ranseyer/CUN-STM32/Datasheets/CUBE_OWIRE.jpg

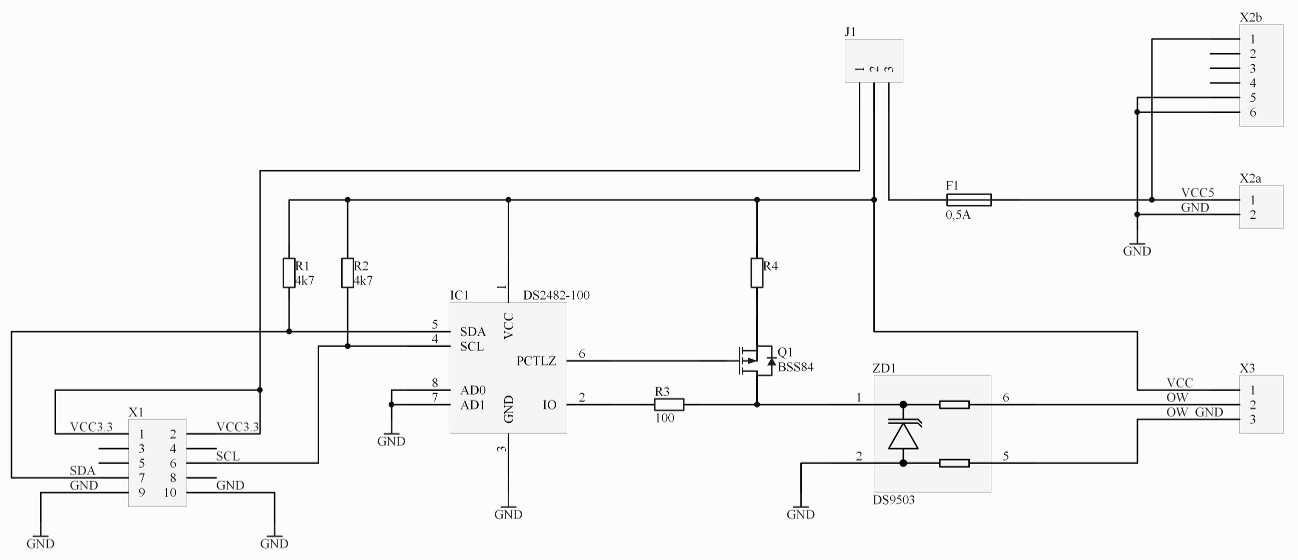
Datasheets/CUBE_OWIRE.jpg
