ranseyer/CUN-STM32/Datasheets/w5500-NiRen2.jpg

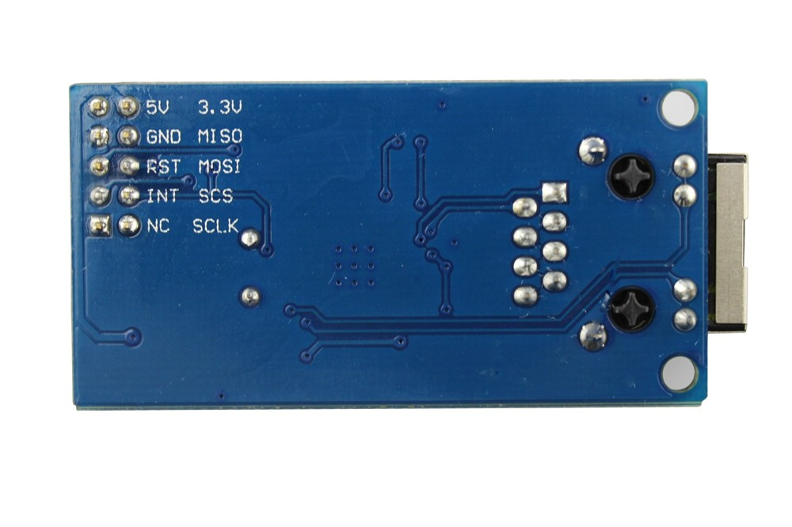
Datasheets/w5500-NiRen2.jpg
