ranseyer/CUN-STM32/Datasheets/w5500-NiRen.jpg

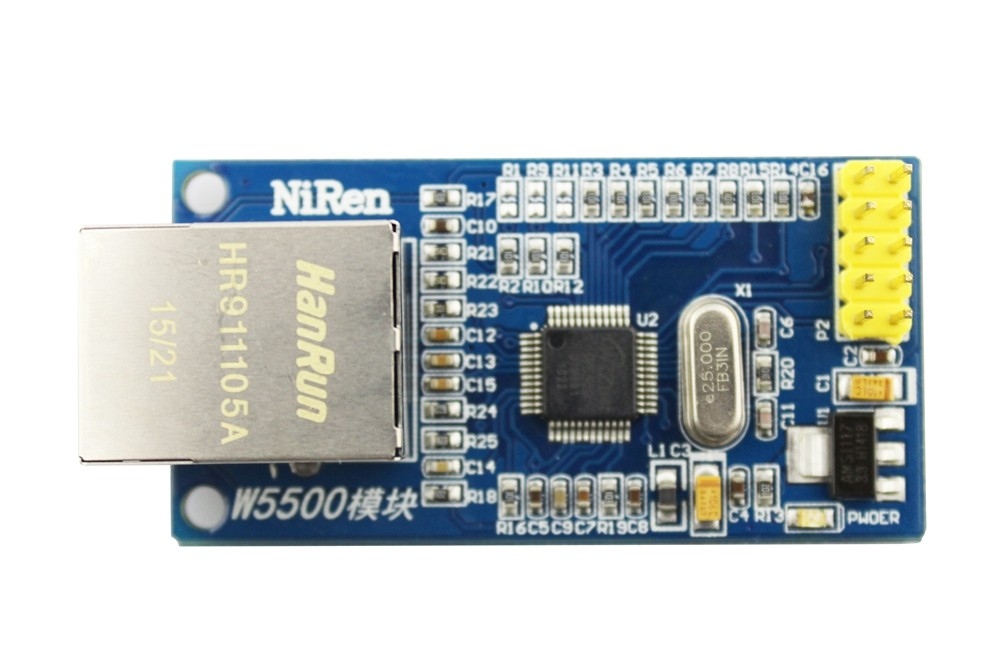
Datasheets/w5500-NiRen.jpg
