ranseyer/CUN-STM32/HW-MAPLE-Large/20161227_2025_top_gold_with_mask.png

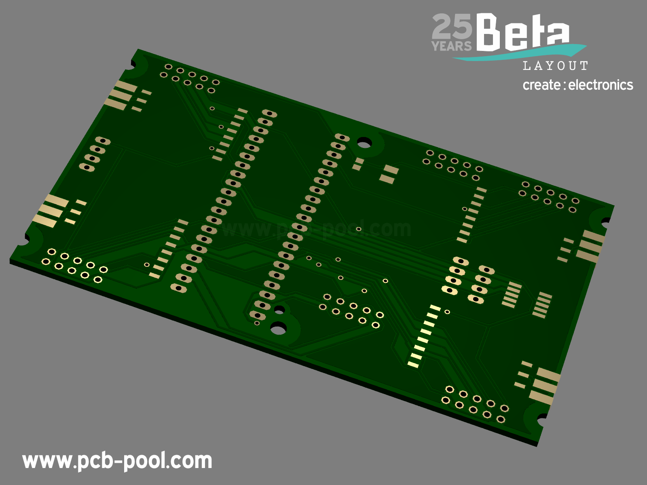
HW-MAPLE-Large/20161227_2025_top_gold_with_mask.png
