ranseyer/CUN-STM32/HW-MAPLE-Large/AddOns/1W_RS485__or__LAN-without-MAPLE/bot.png

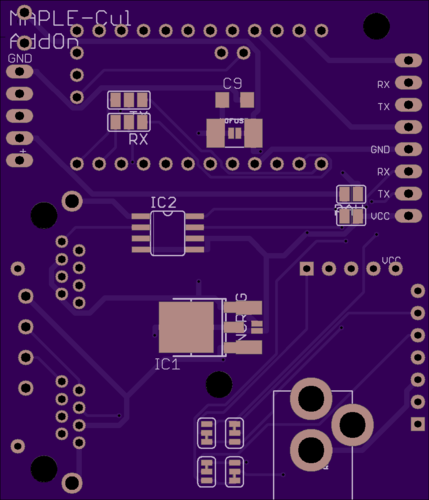
HW-MAPLE-Large/AddOns/1W_RS485__or__LAN-without-MAPLE/bot.png
