ranseyer/CUN-STM32/HW-MAPLE-Large/AddOns/1W_RS485__or__LAN-without-MAPLE/top.png

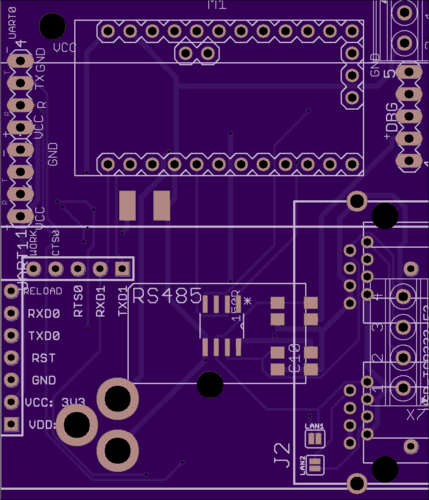
HW-MAPLE-Large/AddOns/1W_RS485__or__LAN-without-MAPLE/top.png
