ranseyer/CUN-STM32/HW-MAPLE-Large/AddOns/Overview.jpg

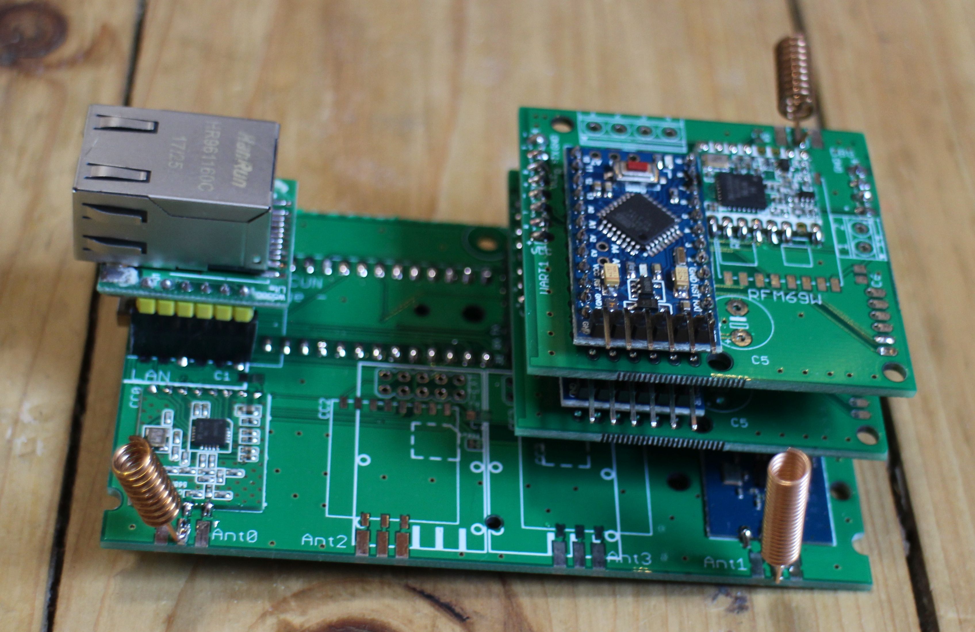
HW-MAPLE-Large/AddOns/Overview.jpg
