ranseyer/CUN-STM32/HW-MAPLE-Large/AddOns/RasPi-UART__Zigbee-CC2530/bot-v04.png

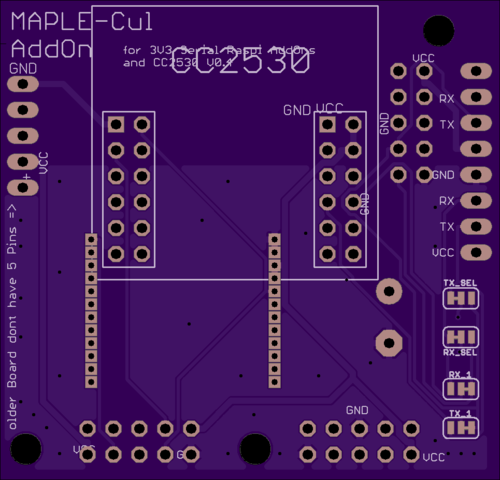
HW-MAPLE-Large/AddOns/RasPi-UART__Zigbee-CC2530/bot-v04.png
