ranseyer/CUN-STM32/HW-MAPLE-Large/AddOns/RasPi-UART__Zigbee-CC2530/bot.png

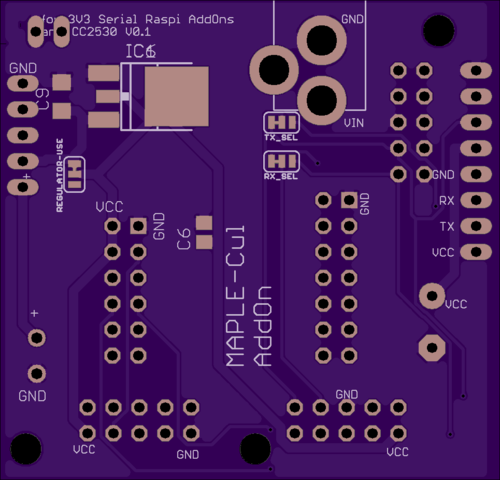
HW-MAPLE-Large/AddOns/RasPi-UART__Zigbee-CC2530/bot.png
