ranseyer/CUN-STM32/HW-MAPLE-Large/AddOns/RasPi-UART__Zigbee-CC2530/CC2530-Photo.jpg

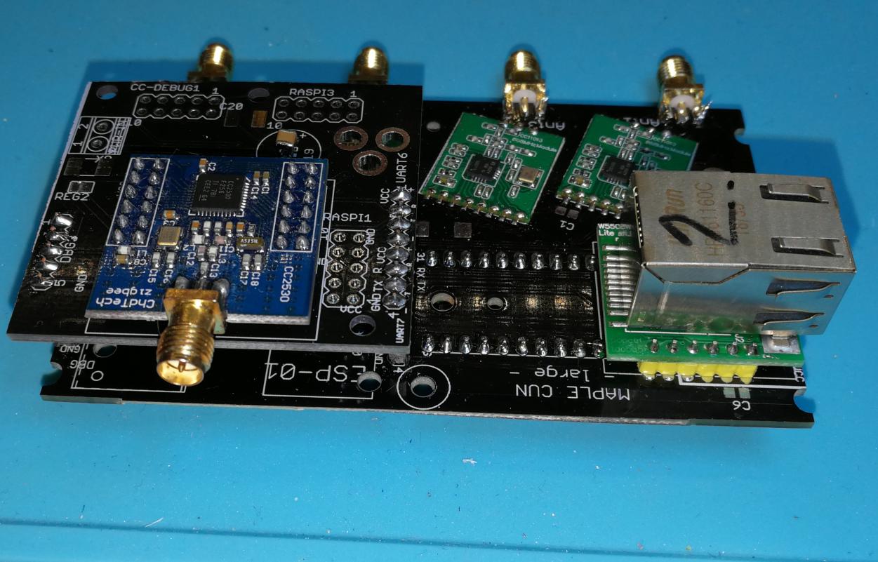
HW-MAPLE-Large/AddOns/RasPi-UART__Zigbee-CC2530/CC2530-Photo.jpg
