ranseyer/CUN-STM32/HW-MAPLE-Large/AddOns/RasPi-UART__Zigbee-CC2530/top.png

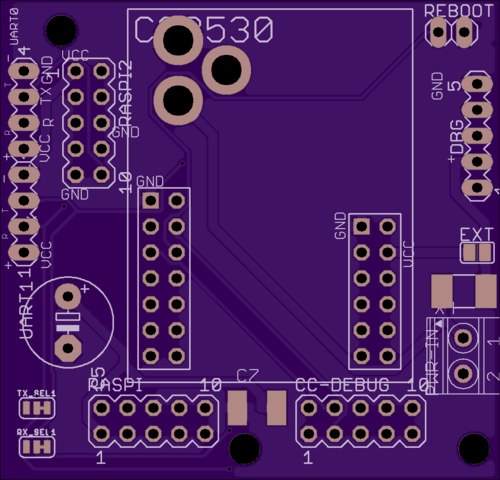
HW-MAPLE-Large/AddOns/RasPi-UART__Zigbee-CC2530/top.png
