ranseyer/CUN-STM32/HW-MAPLE-Large/AddOns/RasPi-UART__Zigbee-CC2530/Zigbee/L01_SL500_.jpg

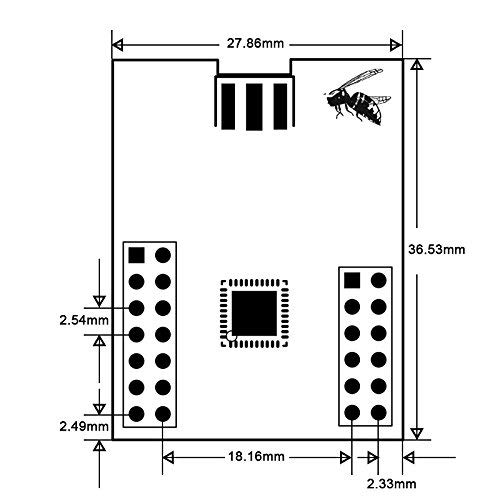
HW-MAPLE-Large/AddOns/RasPi-UART__Zigbee-CC2530/Zigbee/L01_SL500_.jpg
