ranseyer/CUN-STM32/HW-MAPLE-Large/AddOns/RFM69-usw-aktuell/top-14.png

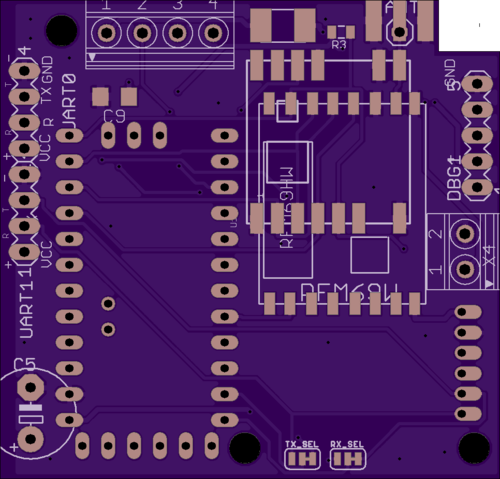
HW-MAPLE-Large/AddOns/RFM69-usw-aktuell/top-14.png
