ranseyer/CUN-STM32/HW-MAPLE-Large/AddOns/RFM69-usw-V11/bot.png

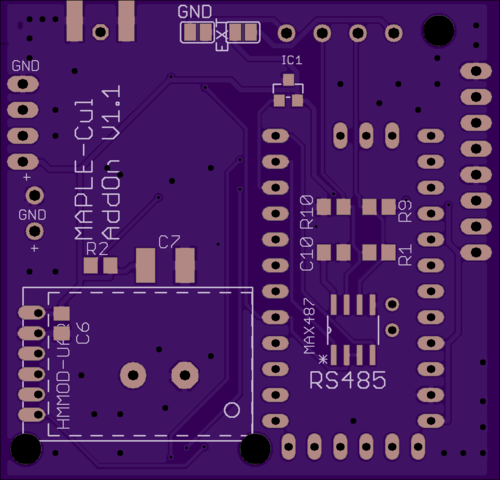
HW-MAPLE-Large/AddOns/RFM69-usw-V11/bot.png
