ranseyer/CUN-STM32/HW-MAPLE-Large/AddOns/separated.jpg

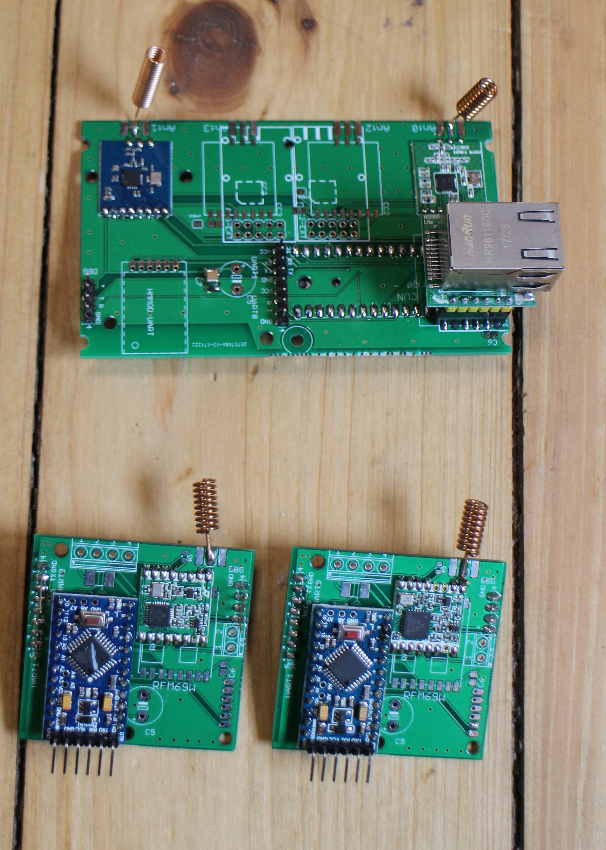
HW-MAPLE-Large/AddOns/separated.jpg
