ranseyer/CUN-STM32/HW-MAPLE-Large/AddOns/V3-Top-Add-1280.jpg

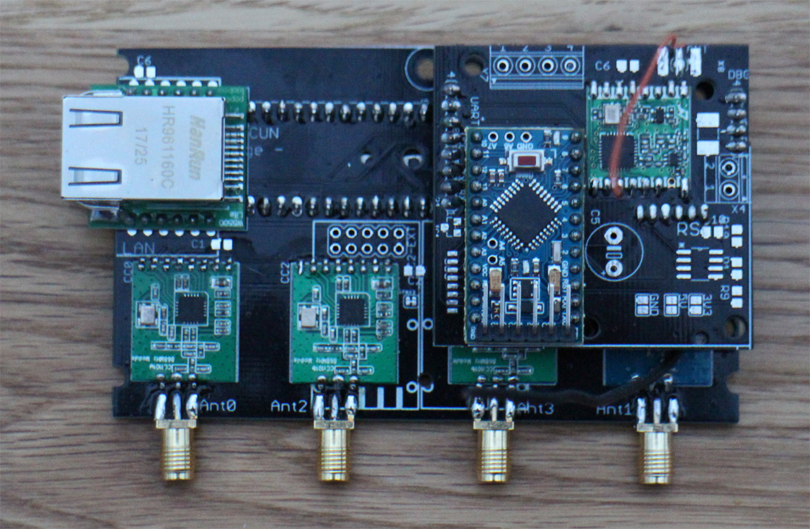
HW-MAPLE-Large/AddOns/V3-Top-Add-1280.jpg
