ranseyer/CUN-STM32/HW-MAPLE-Large/AddOns/zz_delete/1Wire-V01/PCB.png

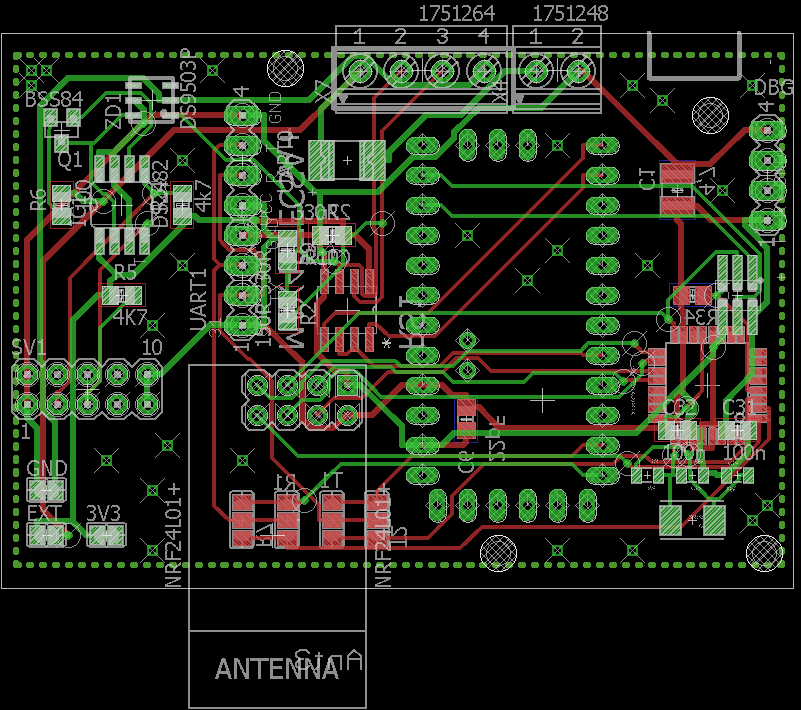
HW-MAPLE-Large/AddOns/zz_delete/1Wire-V01/PCB.png
