ranseyer/CUN-STM32/HW-MAPLE-Large/AddOns/zz_delete/1Wire-V01/Schematic.png

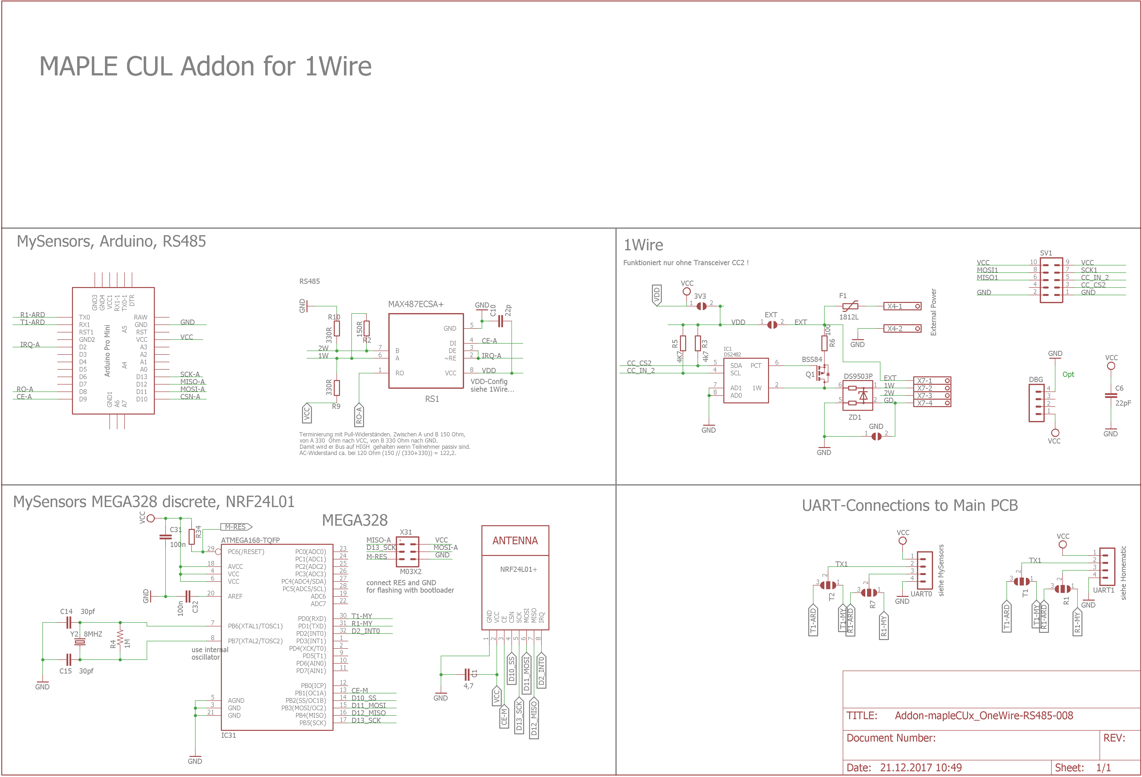
HW-MAPLE-Large/AddOns/zz_delete/1Wire-V01/Schematic.png
