ranseyer/CUN-STM32/HW-MAPLE-Large/Board-V41-bot.png

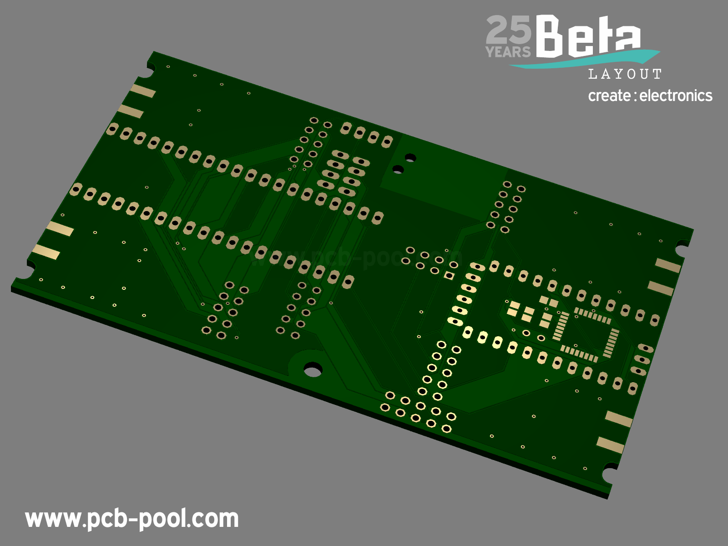
HW-MAPLE-Large/Board-V41-bot.png
