ranseyer/CUN-STM32/HW-MAPLE-Large/Board-V41-top.png

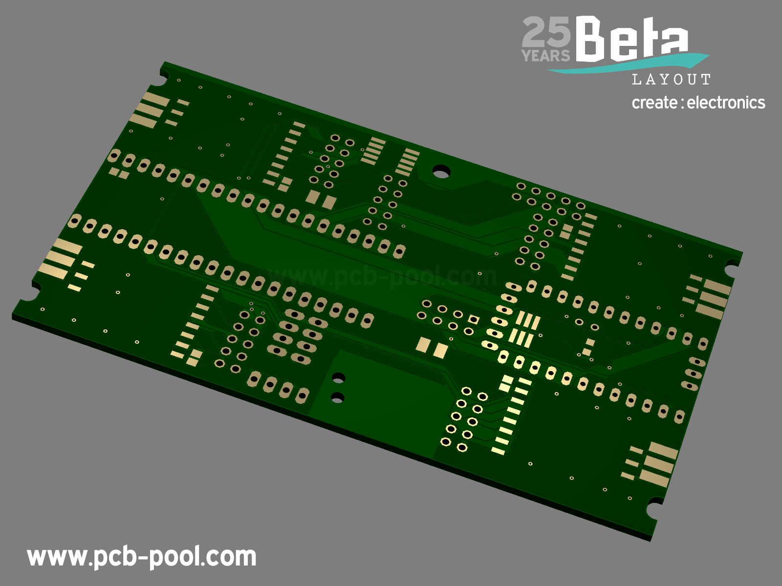
HW-MAPLE-Large/Board-V41-top.png
