ranseyer/CUN-STM32/HW-MAPLE-Large/Board-V41.png

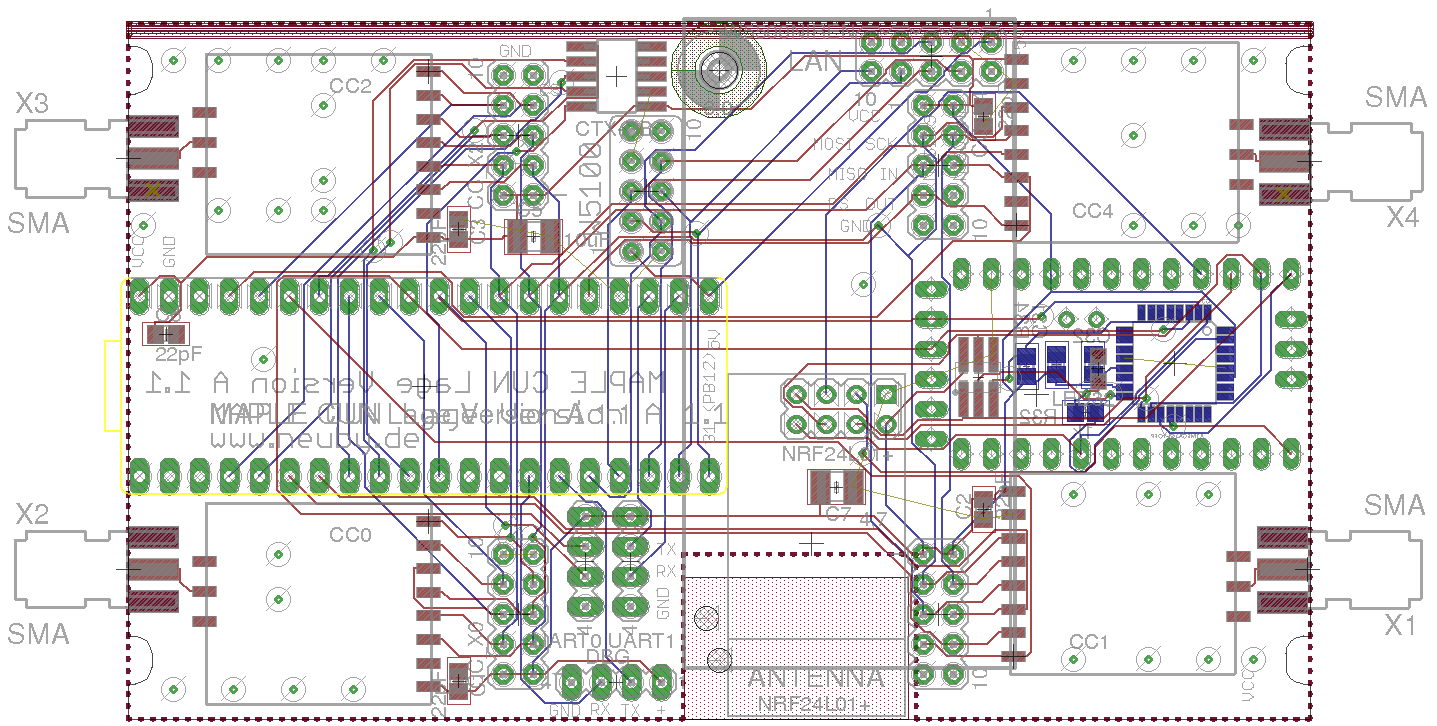
HW-MAPLE-Large/Board-V41.png
