ranseyer/CUN-STM32/HW-MAPLE-Large/Board-V102.png

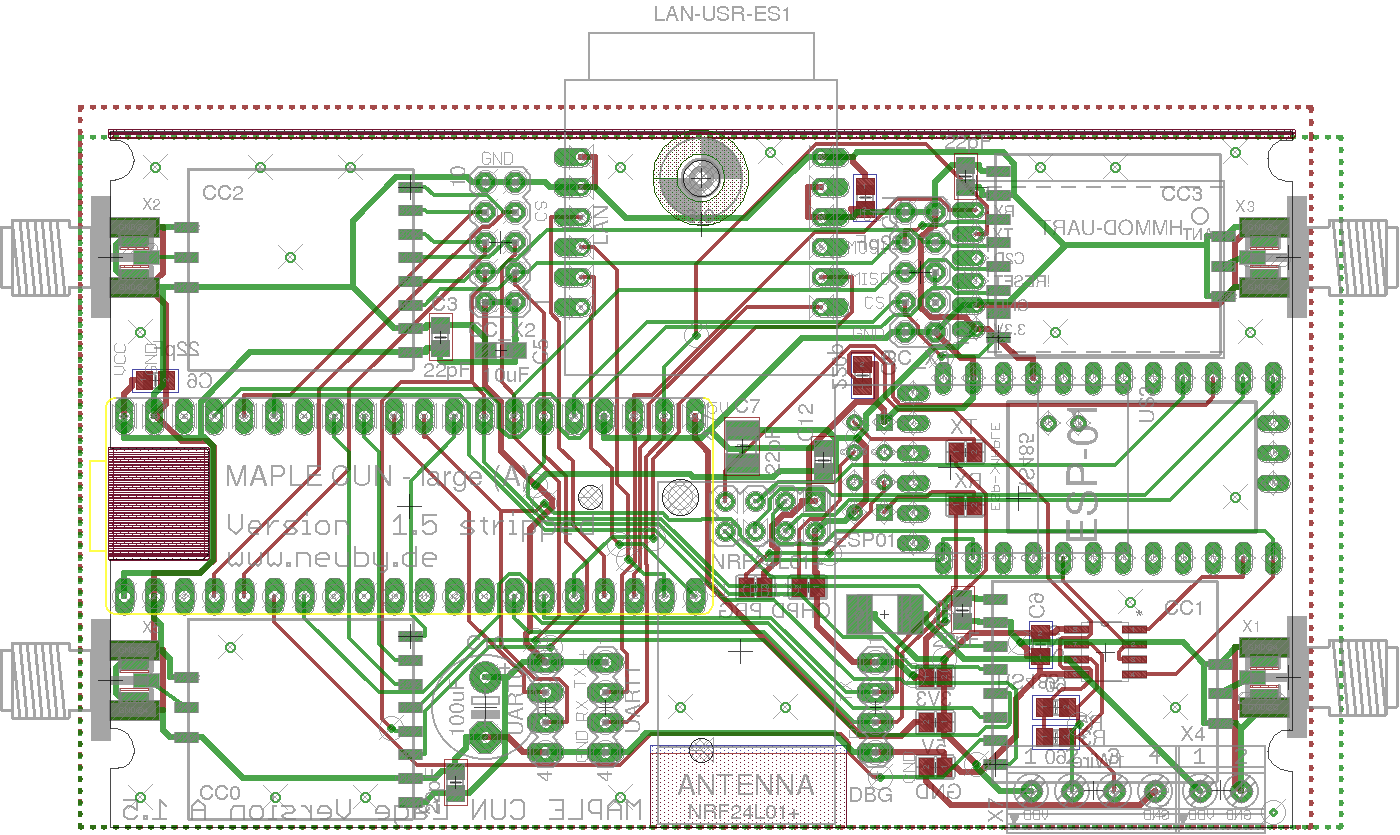
HW-MAPLE-Large/Board-V102.png
