ranseyer/CUN-STM32/HW-MAPLE-Large/Board.png

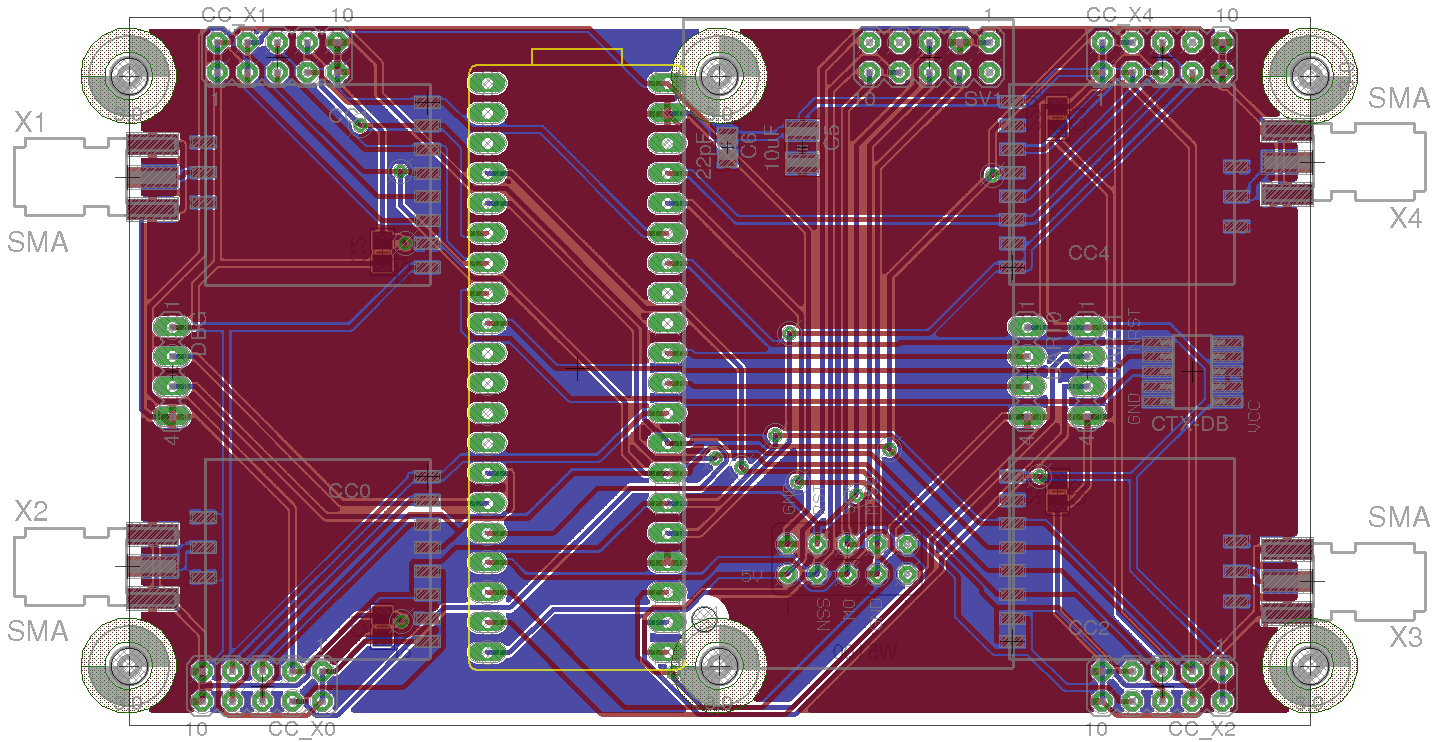
HW-MAPLE-Large/Board.png
