ranseyer/CUN-STM32/HW-MAPLE-Large/Case-Gloob-v001-stack.jpg

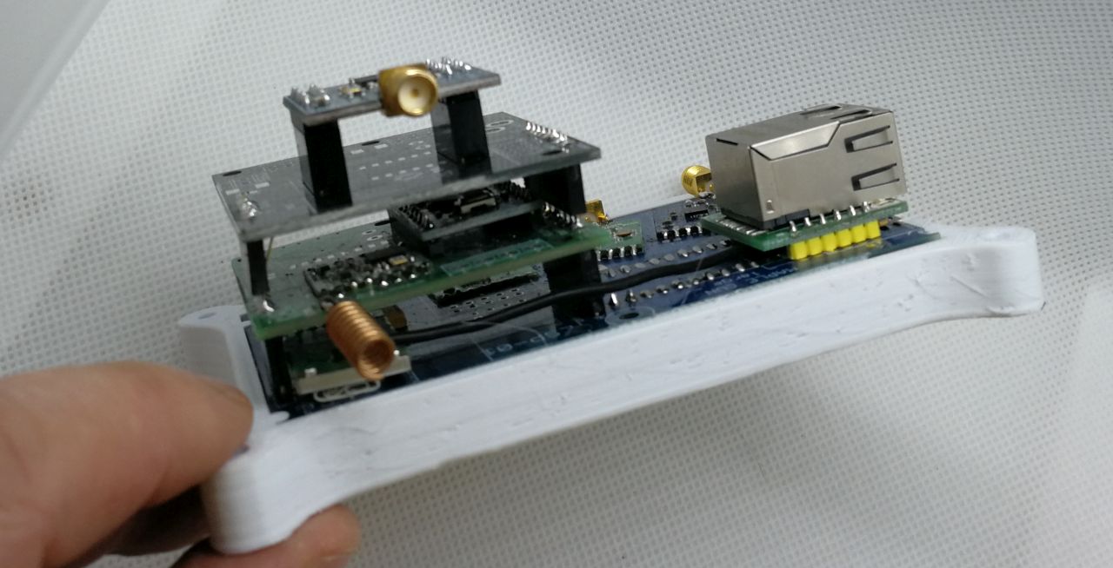
HW-MAPLE-Large/Case-Gloob-v001-stack.jpg
