ranseyer/CUN-STM32/HW-MAPLE-Large/Case-Gloob-v001.jpg

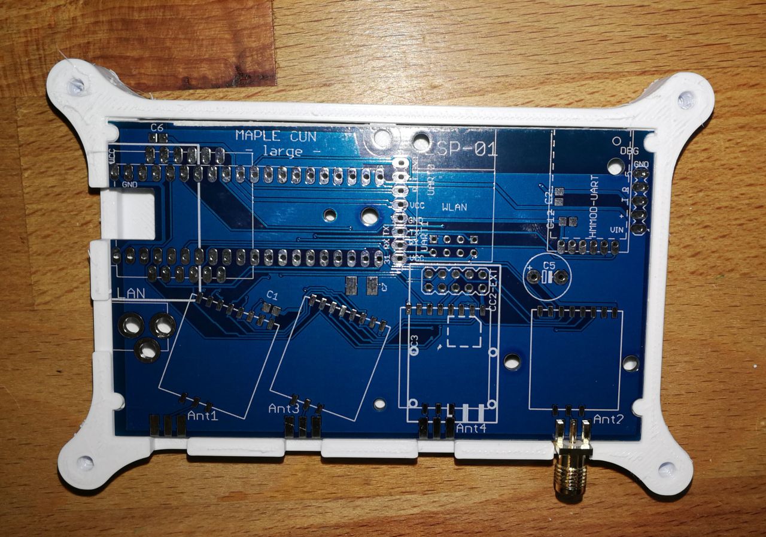
HW-MAPLE-Large/Case-Gloob-v001.jpg
