ranseyer/CUN-STM32/HW-MAPLE-Large/esp-link settings.jpg

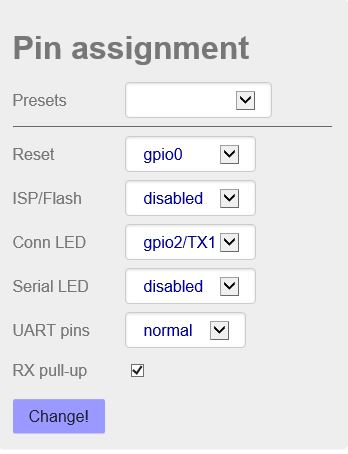
HW-MAPLE-Large/esp-link settings.jpg
