ranseyer/CUN-STM32/HW-MAPLE-Large/MAPLE.jpg

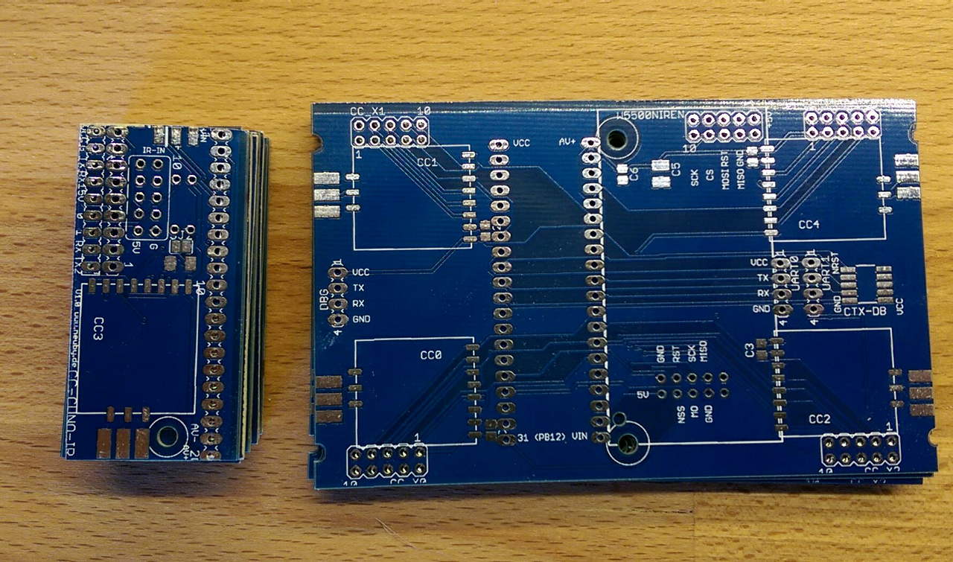
HW-MAPLE-Large/MAPLE.jpg
