ranseyer/CUN-STM32/HW-MAPLE-Large/maple_zigbee_markus.jpg

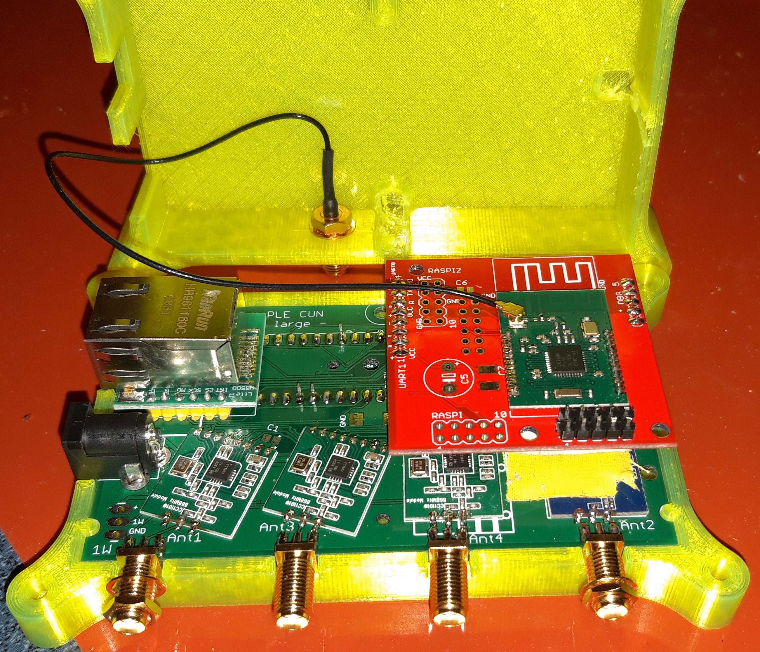
HW-MAPLE-Large/maple_zigbee_markus.jpg
