ranseyer/CUN-STM32/HW-MAPLE-Large/mapleCUx_large_177-bot-cop.png

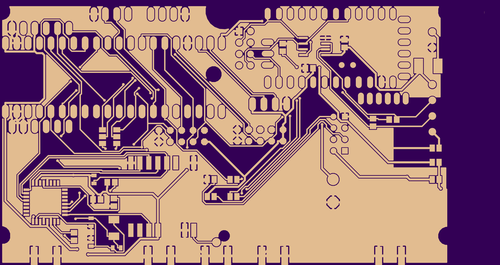
HW-MAPLE-Large/mapleCUx_large_177-bot-cop.png
