ranseyer/CUN-STM32/HW-MAPLE-Large/mapleCUx_large_177-top-cop.png

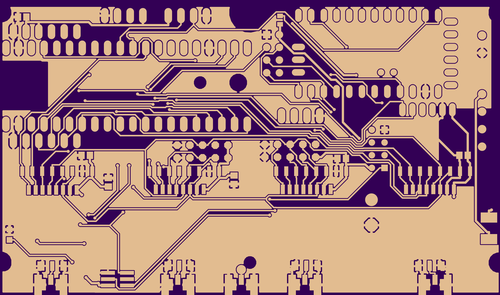
HW-MAPLE-Large/mapleCUx_large_177-top-cop.png
