ranseyer/CUN-STM32/HW-MAPLE-Large/mapleCUx_large_177-top.png

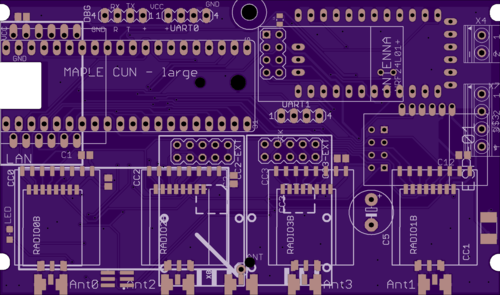
HW-MAPLE-Large/mapleCUx_large_177-top.png
