ranseyer/CUN-STM32/HW-MAPLE-Large/Schematic-V41.png

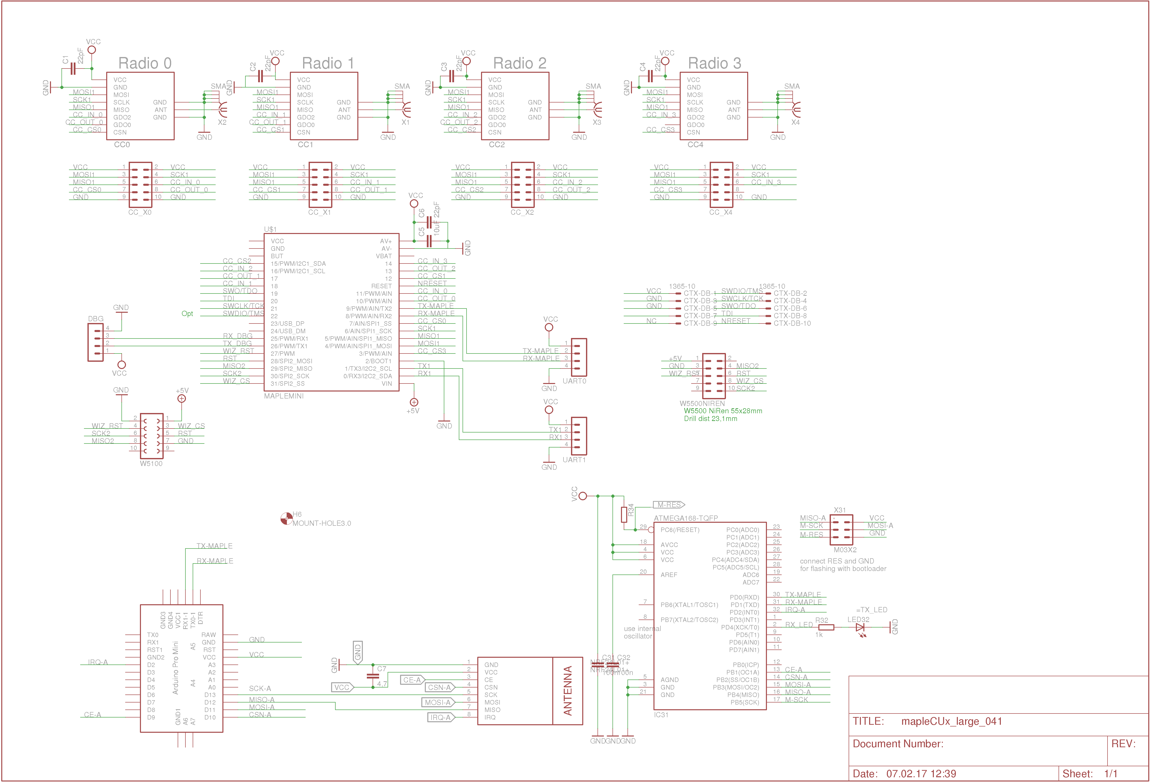
HW-MAPLE-Large/Schematic-V41.png
