ranseyer/CUN-STM32/HW-MAPLE-Large/Schematic.png

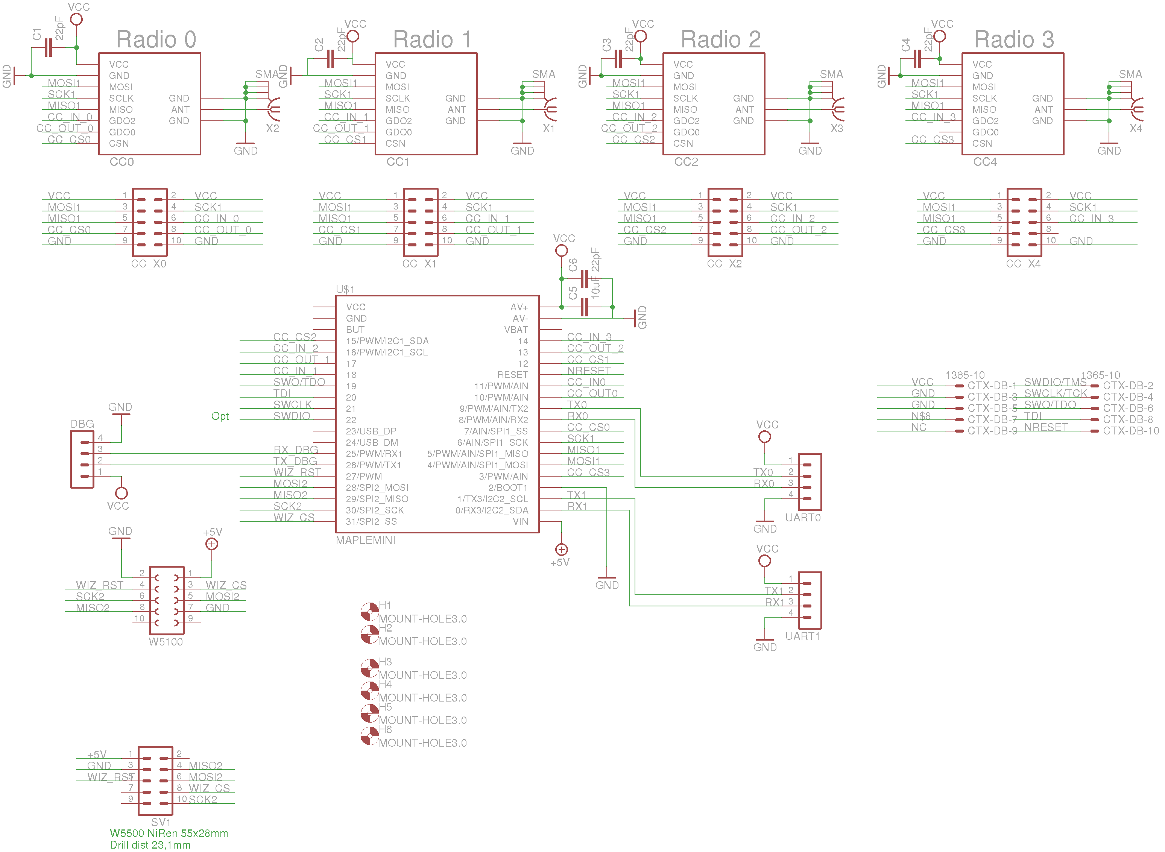
HW-MAPLE-Large/Schematic.png
