ranseyer/CUN-STM32/HW-MAPLE-Large/Stamps/1Wire-Stamp/bot-v02.png

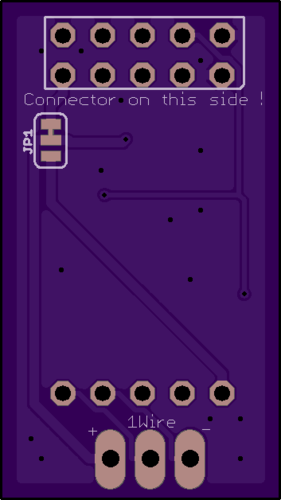
HW-MAPLE-Large/Stamps/1Wire-Stamp/bot-v02.png
