ranseyer/CUN-STM32/HW-MAPLE-Large/Stamps/1Wire-Stamp/bot.png

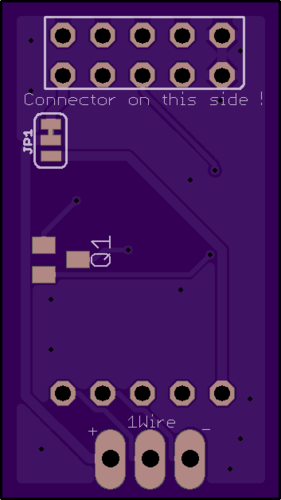
HW-MAPLE-Large/Stamps/1Wire-Stamp/bot.png
