ranseyer/CUN-STM32/HW-MAPLE-Large/Stamps/1Wire-Stamp/top.png

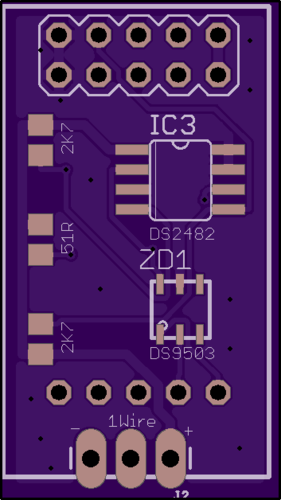
HW-MAPLE-Large/Stamps/1Wire-Stamp/top.png
