ranseyer/CUN-STM32/HW-MAPLE-Large/Stamps/Adapter-for-Stamps/Mini-02-Top-Cop.png

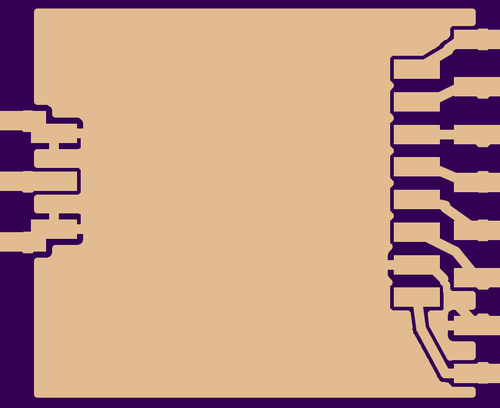
HW-MAPLE-Large/Stamps/Adapter-for-Stamps/Mini-02-Top-Cop.png
