ranseyer/CUN-STM32/HW-MAPLE-Large/Stamps/Adapter-for-Stamps/V02-Bot.png

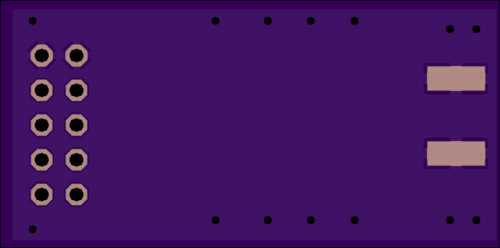
HW-MAPLE-Large/Stamps/Adapter-for-Stamps/V02-Bot.png
