ranseyer/CUN-STM32/HW-MAPLE-Large/Stamps/Adapter-for-Stamps/V02-Top.png

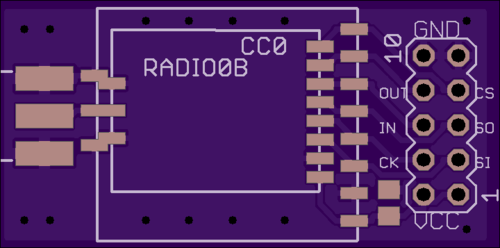
HW-MAPLE-Large/Stamps/Adapter-for-Stamps/V02-Top.png
