ranseyer/CUN-STM32/HW-MAPLE-Large/V4.0/4.1-bot.png

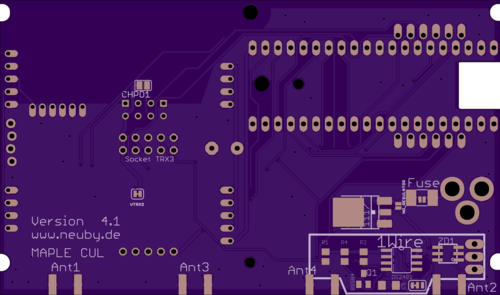
HW-MAPLE-Large/V4.0/4.1-bot.png
