ranseyer/CUN-STM32/HW-MAPLE-Large/V4.0/AddOn-RS485/bot.png

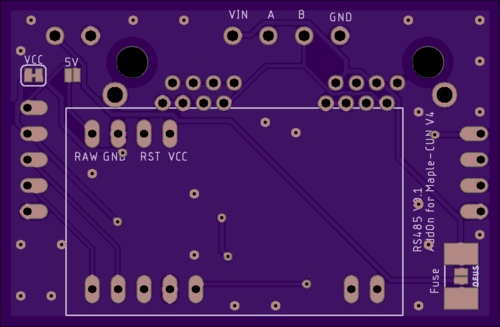
HW-MAPLE-Large/V4.0/AddOn-RS485/bot.png
