ranseyer/CUN-STM32/HW-MAPLE-Large/V4.0/AddOnArduino-RFMx/bot.png

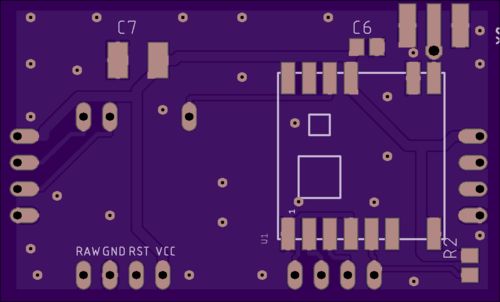
HW-MAPLE-Large/V4.0/AddOnArduino-RFMx/bot.png
