ranseyer/CUN-STM32/HW-MAPLE-Large/V4.0/AddOnArduino-RFMx/top.png

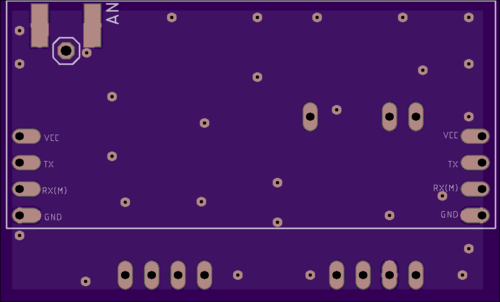
HW-MAPLE-Large/V4.0/AddOnArduino-RFMx/top.png
