ranseyer/CUN-STM32/HW-MAPLE-Large/V4.0/AddOnCC1101/top.png

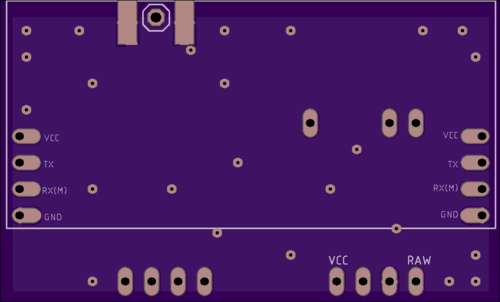
HW-MAPLE-Large/V4.0/AddOnCC1101/top.png
