ranseyer/CUN-STM32/HW-MAPLE-Large/V4.0/AddOnESP32/bot.png

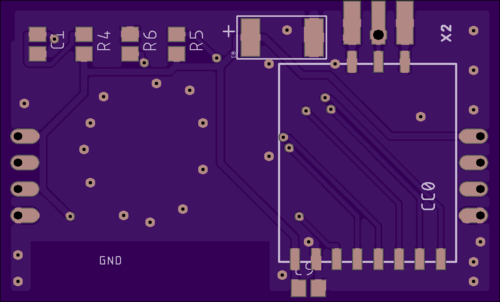
HW-MAPLE-Large/V4.0/AddOnESP32/bot.png
