ranseyer/CUN-STM32/HW-MAPLE-Large/V4.0/AddOnESP32/top.png

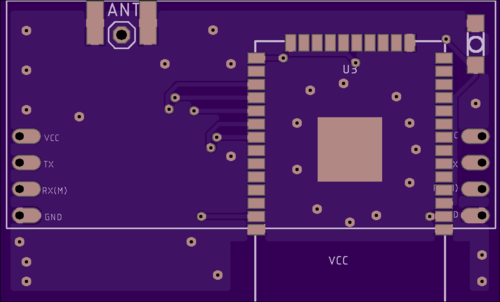
HW-MAPLE-Large/V4.0/AddOnESP32/top.png
