ranseyer/CUN-STM32/HW-MAPLE-Large/V4.0/AddOnRaspiUART/top.png

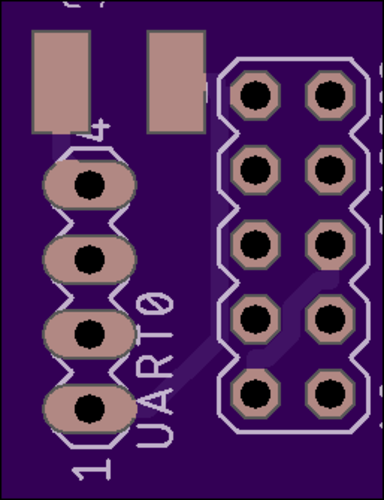
HW-MAPLE-Large/V4.0/AddOnRaspiUART/top.png
