ranseyer/CUN-STM32/HW-MAPLE-Large/V4.0/AddOnZigbee-DIL/bot.png

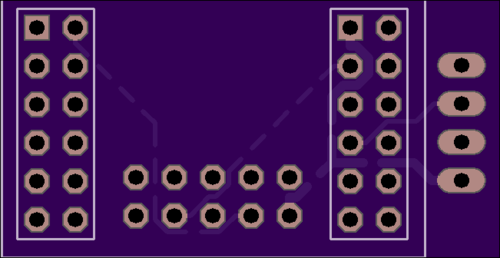
HW-MAPLE-Large/V4.0/AddOnZigbee-DIL/bot.png
