ranseyer/CUN-STM32/HW-MAPLE-Large/V4.0/Carrier-Board_for-AddOns_without_Maple-CUL/carrier-bot.png

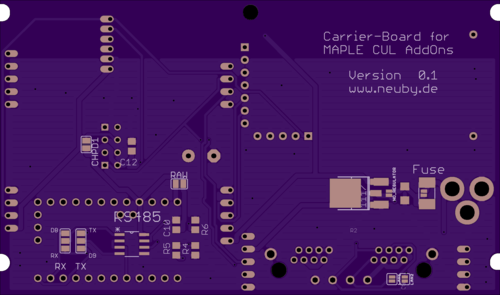
HW-MAPLE-Large/V4.0/Carrier-Board_for-AddOns_without_Maple-CUL/carrier-bot.png
