ranseyer/CUN-STM32/HW-MAPLE-Small/Board-031.png

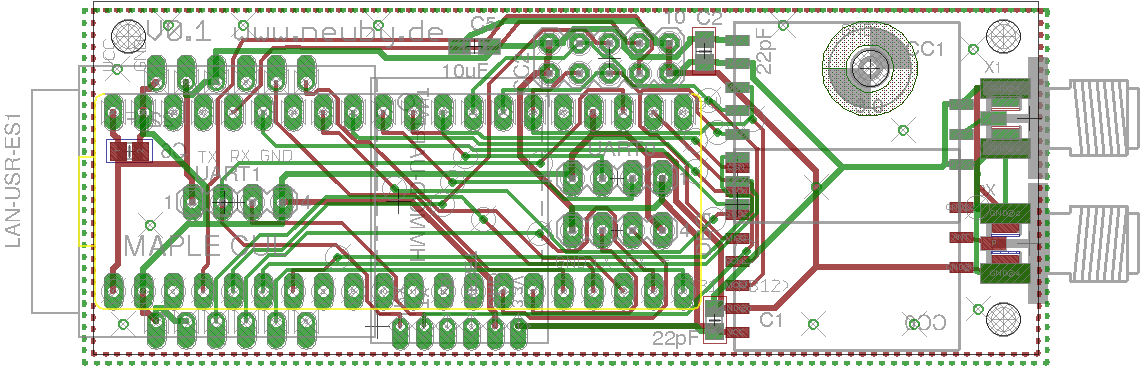
HW-MAPLE-Small/Board-031.png
