ranseyer/CUN-STM32/HW-MAPLE-Small/Board.png

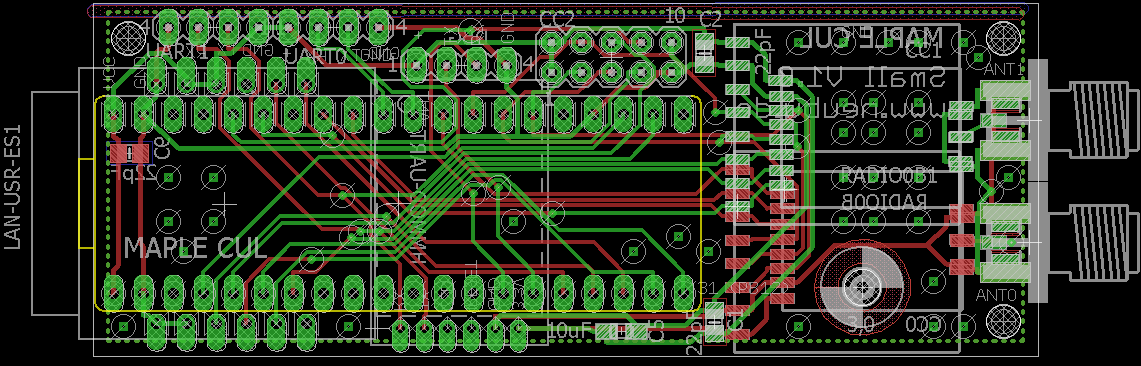
HW-MAPLE-Small/Board.png
