ranseyer/CUN-STM32/HW-MAPLE-Small/bot.png

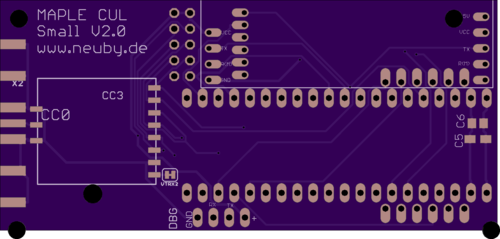
HW-MAPLE-Small/bot.png
