ranseyer/CUN-STM32/HW-MAPLE-Small/BRD-Bot031.png

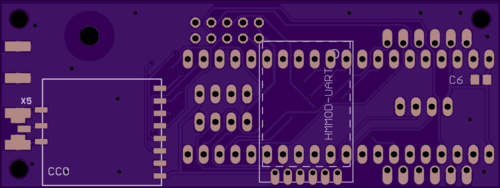
HW-MAPLE-Small/BRD-Bot031.png
