ranseyer/CUN-STM32/HW-MAPLE-Small/BRD-Top031.png

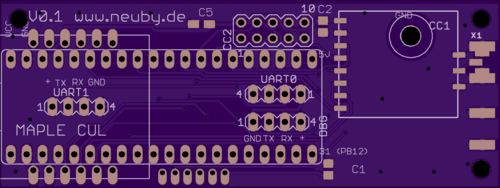
HW-MAPLE-Small/BRD-Top031.png
