ranseyer/CUN-STM32/HW-MAPLE-Small/photo.jpg

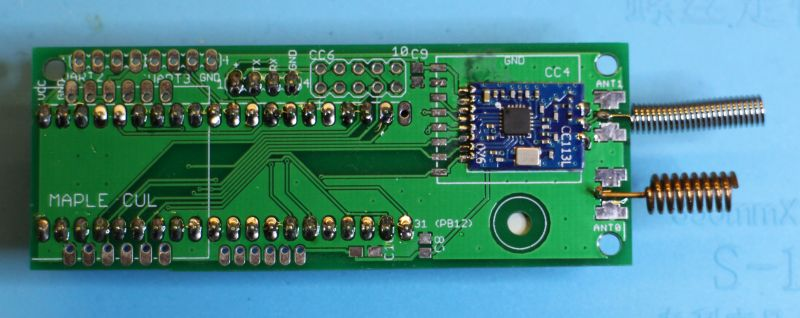
HW-MAPLE-Small/photo.jpg
