ranseyer/CUN-STM32/HW-MAPLE-Small/Schematic-031.png

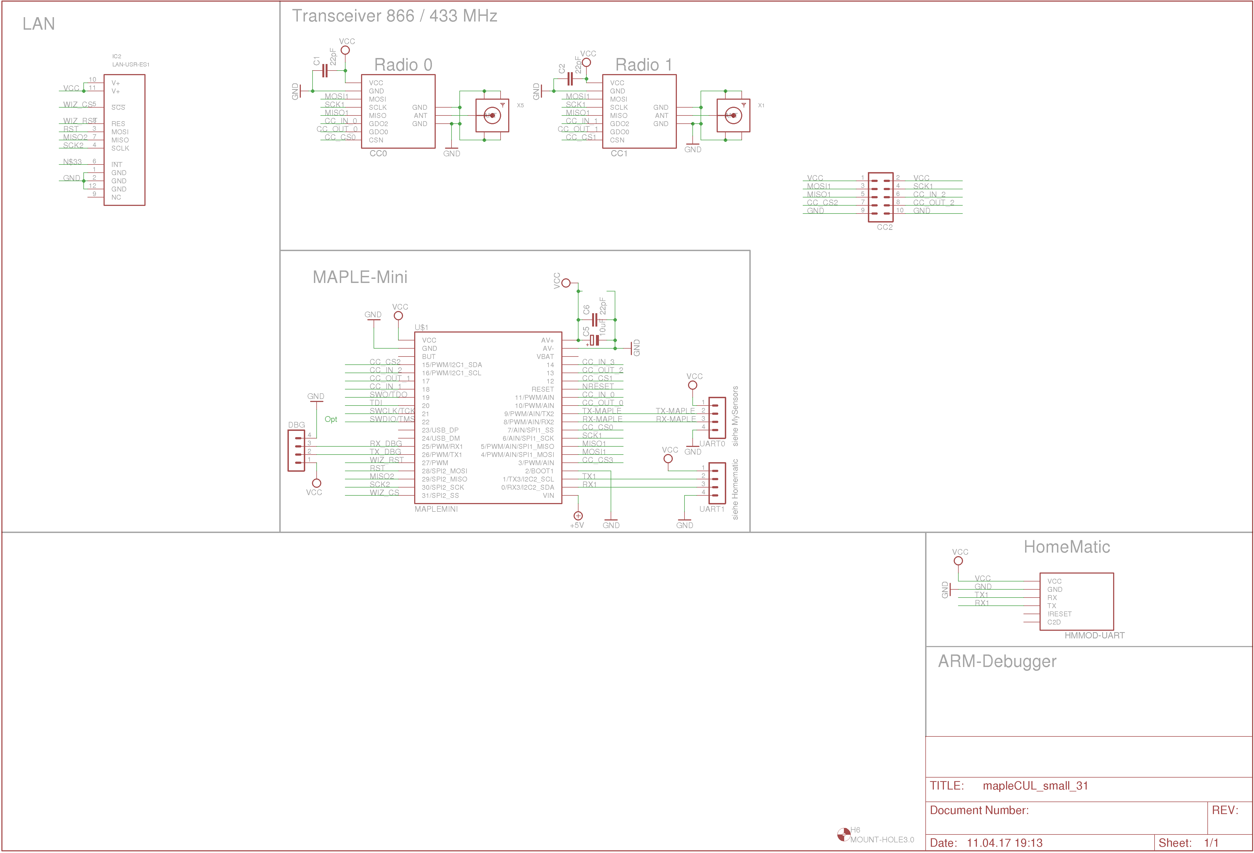
HW-MAPLE-Small/Schematic-031.png
