ranseyer/CUN-STM32/HW-MAPLE-Small/Schematic.png

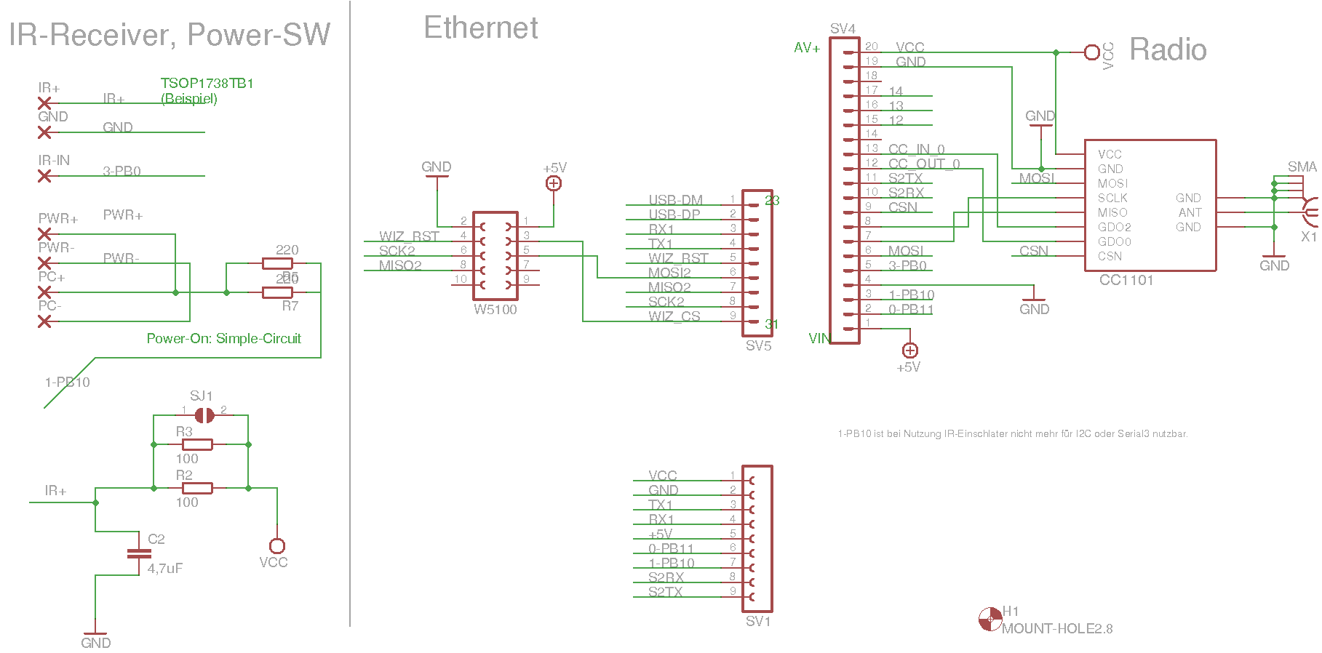
HW-MAPLE-Small/Schematic.png
