ranseyer/CUN-STM32/HW-MAPLE-Small/Small_9051.JPG

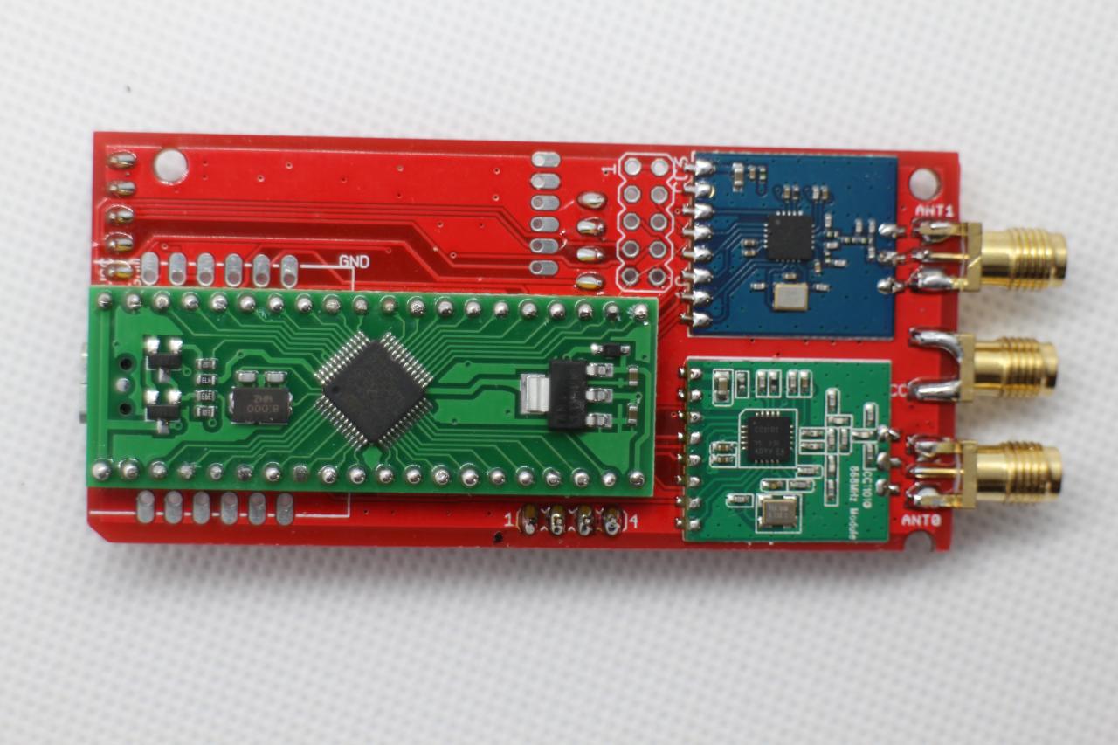
HW-MAPLE-Small/Small_9051.JPG
