ranseyer/CUN-STM32/HW-MAPLE-Small/Small_9053.JPG

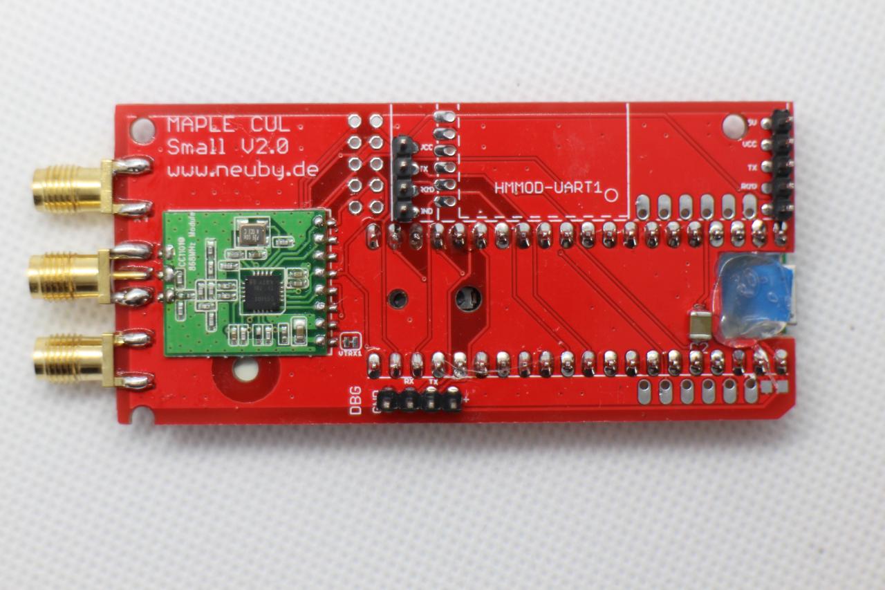
HW-MAPLE-Small/Small_9053.JPG
