ranseyer/CUN-STM32/HW-MAPLE-Small/Small_9055.JPG

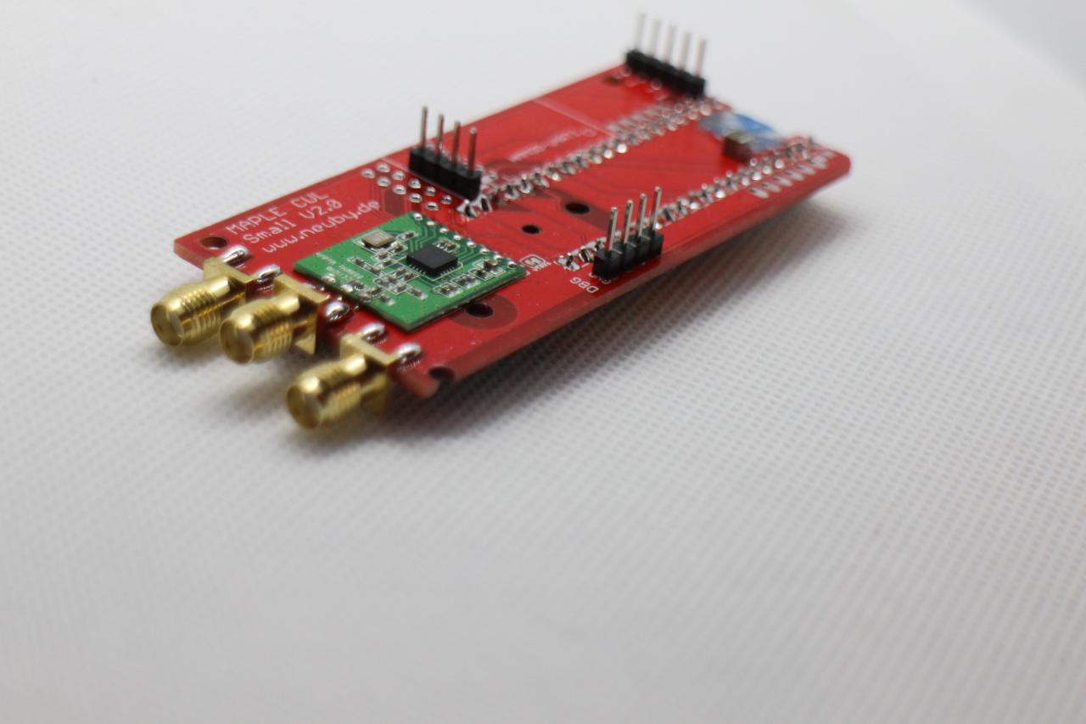
HW-MAPLE-Small/Small_9055.JPG
