ranseyer/CUN-STM32/HW-MAPLE-Small/Small_9056.JPG

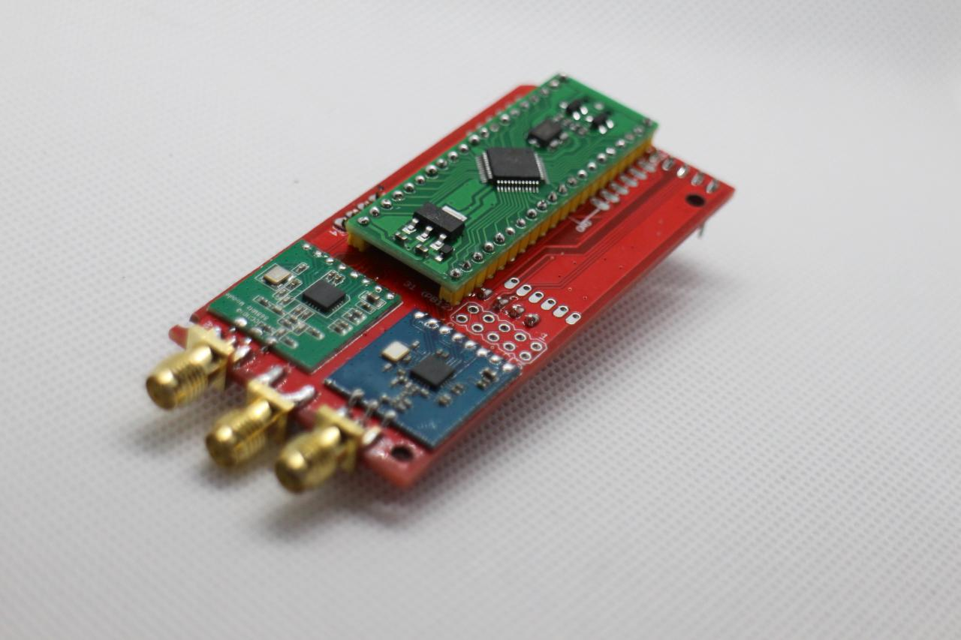
HW-MAPLE-Small/Small_9056.JPG
