ranseyer/CUN-STM32/HW-MAPLE-Small/Small_9058.JPG

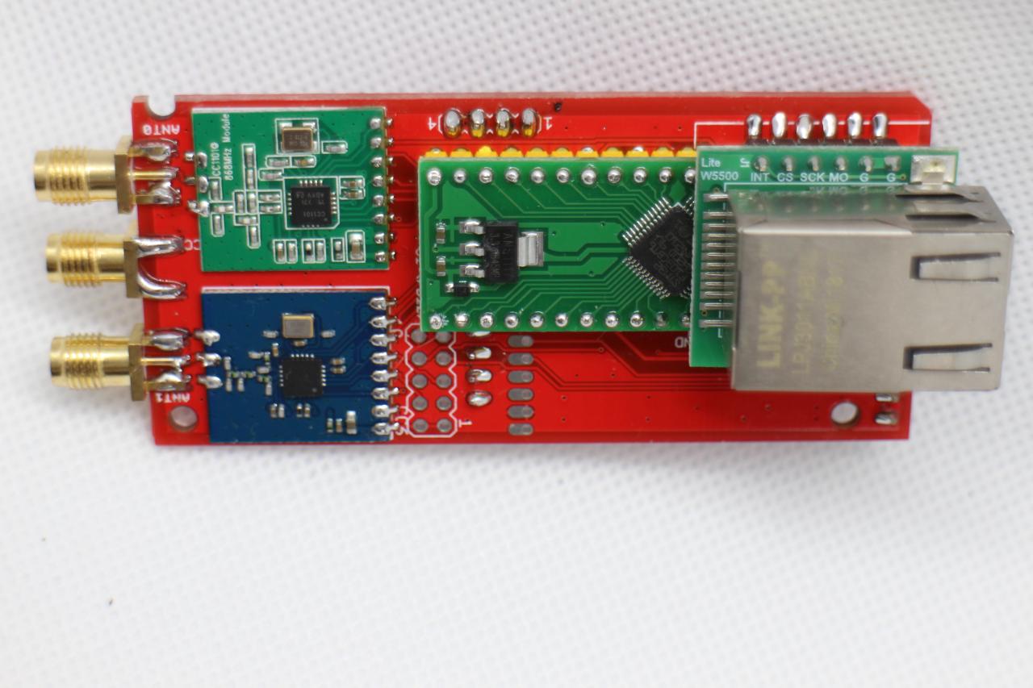
HW-MAPLE-Small/Small_9058.JPG
