ranseyer/CUN-STM32/HW-MAPLE-Small/Small_9059.JPG

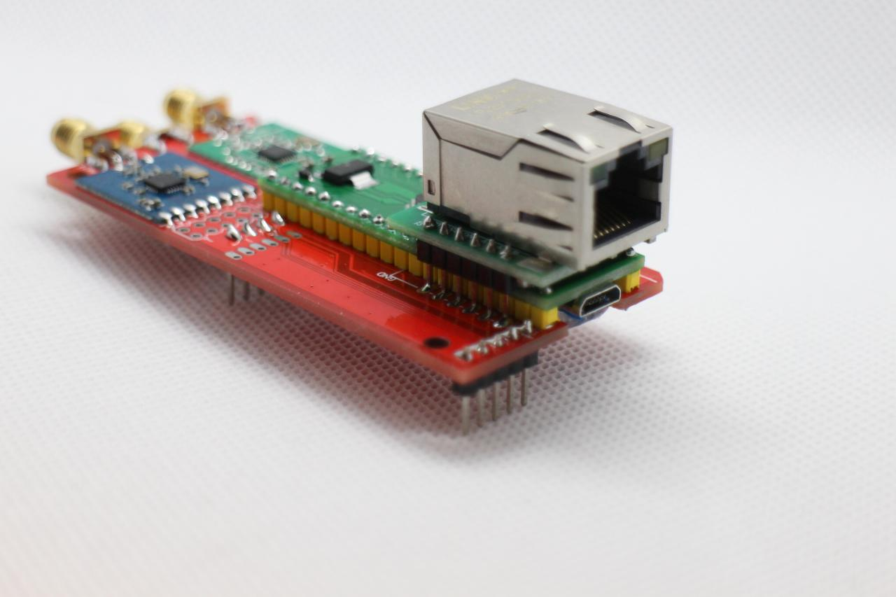
HW-MAPLE-Small/Small_9059.JPG
