ranseyer/CUN-STM32/HW-MAPLE-Small/Small_9060.JPG

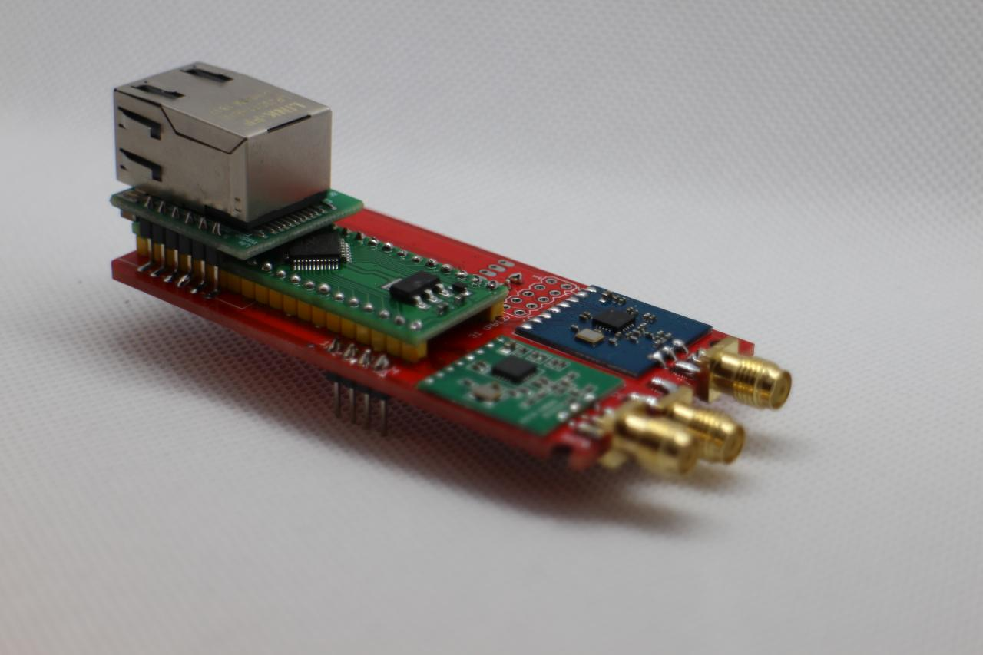
HW-MAPLE-Small/Small_9060.JPG
