ranseyer/CUN-STM32/HW-MAPLE-Small/top.png

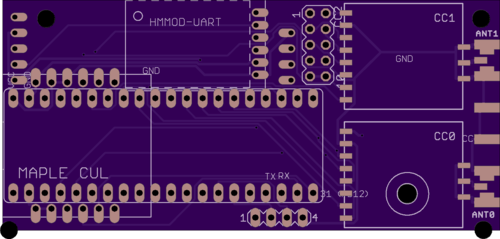
HW-MAPLE-Small/top.png
