ranseyer/CUN-STM32/MapleCUN.jpg

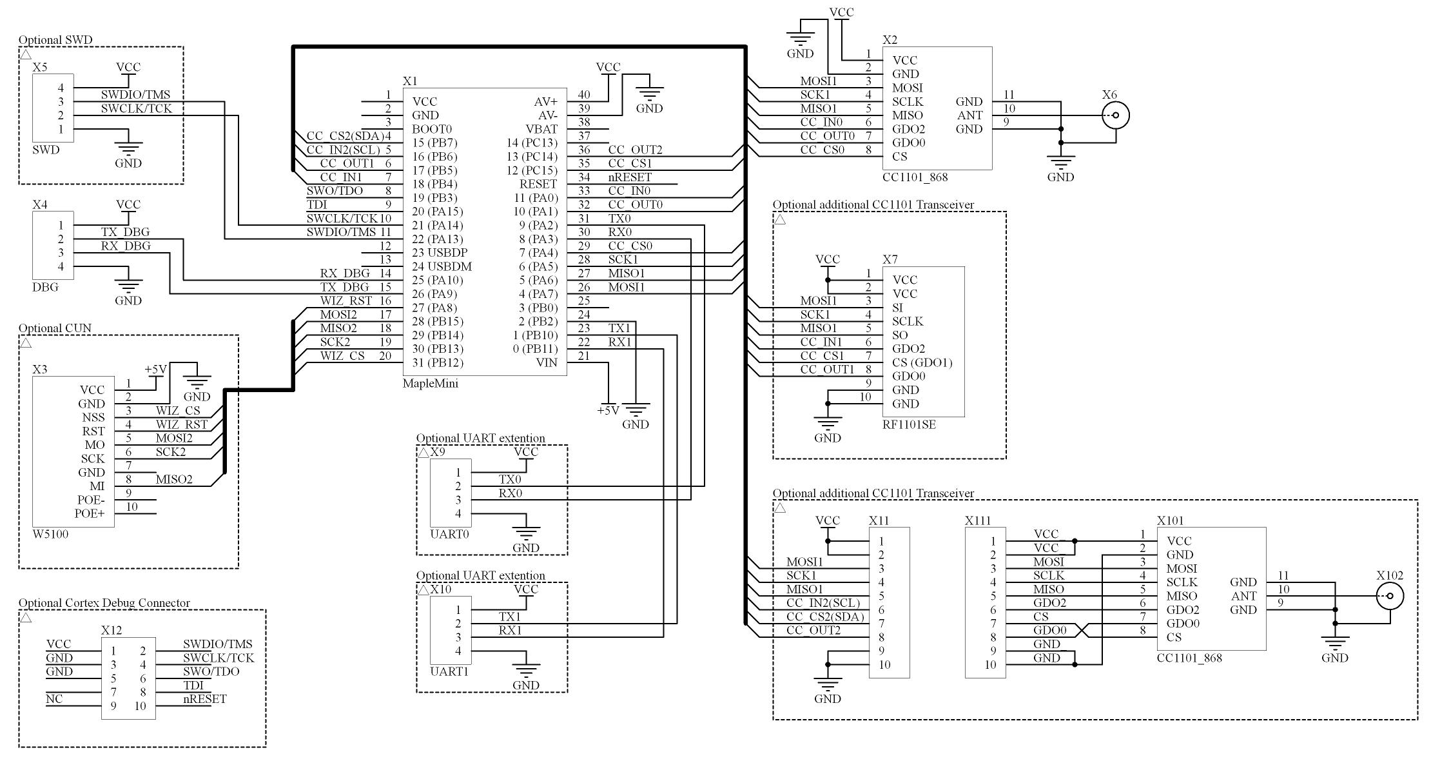
MapleCUN.jpg
