ranseyer/CUN-STM32/zz-Delete/HW-MAPLE-Med/Board-24.png

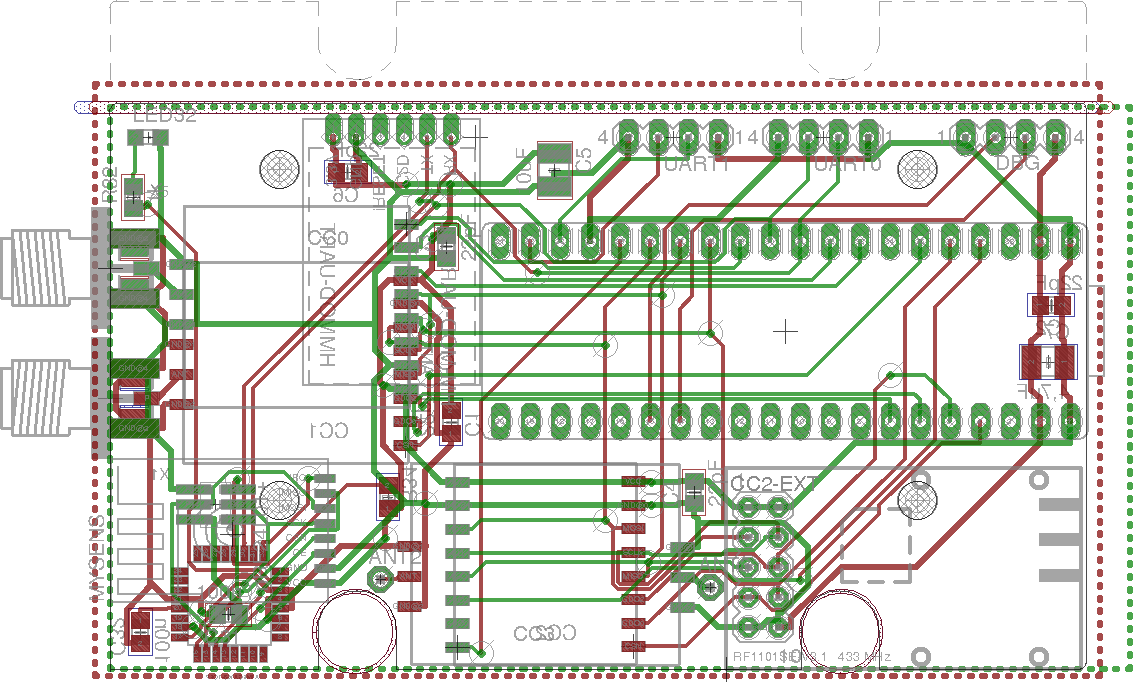
zz-Delete/HW-MAPLE-Med/Board-24.png
