ranseyer/CUN-STM32/zz-Delete/HW-MAPLE-Med/Schematic-24.png

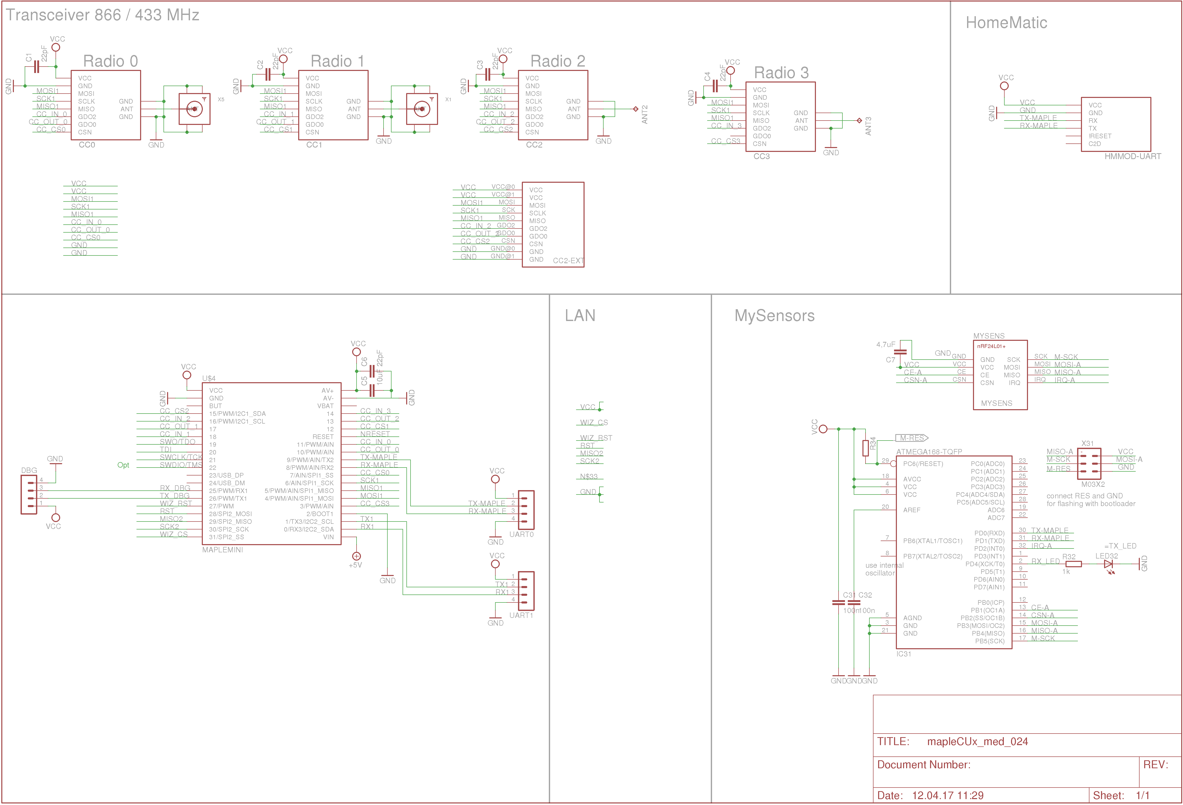
zz-Delete/HW-MAPLE-Med/Schematic-24.png
