ranseyer/CUN-STM32/HW-MAPLE-Large/V4.0/AddOnCC1101/V4-AddOnSduino-V02-009.brd

## EAGLE design HW-MAPLE-Large/V4.0/AddOnCC1101/V4-AddOnSduino-V02-009.brd (2019-07-03)

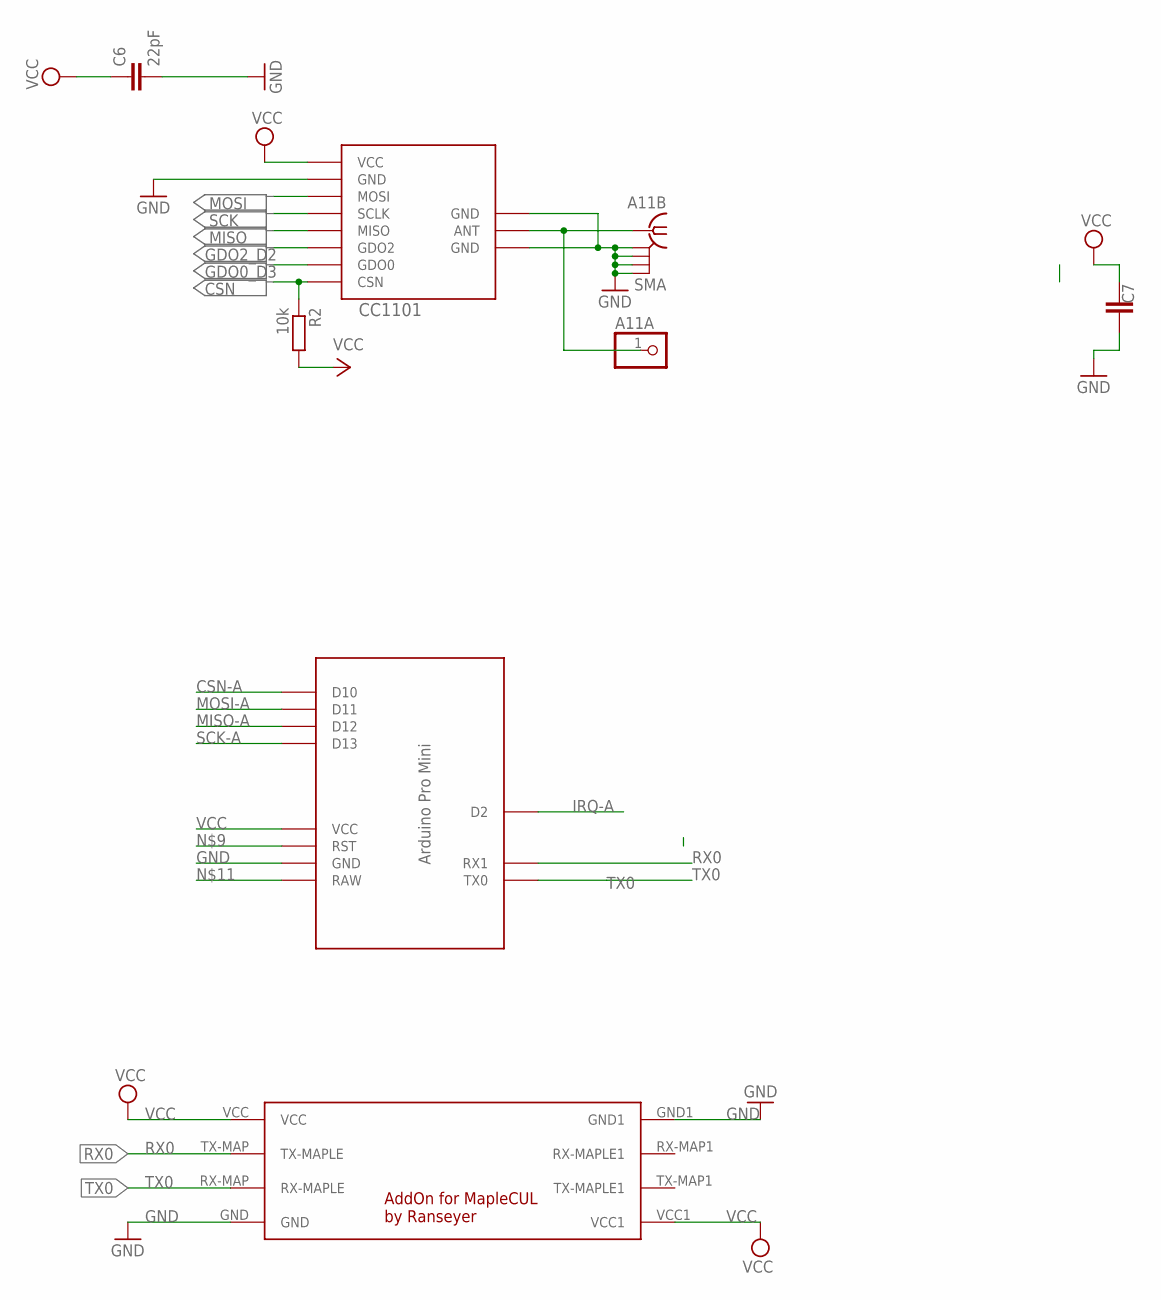
[picture p119: schematic V4-AddOnSduino-V02-009.sch]

Parts:
A11A: PINHD-1X1; 1X01
A11B: SMA
C6: 22pF; C0805
C7: C-EUC1812; C1812
CC1101: CC1101_MODULE1SMD; CC1101_MODULE1_SMD
R2: 10k; M0805
U$1: MARTIN-PROMINI-SPI; MARTIN-PRO-SPI
U$2: MAPLE-CUL-ADDON-V01; MAPLE-CUL-V01

Connections:
ANT2: A11A.1, A11B.1, CC1101.ANT
CSN: CC1101.CSN, R2.1
CSN-A: U$1.D10
GDO0_D3: CC1101.GDO0
GDO2_D2: CC1101.GDO2
GND: A11B.GND@1 (2), A11B.GND@2 (3), A11B.GND@3 (4), A11B.GND@4 (5), C6.2, C7.1, CC1101.GND@0 (GND), CC1101.GND@1 (GND), CC1101.GND@2 (GND), U$1.GND, U$2.GND, U$2.GND1
IRQ-A: U$1.D2
MISO: CC1101.MISO
MISO-A: U$1.D12
MOSI: CC1101.MOSI
MOSI-A: U$1.D11
RX0: U$1.RX1, U$2.TX-MAP (TX-MAPLE)
SCK: CC1101.SCLK
SCK-A: U$1.D13
TX0: U$1.TX0, U$2.RX-MAP (RX-MAPLE)
VCC: C6.1, C7.2, CC1101.VCC, R2.2, U$1.VCC, U$2.VCC, U$2.VCC1

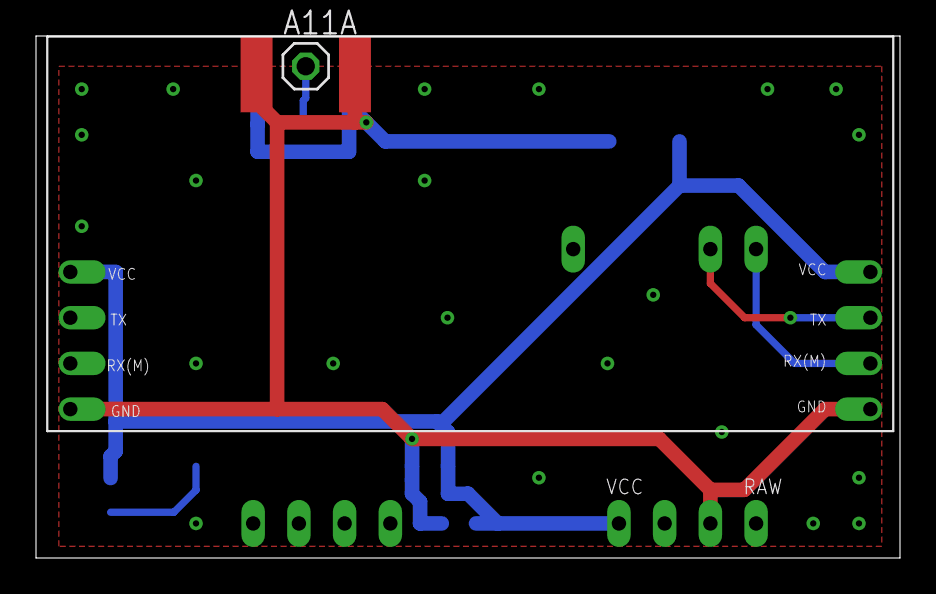
[picture p120: board V4-AddOnSduino-V02-009.brd from above]

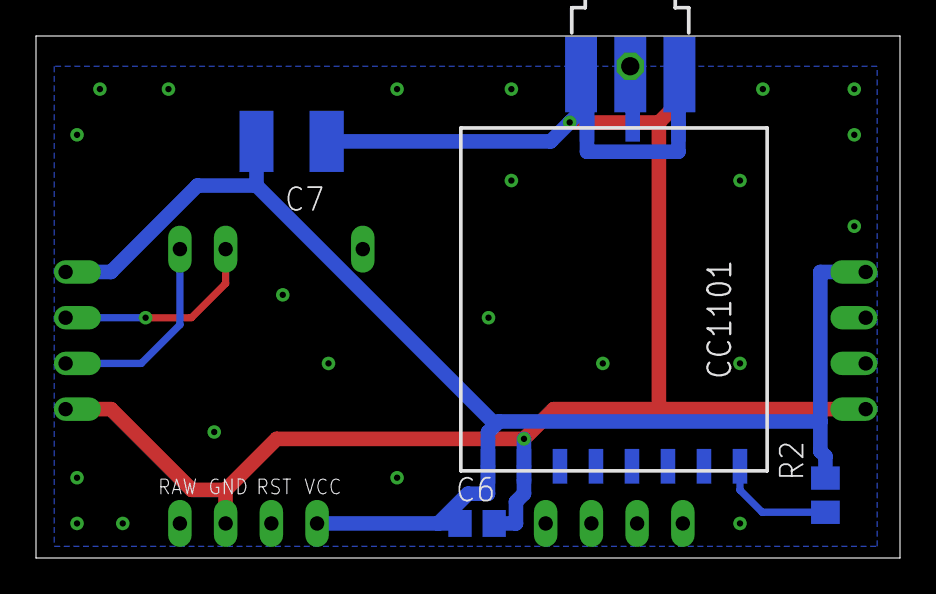
[picture p121: board V4-AddOnSduino-V02-009.brd from below]

Board: 2 copper layers, 48.0 x 29.0 mm, 8 parts (5 on the bottom side), 6 nets.
