ranseyer/CUN-STM32/HW-MAPLE-Large/V4.0/AddOnArduino-RFMx/V4-MySensors-LoRa-V006.brd

## EAGLE design HW-MAPLE-Large/V4.0/AddOnArduino-RFMx/V4-MySensors-LoRa-V006.brd (2019-07-03)

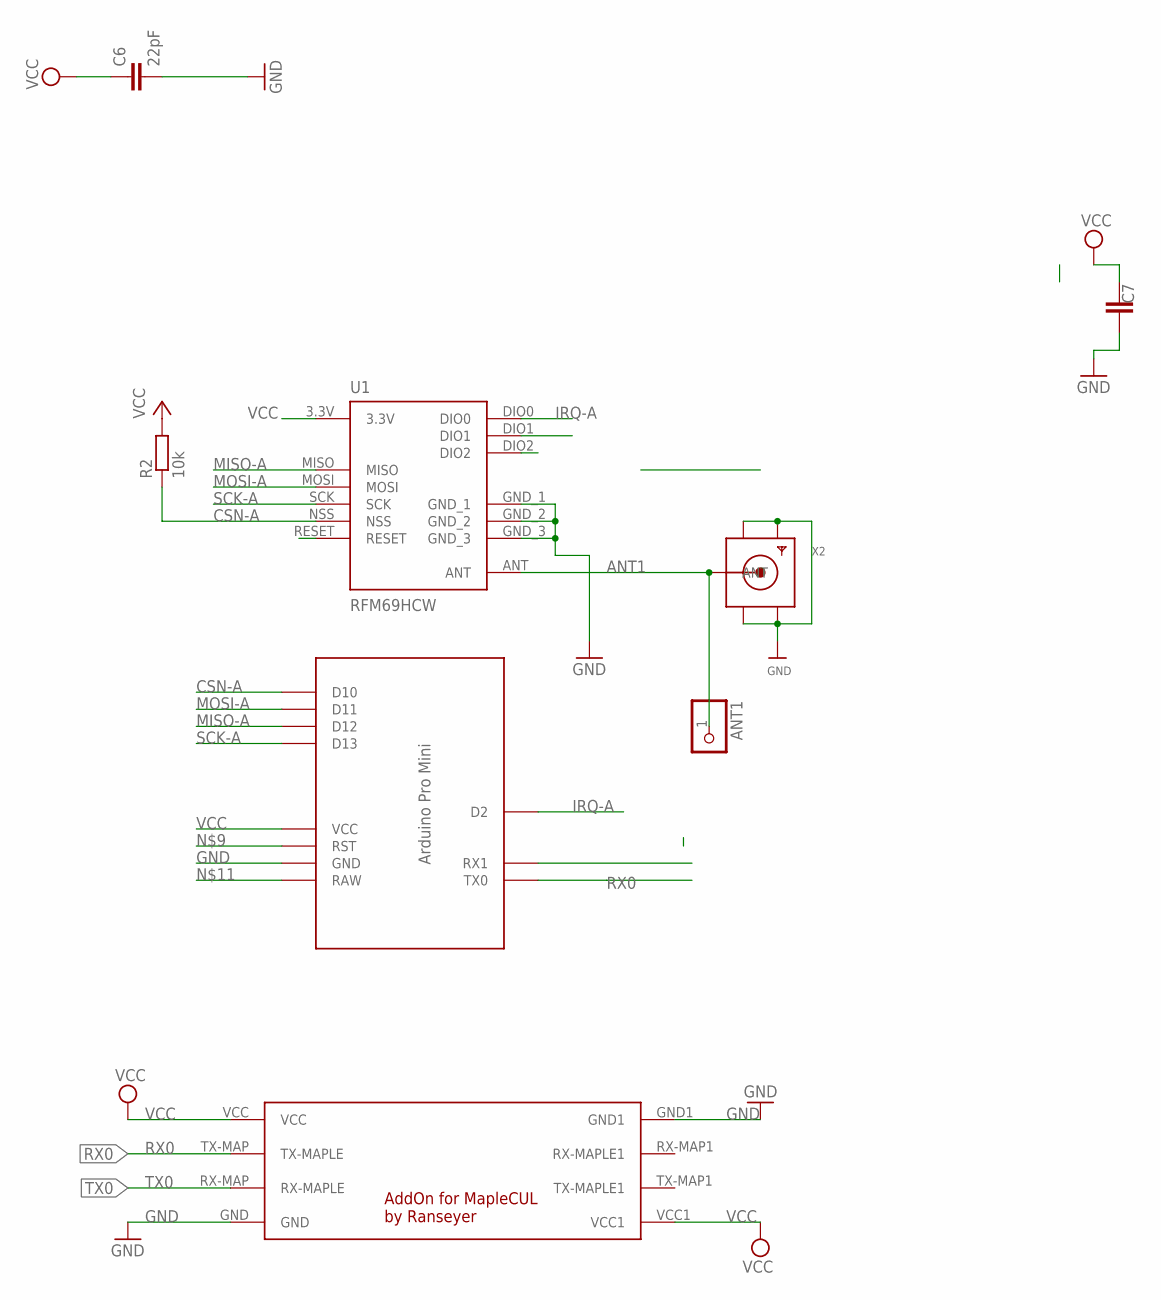
[picture p122: schematic V4-MySensors-LoRa-V006.sch]

Parts:
ANT1: PINHD-1X1; 1X01
C6: 22pF; C0805
C7: C-EUC1812; C1812
R2: 10k; M0805
U1: RFM69HCW; RFM69HCW-XXXS2
U$1: MARTIN-PROMINI-SPI; MARTIN-PRO-SPI
U$2: MAPLE-CUL-ADDON-V01; MAPLE-CUL-V01
X2: SMACONNECTOR_EDGE; SMA_EDGELAUNCH

Connections:
ANT1: ANT1.1, U1.ANT, X2.P (ANT)
CSN-A: R2.1, U1.NSS, U$1.D10
GND: C6.2, C7.1, U1.GND_1, U1.GND_2, U1.GND_3, U$1.GND, U$2.GND, U$2.GND1, X2.GND@1 (GND4), X2.GND@2 (GND3), X2.GND@3 (GND2), X2.GND@4 (GND1)
IRQ-A: U1.DIO0, U$1.D2
MISO-A: U1.MISO, U$1.D12
MOSI-A: U1.MOSI, U$1.D11
RX0: U$1.TX0, U$2.TX-MAP (TX-MAPLE)
SCK-A: U1.SCK, U$1.D13
TX0: U$1.RX1, U$2.RX-MAP (RX-MAPLE)
VCC: C6.1, C7.2, R2.2, U1.3.3V, U$1.VCC, U$2.VCC, U$2.VCC1

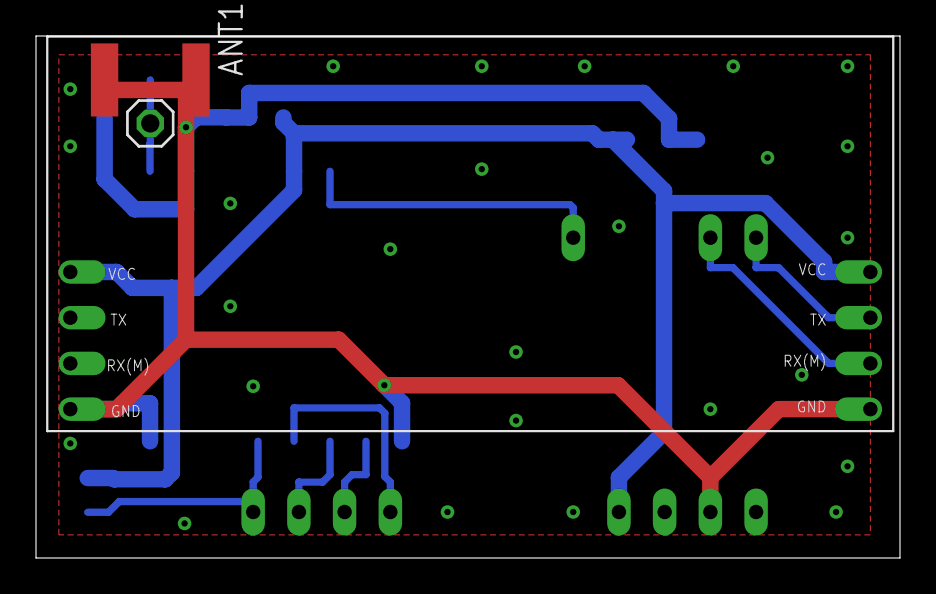
[picture p123: board V4-MySensors-LoRa-V006.brd from above]

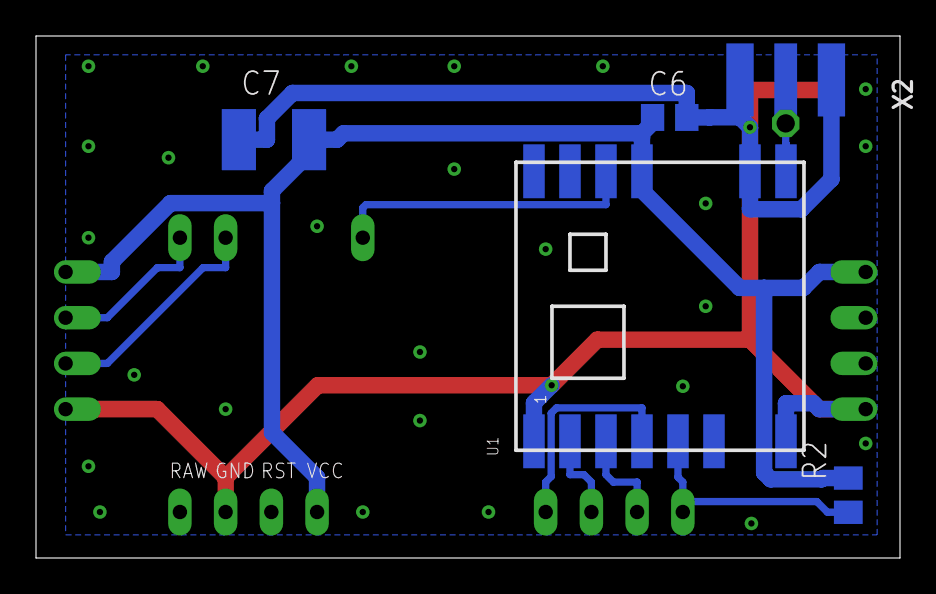
[picture p124: board V4-MySensors-LoRa-V006.brd from below]

Board: 2 copper layers, 48.0 x 29.0 mm, 8 parts (5 on the bottom side), 10 nets.
