ranseyer/CUN-STM32/HW-MAPLE-Large/V4.0/AddOnZigbeeSMD/V4-AddOnUigBeeSMD-V02-006.brd

## EAGLE design HW-MAPLE-Large/V4.0/AddOnZigbeeSMD/V4-AddOnUigBeeSMD-V02-006.brd (2019-07-03)

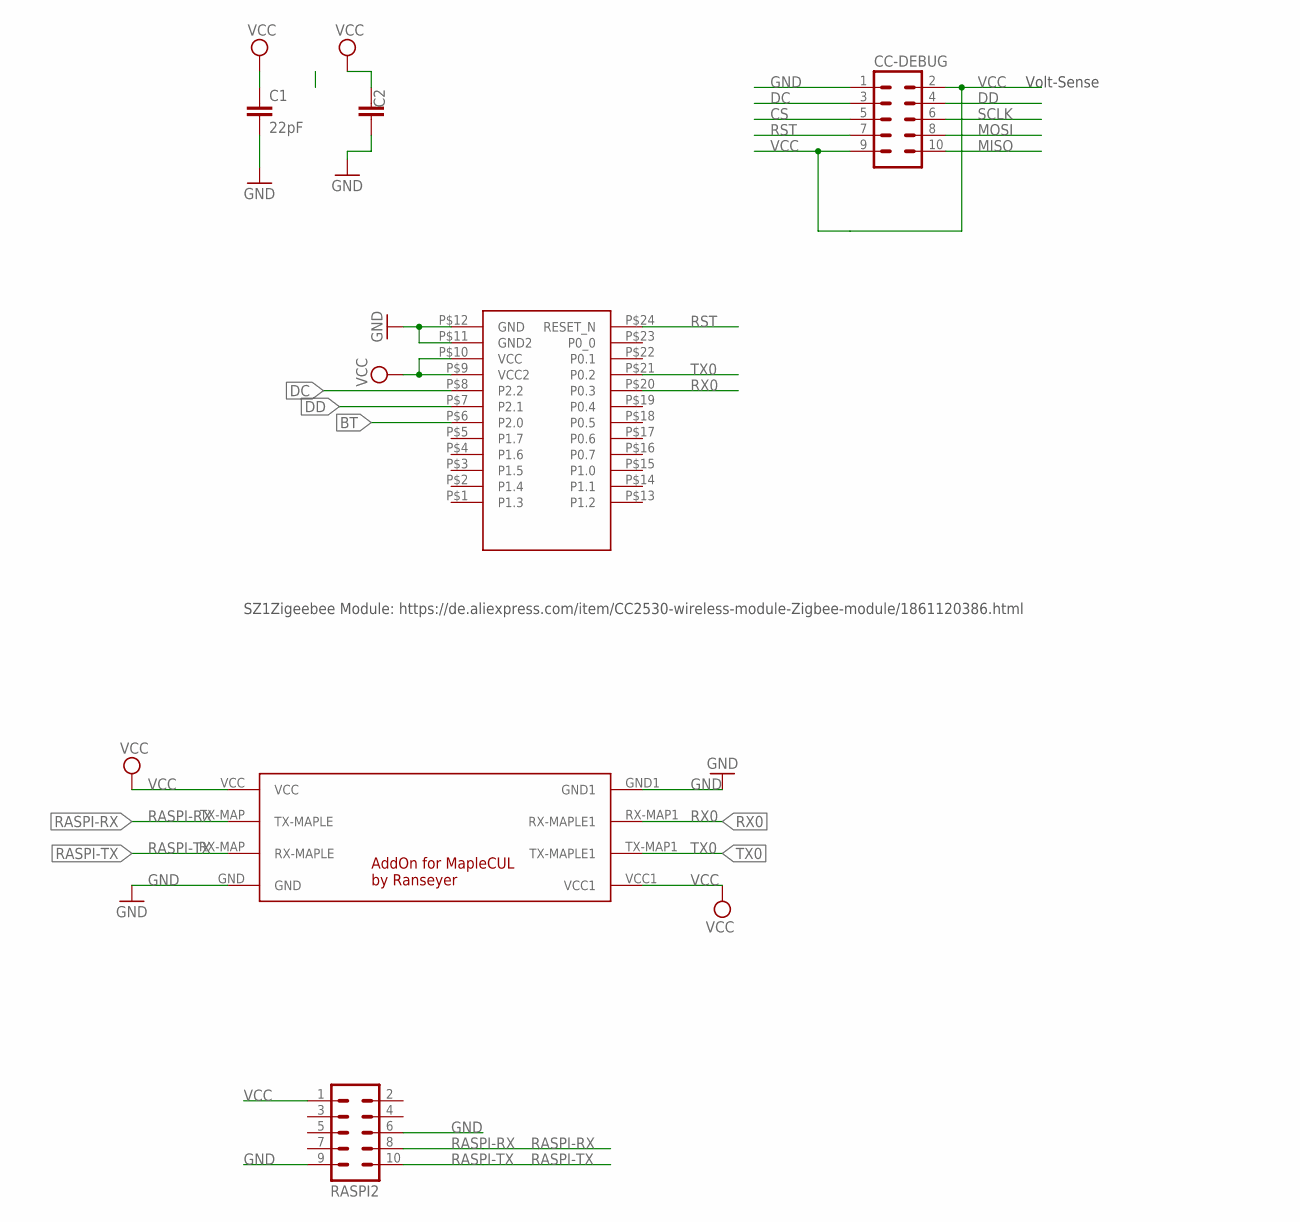
[picture p125: schematic V4-AddOnUigBeeSMD-V02-006.sch]

Parts:
C1: 22pF; C0805
C2: C-EUC1812; C1812
CC-DEBUG: CONN_05X2SHD_LOCK; 2X5-SHROUDED_LOCK
RASPI2: MA05-2
U$1: MAPLE-CUL-ADDON-V01; MAPLE-CUL-V01
U$2: CC2530; SZ1ZIGBEE-SMD

Connections:
BT: U$2.P$6 (P2.0)
CS: CC-DEBUG.5
DC: CC-DEBUG.3, U$2.P$8 (P2.2)
DD: CC-DEBUG.4, U$2.P$7 (P2.1)
GND: C1.2, C2.1, CC-DEBUG.1, RASPI2.6, RASPI2.9, U$1.GND, U$1.GND1, U$2.P$11 (GND2), U$2.P$12 (GND)
MISO: CC-DEBUG.10
MOSI: CC-DEBUG.8
RASPI-RX: RASPI2.8, U$1.TX-MAP (TX-MAPLE)
RASPI-TX: RASPI2.10, U$1.RX-MAP (RX-MAPLE)
RST: CC-DEBUG.7, U$2.P$24 (RESET_N)
RX0: U$1.RX-MAP1 (RX-MAPLE1), U$2.P$20 (P0.3)
SCLK: CC-DEBUG.6
TX0: U$1.TX-MAP1 (TX-MAPLE1), U$2.P$21 (P0.2)
VCC: C1.1, C2.2, CC-DEBUG.2, CC-DEBUG.9, RASPI2.1, U$1.VCC, U$1.VCC1, U$2.P$9 (VCC2), U$2.P$10 (VCC)

Notes on the sheet:
Volt-Sense
SZ1Zigeebee Module: https://de.aliexpress.com/item/CC2530-wireless-module-Zigbee-module/1861120386.html

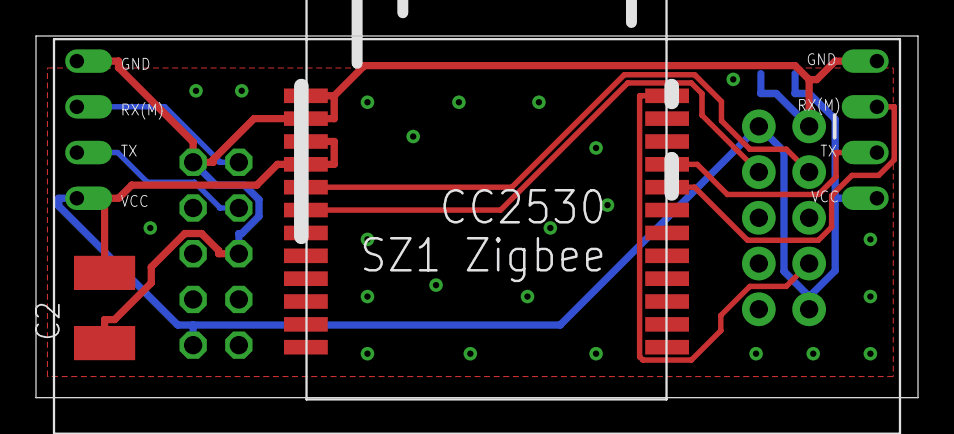
[picture p126: board V4-AddOnUigBeeSMD-V02-006.brd from above]

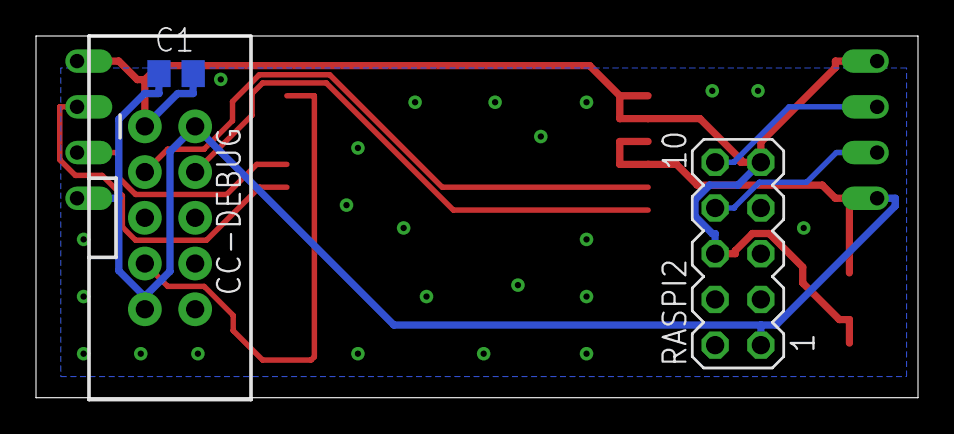
[picture p127: board V4-AddOnUigBeeSMD-V02-006.brd from below]

Board: 2 copper layers, 49.0 x 20.1 mm, 6 parts (3 on the bottom side), 9 nets.
