ranseyer/CUN-STM32/HW-MAPLE-Large/V4.0/AddOnTemplate/V4-AddOnLeer-V002.brd

## EAGLE design HW-MAPLE-Large/V4.0/AddOnTemplate/V4-AddOnLeer-V002.brd (2019-06-23)

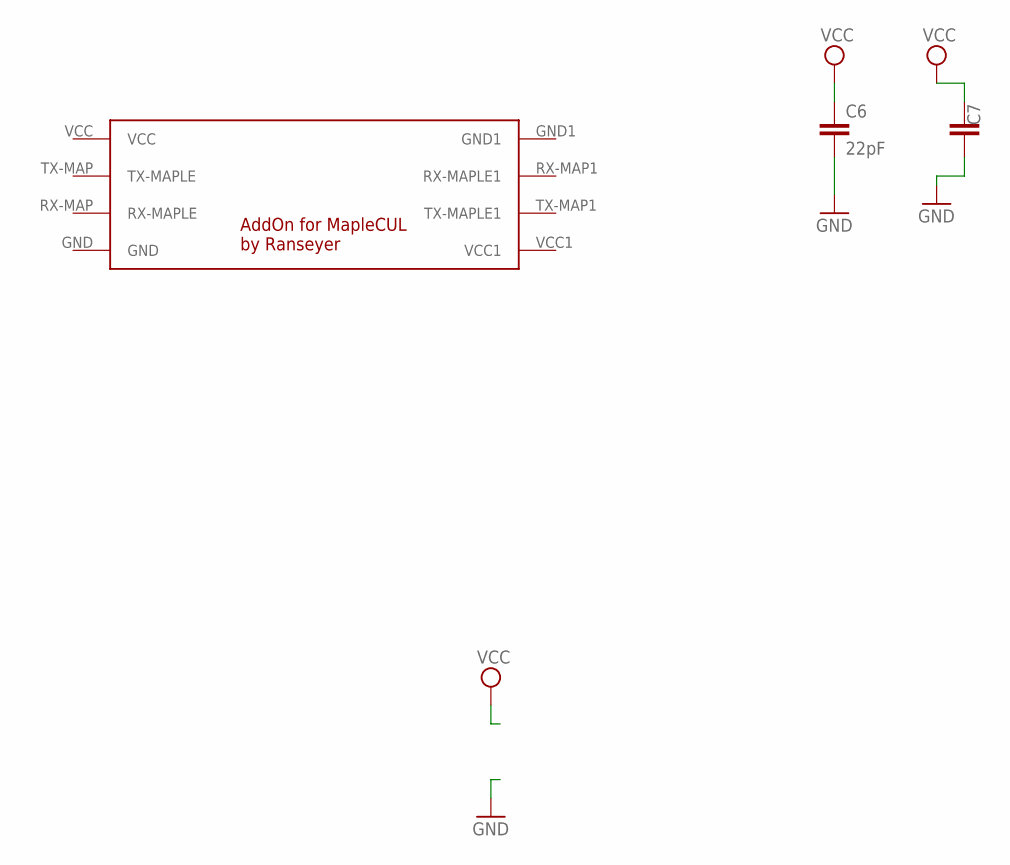
[picture p128: schematic V4-AddOnLeer-V002.sch]

Parts:
C6: 22pF; C0805
C7: C-EUC1812; C1812
U$1: MAPLE-CUL-ADDON-V01; MAPLE-CUL-V01

Connections:
GND: C6.2, C7.1
VCC: C6.1, C7.2

Board: 2 copper layers, 3 parts (1 on the bottom side), 2 nets, no tracks yet.
