ranseyer/CUN-STM32/HW-MAPLE-Large/V4.0/AddOnCC1101/V4-AddOnSduino-V003.brd

## EAGLE design HW-MAPLE-Large/V4.0/AddOnCC1101/V4-AddOnSduino-V003.brd (2019-04-22)

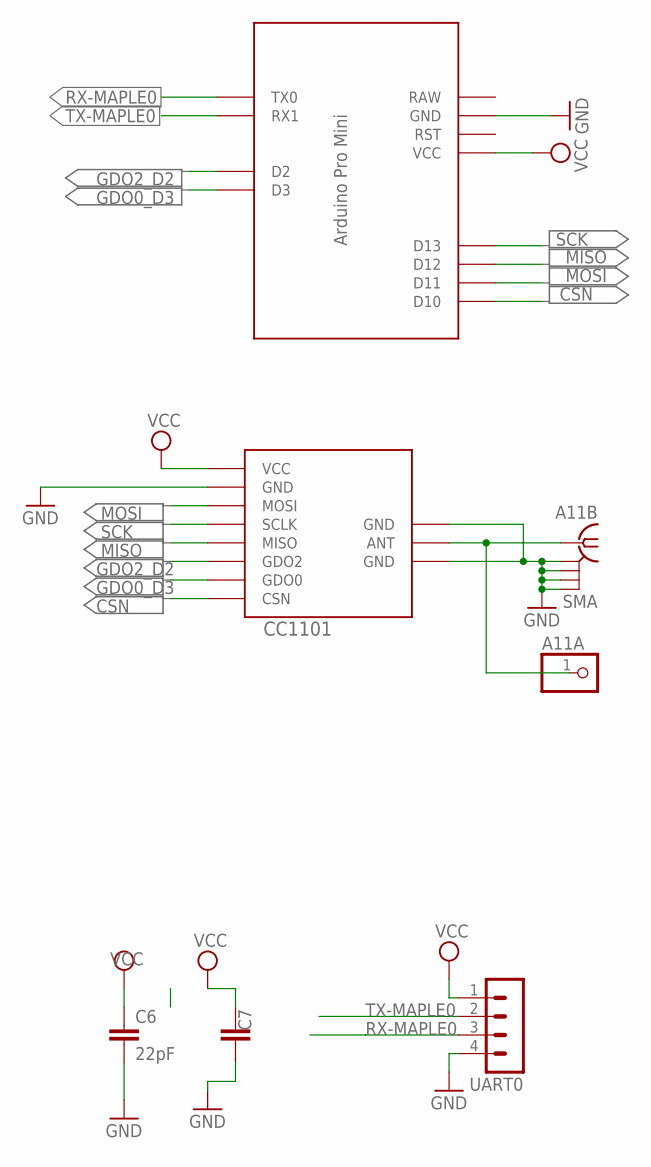
[picture p129: schematic V4-AddOnSduino-V003.sch]

Parts:
A11A: PINHD-1X1; 1X01
A11B: SMA
C6: 22pF; C0805
C7: C-EUC1812; C1812
CC1101: CC1101_MODULE1SMD; CC1101_MODULE1_SMD
U$2: MARTIN-PROMINI-CC1101; MARTIN-PRO-CC1101
UART0: MA04-1

Connections:
ANT1: A11A.1, A11B.1, CC1101.ANT
CSN: CC1101.CSN, U$2.D10
GDO0_D3: CC1101.GDO0, U$2.D3
GDO2_D2: CC1101.GDO2, U$2.D2
GND: A11B.GND@1 (2), A11B.GND@2 (3), A11B.GND@3 (4), A11B.GND@4 (5), C6.2, C7.1, CC1101.GND@0 (GND), CC1101.GND@1 (GND), CC1101.GND@2 (GND), U$2.GND, UART0.4
MISO: CC1101.MISO, U$2.D12
MOSI: CC1101.MOSI, U$2.D11
RX-MAPLE0: U$2.TX0, UART0.3
SCK: CC1101.SCLK, U$2.D13
TX-MAPLE0: U$2.RX1, UART0.2
VCC: C6.1, C7.2, CC1101.VCC, U$2.VCC, UART0.1

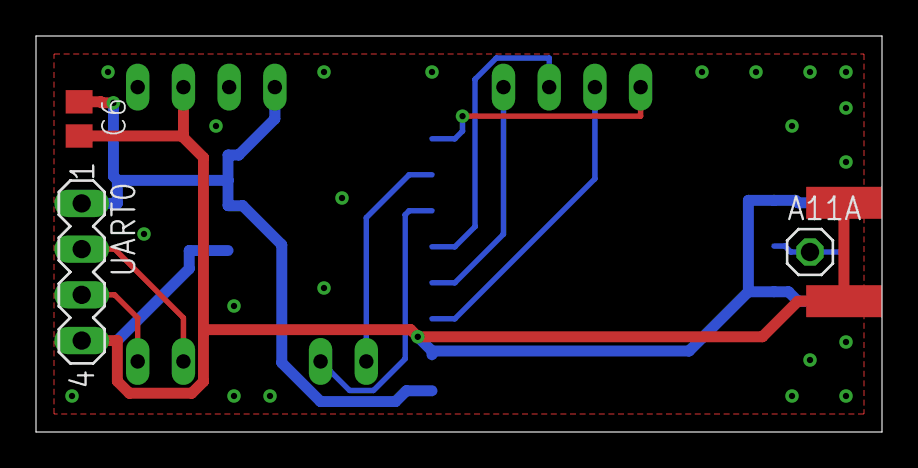
[picture p130: board V4-AddOnSduino-V003.brd from above]

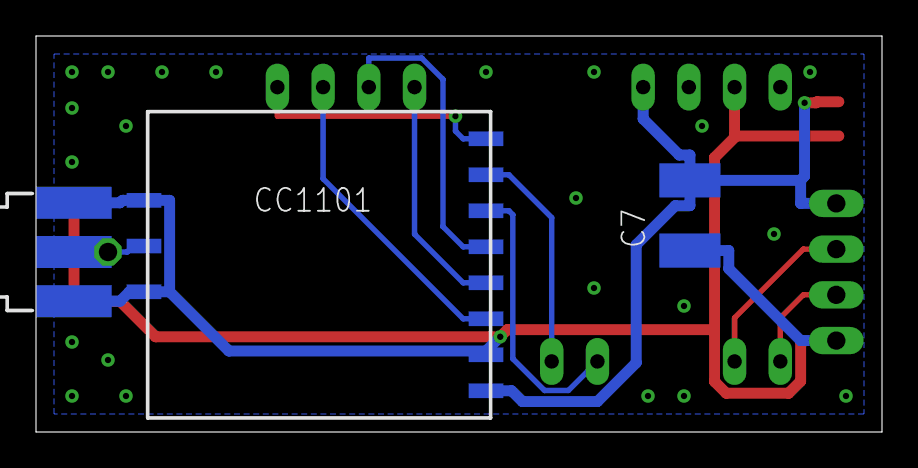
[picture p131: board V4-AddOnSduino-V003.brd from below]

Board: 2 copper layers, 47.0 x 22.0 mm, 7 parts (3 on the bottom side), 11 nets.
