ranseyer/CUN-STM32/HW-MAPLE-Large/Stamps/1Wire-Stamp/1WireStamp-V01-006.brd

## EAGLE design HW-MAPLE-Large/Stamps/1Wire-Stamp/1WireStamp-V01-006.brd (2019-02-22)

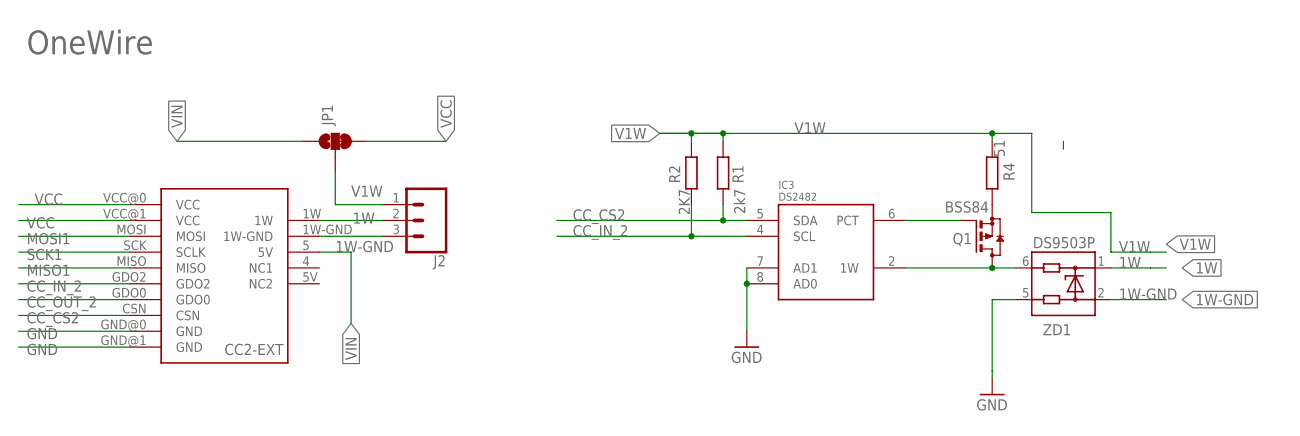
[picture p135: schematic 1WireStamp-V01-006.sch]

Parts:
CC2-EXT: ONEWIRE-MODULEONEWIRE_CC1101_WO-SILK; ONEWIRE_CC1101_MOD_WO_SILK
IC3: DS2482; SO08
J2: CONN_03LONGPADS; 1X03_LONGPADS
JP1: JUMPER-SMT_3_1-NC_TRACE_SILK; SMT-JUMPER_3_1-NC_TRACE_SILK
Q1: BSS84; SOT23
R1: 2k7; R0805
R2: 2K7; R0805
R4: 51; R0805
ZD1: DS9503P; TSOC6

Connections:
1W: CC2-EXT.1W, J2.2, ZD1.1
1W-GND: CC2-EXT.1W-GND, J2.3, ZD1.2
CC_CS2: CC2-EXT.CSN, IC3.5 (SDA), R1.2
CC_IN_2: CC2-EXT.GDO2, IC3.4 (SCL), R2.2
CC_OUT_2: CC2-EXT.GDO0
GND: CC2-EXT.GND@0 (GND), CC2-EXT.GND@1 (GND), IC3.3 (GND), IC3.7 (AD1), IC3.8 (AD0), ZD1.5
MISO1: CC2-EXT.MISO
MOSI1: CC2-EXT.MOSI
unnamed: IC3.6 (PCT), Q1.1 (G)
unnamed: IC3.2 (1W), Q1.3 (D), ZD1.6
unnamed: Q1.2 (S), R4.1
SCK1: CC2-EXT.SCK (SCLK)
V1W: IC3.1 (VDD), J2.1, JP1.2, R1.1, R2.1, R4.2
VCC: CC2-EXT.VCC@0 (VCC), CC2-EXT.VCC@1 (VCC), JP1.3
VIN: CC2-EXT.5 (5V), JP1.1

Notes on the sheet:
OneWire

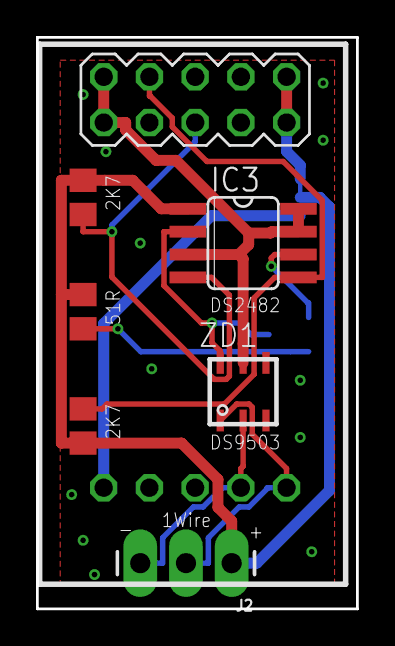
[picture p136: board 1WireStamp-V01-006.brd from above]

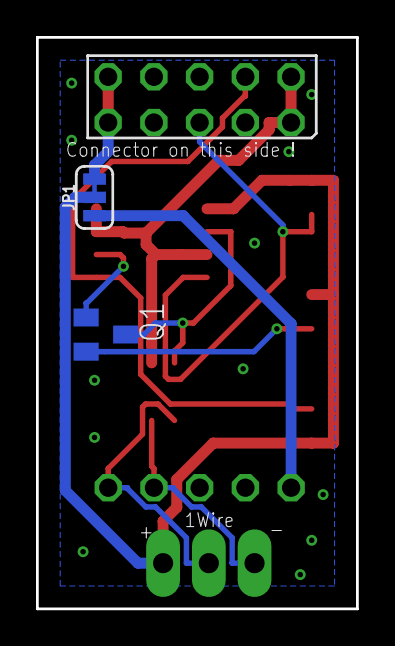
[picture p137: board 1WireStamp-V01-006.brd from below]

Board: 2 copper layers, 17.8 x 31.8 mm, 9 parts (2 on the bottom side), 11 nets.
