ranseyer/CUN-STM32/HW-MAPLE-Large/Stamps/Adapter-for-Stamps/Adapter-Stamps-005.brd

## EAGLE design HW-MAPLE-Large/Stamps/Adapter-for-Stamps/Adapter-Stamps-005.brd (2017-05-12)

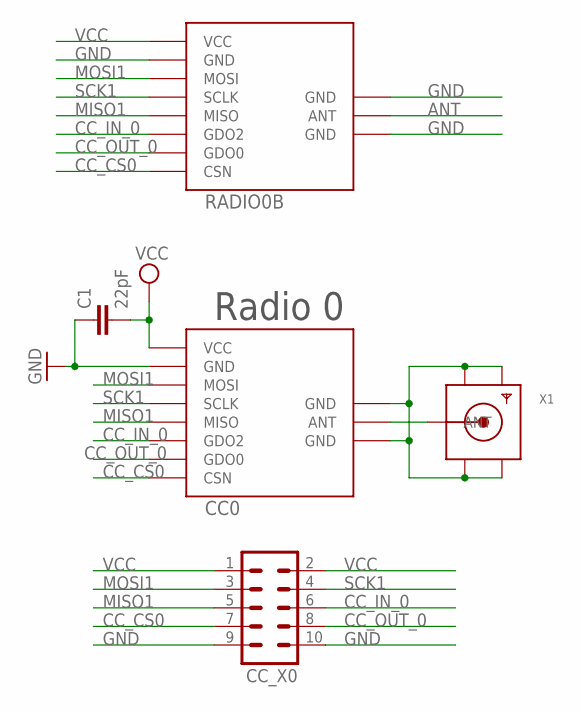
[picture p138: schematic Adapter-Stamps-005.sch]

Parts:
C1: 22pF; C0805
CC0: CC1101_MODULE1SMD; CC1101_MODULE1_SMD
CC_X0: MA05-2
RADIO0B: CC1101_MODULE1SMALL; CC1101_MODULE1_SMD
X1: SMACONNECTOR_EDGE_UFL; SMA_EDGELAUNCH_UFL

Connections:
ANT: RADIO0B.ANT
CC_CS0: CC0.CSN, CC_X0.7, RADIO0B.CSN
CC_IN_0: CC0.GDO2, CC_X0.6, RADIO0B.GDO2
CC_OUT_0: CC0.GDO0, CC_X0.8, RADIO0B.GDO0
GND: C1.1, CC0.GND@0 (GND), CC_X0.9, CC_X0.10, RADIO0B.GND@0 (GND), RADIO0B.GND@1 (GND), RADIO0B.GND@2 (GND)
MISO1: CC0.MISO, CC_X0.5, RADIO0B.MISO
MOSI1: CC0.MOSI, CC_X0.3, RADIO0B.MOSI
unnamed: CC0.ANT, X1.P (ANT)
unnamed: CC0.GND@1 (GND), CC0.GND@2 (GND), X1.GND@1 (GND1), X1.GND@2 (GND2), X1.GND@3 (GND3), X1.GND@4 (GND4)
SCK1: CC0.SCLK, CC_X0.4, RADIO0B.SCLK
VCC: C1.2, CC0.VCC, CC_X0.1, CC_X0.2, RADIO0B.VCC

Notes on the sheet:
Radio 0

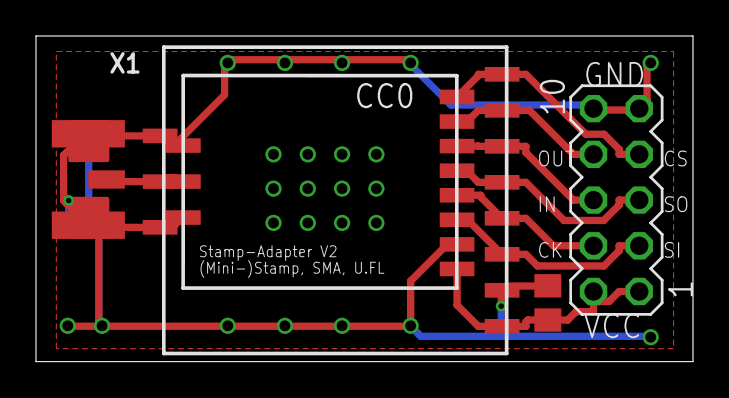
[picture p139: board Adapter-Stamps-005.brd from above]

Board: 2 copper layers, 36.5 x 18.1 mm, 5 parts (0 on the bottom side), 10 nets.
