ranseyer/CUN-STM32/HW-MAPLE-Large/Stamps/Adapter-for-Stamps/Archiv/Adapter-Stamps-001.brd

## EAGLE design HW-MAPLE-Large/Stamps/Adapter-for-Stamps/Archiv/Adapter-Stamps-001.brd (2017-02-02, an earlier design)

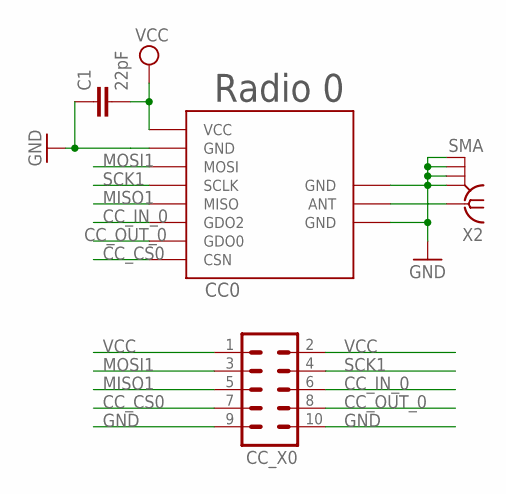
[picture p140: schematic Adapter-Stamps-001.sch]

Parts:
C1: 22pF; C0805
CC0: CC1101_MODULE1SMD; CC1101_MODULE1_SMD
CC_X0: MA05-2
X2: SMA

Connections:
CC_CS0: CC0.CSN, CC_X0.7
CC_IN_0: CC0.GDO2, CC_X0.6
CC_OUT_0: CC0.GDO0, CC_X0.8
GND: C1.1, CC0.GND@0 (GND), CC0.GND@1 (GND), CC0.GND@2 (GND), CC_X0.9, CC_X0.10, X2.GND@1 (2), X2.GND@2 (3), X2.GND@3 (4), X2.GND@4 (5)
MISO1: CC0.MISO, CC_X0.5
MOSI1: CC0.MOSI, CC_X0.3
unnamed: CC0.ANT, X2.1
SCK1: CC0.SCLK, CC_X0.4
VCC: C1.2, CC0.VCC, CC_X0.1, CC_X0.2

Notes on the sheet:
Radio 0

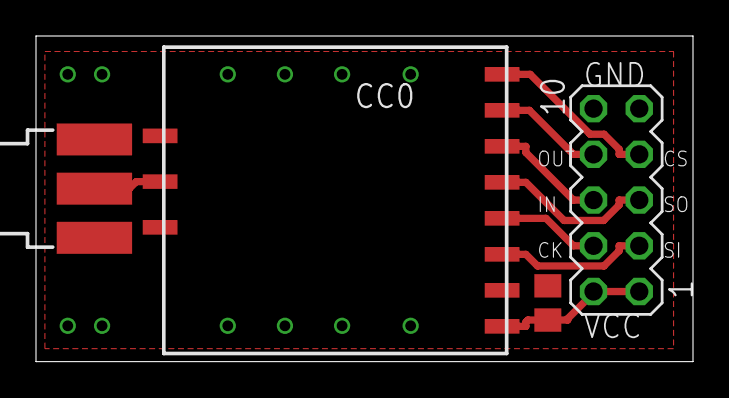
[picture p141: board Adapter-Stamps-001.brd from above]

Board: 2 copper layers, 36.5 x 18.1 mm, 4 parts (0 on the bottom side), 9 nets.
