ranseyer/CUN-STM32/HW-MAPLE-Large/V4.0/AddOnZigbeeSMD/V4-AddOnZigbee-SMD-V002.brd

## EAGLE design HW-MAPLE-Large/V4.0/AddOnZigbeeSMD/V4-AddOnZigbee-SMD-V002.brd (2019-04-13)

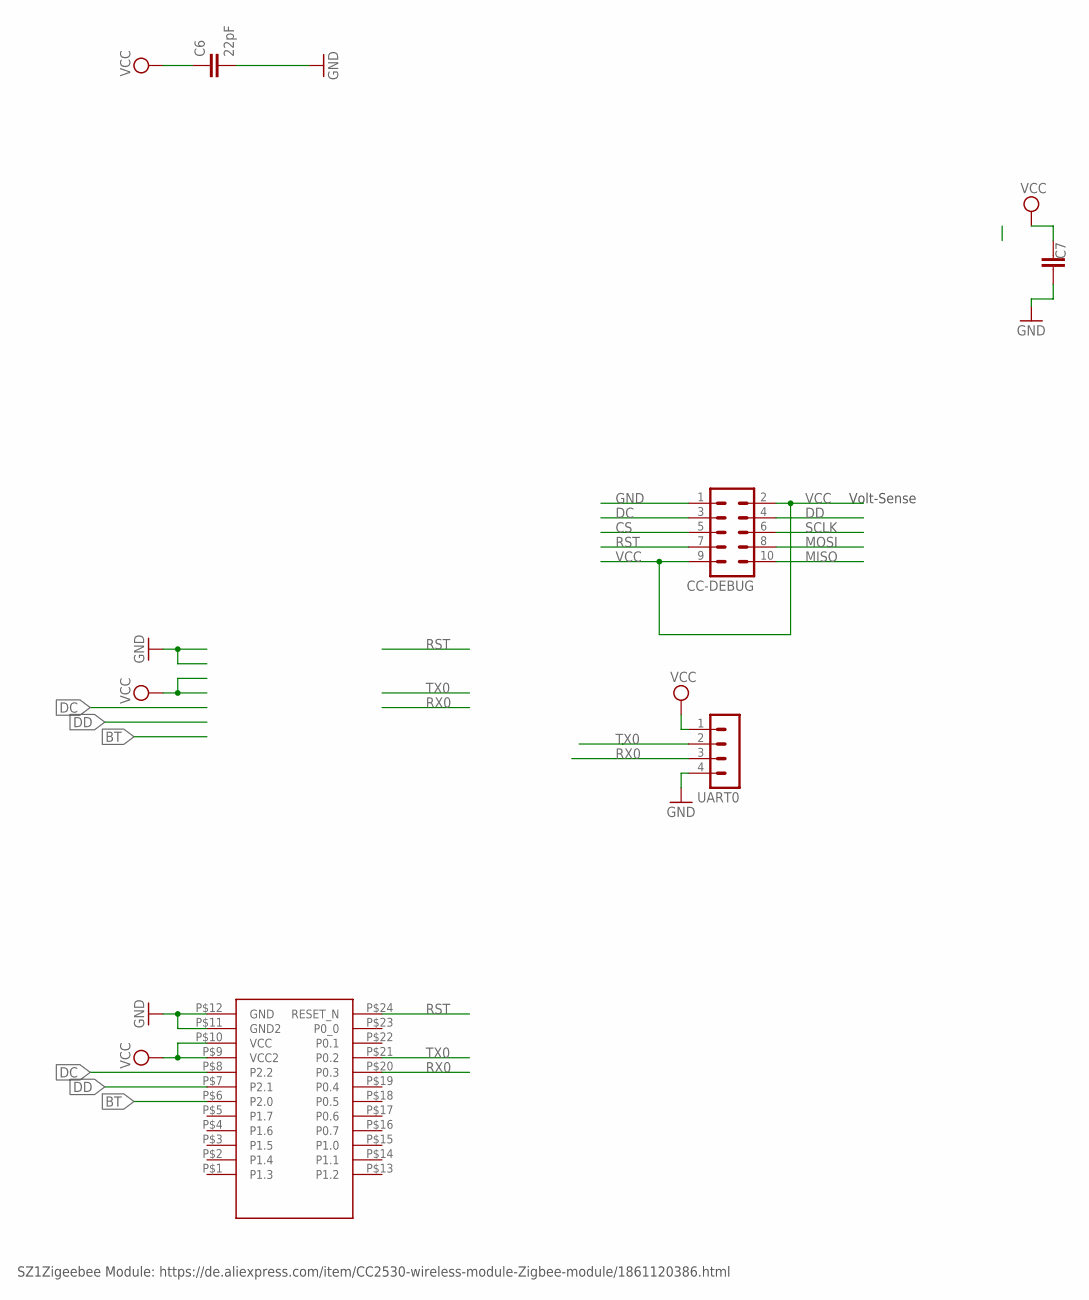
[picture p142: schematic V4-AddOnZigbee-SMD-V002.sch]

Parts:
C6: 22pF; C0805
C7: C-EUC1812; C1812
CC-DEBUG: MA05-2
U$1: CC2530; SZ1ZIGBEE-SMD
UART0: MA04-1

Connections:
BT: U$1.P$6 (P2.0)
CS: CC-DEBUG.5
DC: CC-DEBUG.3, U$1.P$8 (P2.2)
DD: CC-DEBUG.4, U$1.P$7 (P2.1)
GND: C6.2, C7.1, CC-DEBUG.1, U$1.P$11 (GND2), U$1.P$12 (GND), UART0.4
MISO: CC-DEBUG.10
MOSI: CC-DEBUG.8
RST: CC-DEBUG.7, U$1.P$24 (RESET_N)
RX0: U$1.P$20 (P0.3), UART0.3
SCLK: CC-DEBUG.6
TX0: U$1.P$21 (P0.2), UART0.2
VCC: C6.1, C7.2, CC-DEBUG.2, CC-DEBUG.9, U$1.P$9 (VCC2), U$1.P$10 (VCC), UART0.1

Notes on the sheet:
Volt-Sense
SZ1Zigeebee Module: https://de.aliexpress.com/item/CC2530-wireless-module-Zigbee-module/1861120386.html

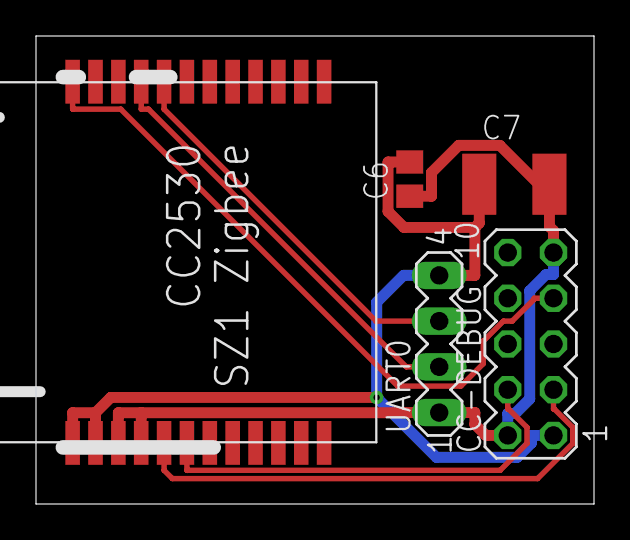
[picture p143: board V4-AddOnZigbee-SMD-V002.brd from above]

Board: 2 copper layers, 31.0 x 26.0 mm, 5 parts (0 on the bottom side), 7 nets.
