ranseyer/CUN-STM32/HW-MAPLE-Large/Archiv/AddOns/RasPi-UART__Zigbee-CC2530/Addon-mapleCUx_Raspi-3V3-UART-CC2530-V02-05.brd

## EAGLE design HW-MAPLE-Large/Archiv/AddOns/RasPi-UART__Zigbee-CC2530/Addon-mapleCUx_Raspi-3V3-UART-CC2530-V02-05.brd (2018-11-17, an earlier design)

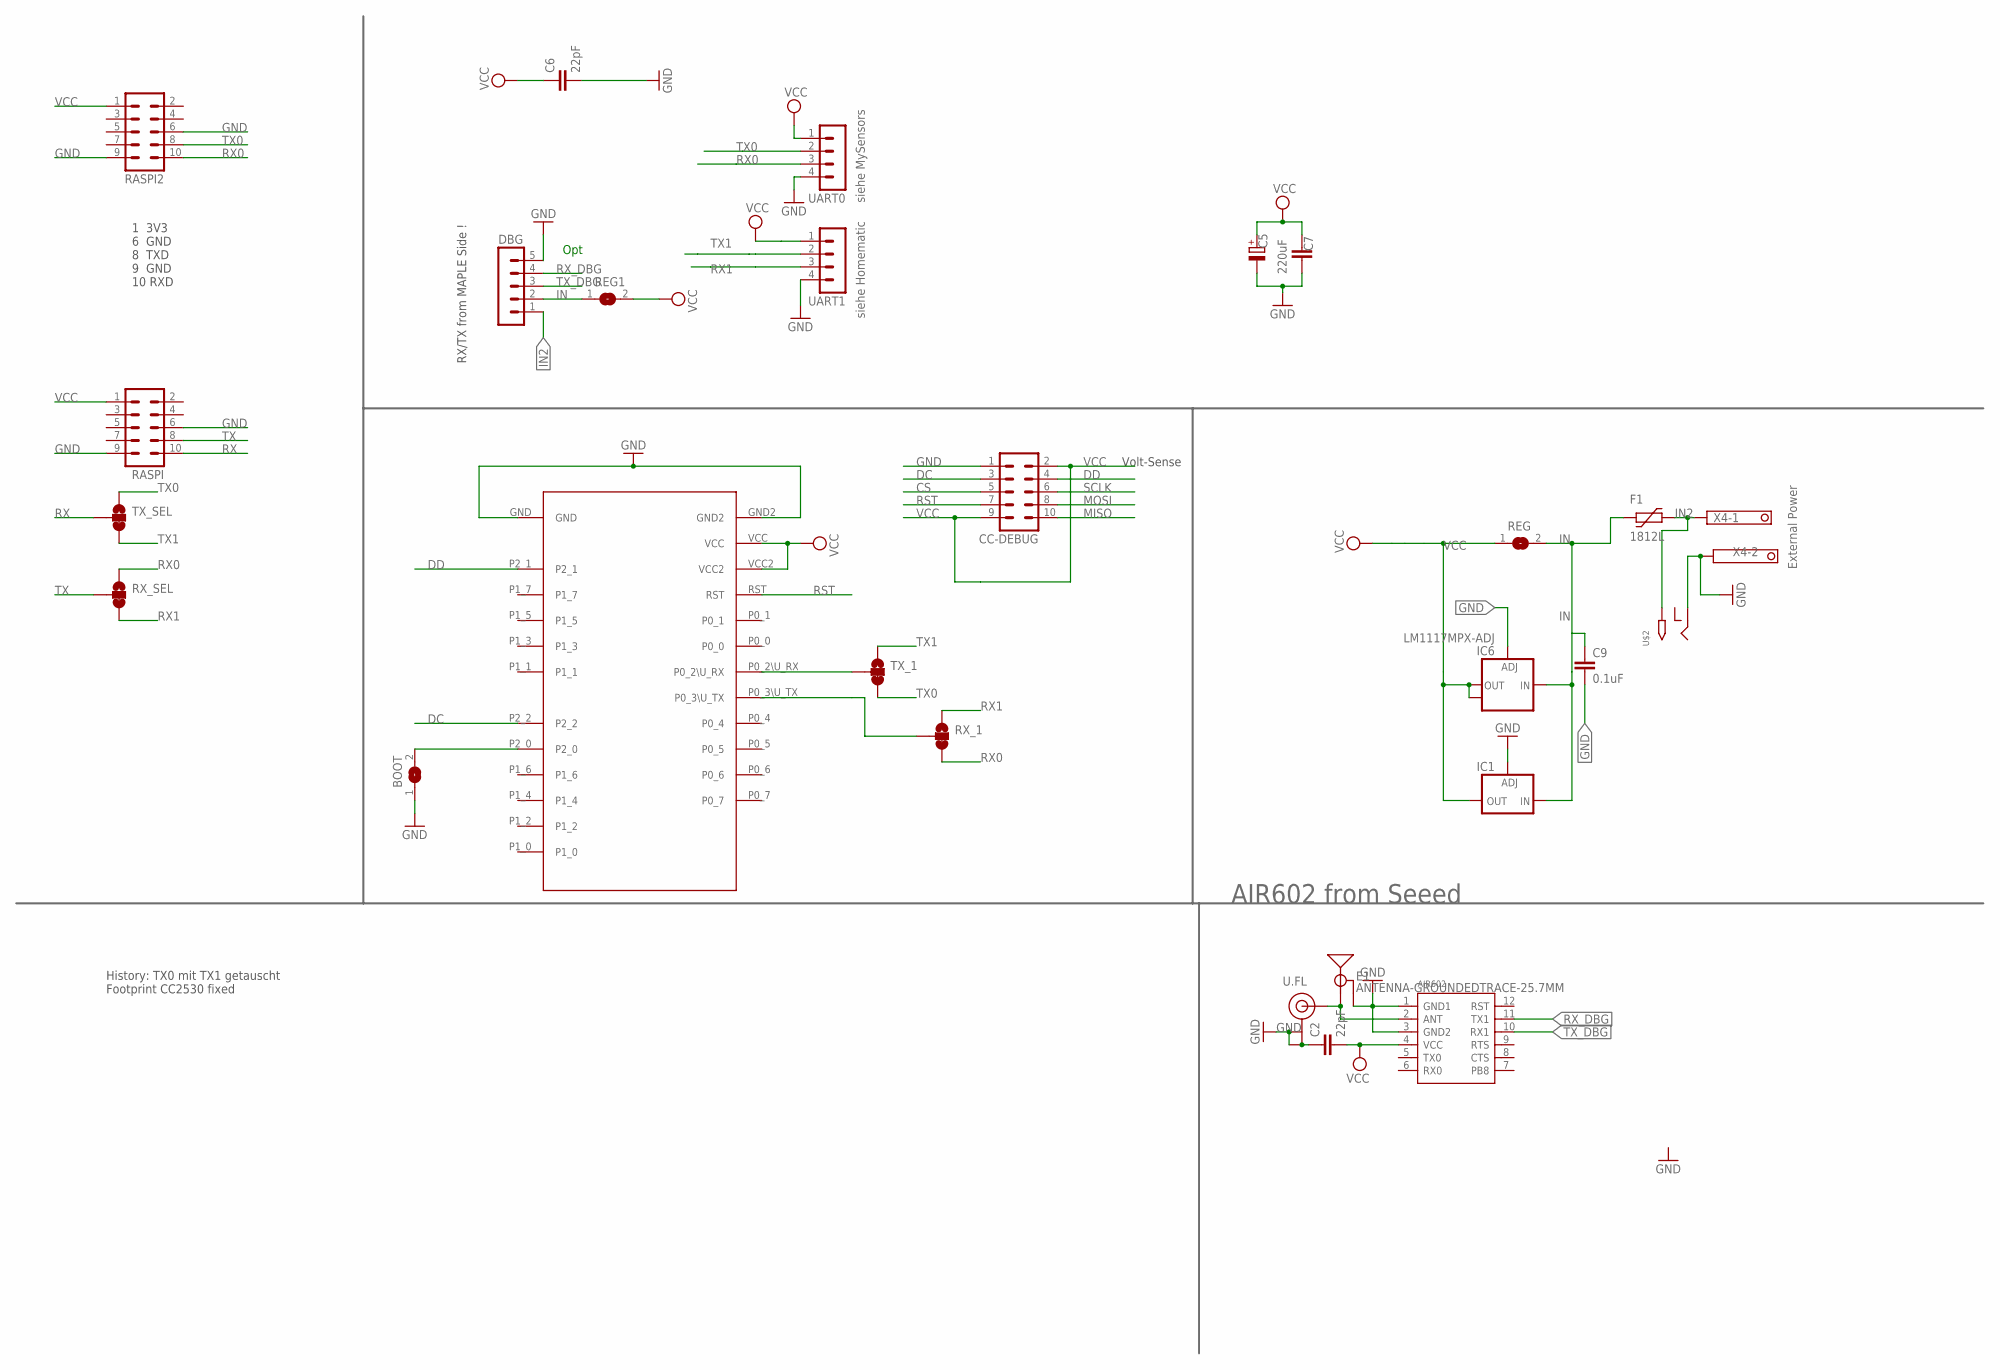
[picture p144: schematic Addon-mapleCUx_Raspi-3V3-UART-CC2530-V02-05.sch]

Parts:
AIR602: AIR602; MODULE12P-2.0-10X12MM
BOOT: SJ
C2, C6: 22pF; C0805
C5: 220uF; E5-8,5
C7: C-EUC1812; C1812
C9: 0.1uF; C1206
CC-DEBUG: MA05-2
DBG: MA05-1
E1: ANTENNA-GROUNDEDTRACE-25.7MM; TRACE_ANTENNA_2.4GHZ_25.7MM
F1: 1812L
IC1: LD117ADT50TR; DPACK
IC6: LM1117MPX-ADJ; SOT223
RASPI, RASPI2: MA05-2
REG, REG1: SJ
RX_1: JUMPER-SMT_3_1-NC_TRACE_SILK; SMT-JUMPER_3_1-NC_TRACE_SILK
RX_SEL: JUMPER-SMT_3_1-NC_TRACE_SILK; SMT-JUMPER_3_1-NC_TRACE_SILK
TX_1: JUMPER-SMT_3_1-NC_TRACE_SILK; SMT-JUMPER_3_1-NC_TRACE_SILK
TX_SEL: JUMPER-SMT_3_1-NC_TRACE_SILK; SMT-JUMPER_3_1-NC_TRACE_SILK
U$2: 2.1MMJACKTHM; PJ-102A
U$3: CC2530_MODULE; CC2530_DIL
U.FL: U.FL
UART0, UART1: MA04-1
X4: 1751248

Connections:
CS: CC-DEBUG.5
DC: CC-DEBUG.3, U$3.P2_2
DD: CC-DEBUG.4, U$3.P2_1
GND: AIR602.1 (GND1), AIR602.3 (GND2), BOOT.1, C2.1, C5.-, C6.2, C7.1, C9.2, CC-DEBUG.1, DBG.5, E1.GND, E1.GND2 (GND), IC1.1 (ADJ), IC6.1 (ADJ), RASPI.6, RASPI.9, RASPI2.6, RASPI2.9, U$2.RING, U$3.GND, U$3.GND2, U.FL.1 (GND), U.FL.2 (GND), UART0.4, UART1.4, X4.2
IN: C9.1, DBG.2, F1.P$1 (1), IC1.3 (IN), IC6.3 (IN), REG.2, REG1.1
IN2: DBG.1, F1.P$2 (2), U$2.TIP, X4.1
MISO: CC-DEBUG.10
MOSI: CC-DEBUG.8
unnamed: BOOT.2, U$3.P2_0
unnamed: TX_1.2, U$3.P0_2\U_RX
unnamed: RX_1.2, U$3.P0_3\U_TX
unnamed: AIR602.2 (ANT), E1.ANT (SIGNAL), U.FL.FEED (SIGNAL)
RST: CC-DEBUG.7, U$3.RST
RX: RASPI.10, TX_SEL.2
RX0: RASPI2.10, RX_1.3, RX_SEL.1, UART0.3
RX1: RX_1.1, RX_SEL.3, UART1.3
RX_DBG: AIR602.11 (TX1), DBG.4
SCLK: CC-DEBUG.6
TX: RASPI.8, RX_SEL.2
TX0: RASPI2.8, TX_1.3, TX_SEL.1, UART0.2
TX1: TX_1.1, TX_SEL.3, UART1.2
TX_DBG: AIR602.10 (RX1), DBG.3
VCC: AIR602.4 (VCC), C2.2, C5.+, C6.1, C7.2, CC-DEBUG.2, CC-DEBUG.9, IC1.4 (OUT), IC6.2 (OUT), IC6.TAB (OUT1), RASPI.1, RASPI2.1, REG.1, REG1.2, U$3.VCC, U$3.VCC2, UART0.1, UART1.1

Notes on the sheet:
Opt
siehe Homematic
siehe MySensors
1 3V3 6 GND 8 TXD 9 GND 10 RXD
RX/TX from MAPLE Side !
External Power
History: TX0 mit TX1 getauscht Footprint CC2530 fixed
Volt-Sense
AIR602 from Seeed

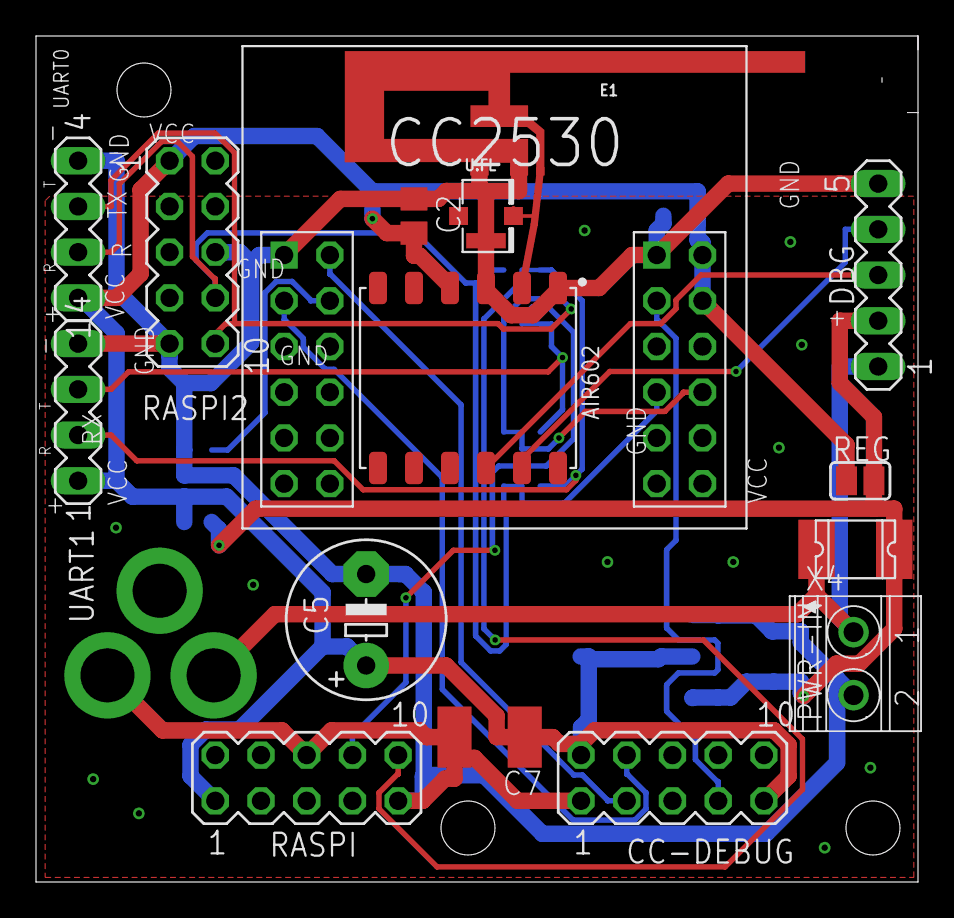
[picture p145: board Addon-mapleCUx_Raspi-3V3-UART-CC2530-V02-05.brd from above]

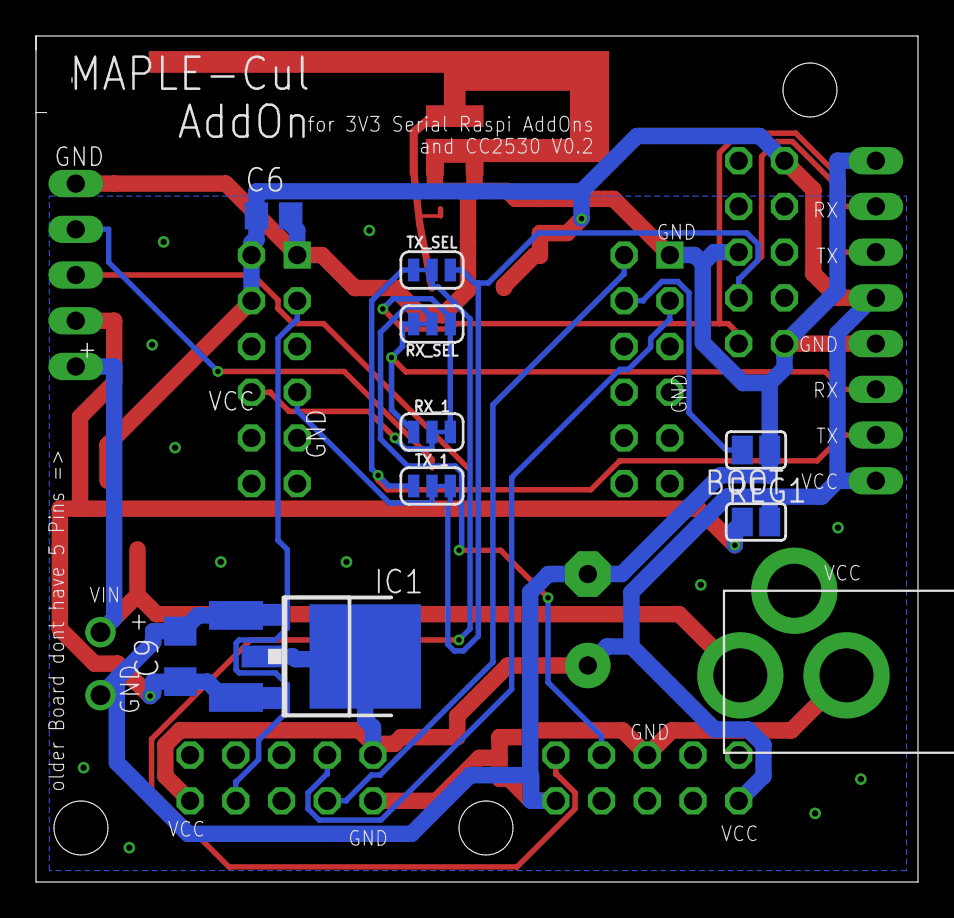
[picture p146: board Addon-mapleCUx_Raspi-3V3-UART-CC2530-V02-05.brd from below]

Board: 2 copper layers, 49.0 x 47.0 mm, 27 parts (11 on the bottom side), 19 nets.
