ranseyer/CUN-STM32/zz-Delete/HW-MAPLE-Med/mapleCUx_med_024.sch

## EAGLE design zz-Delete/HW-MAPLE-Med/mapleCUx_med_024.sch (2017-04-22)

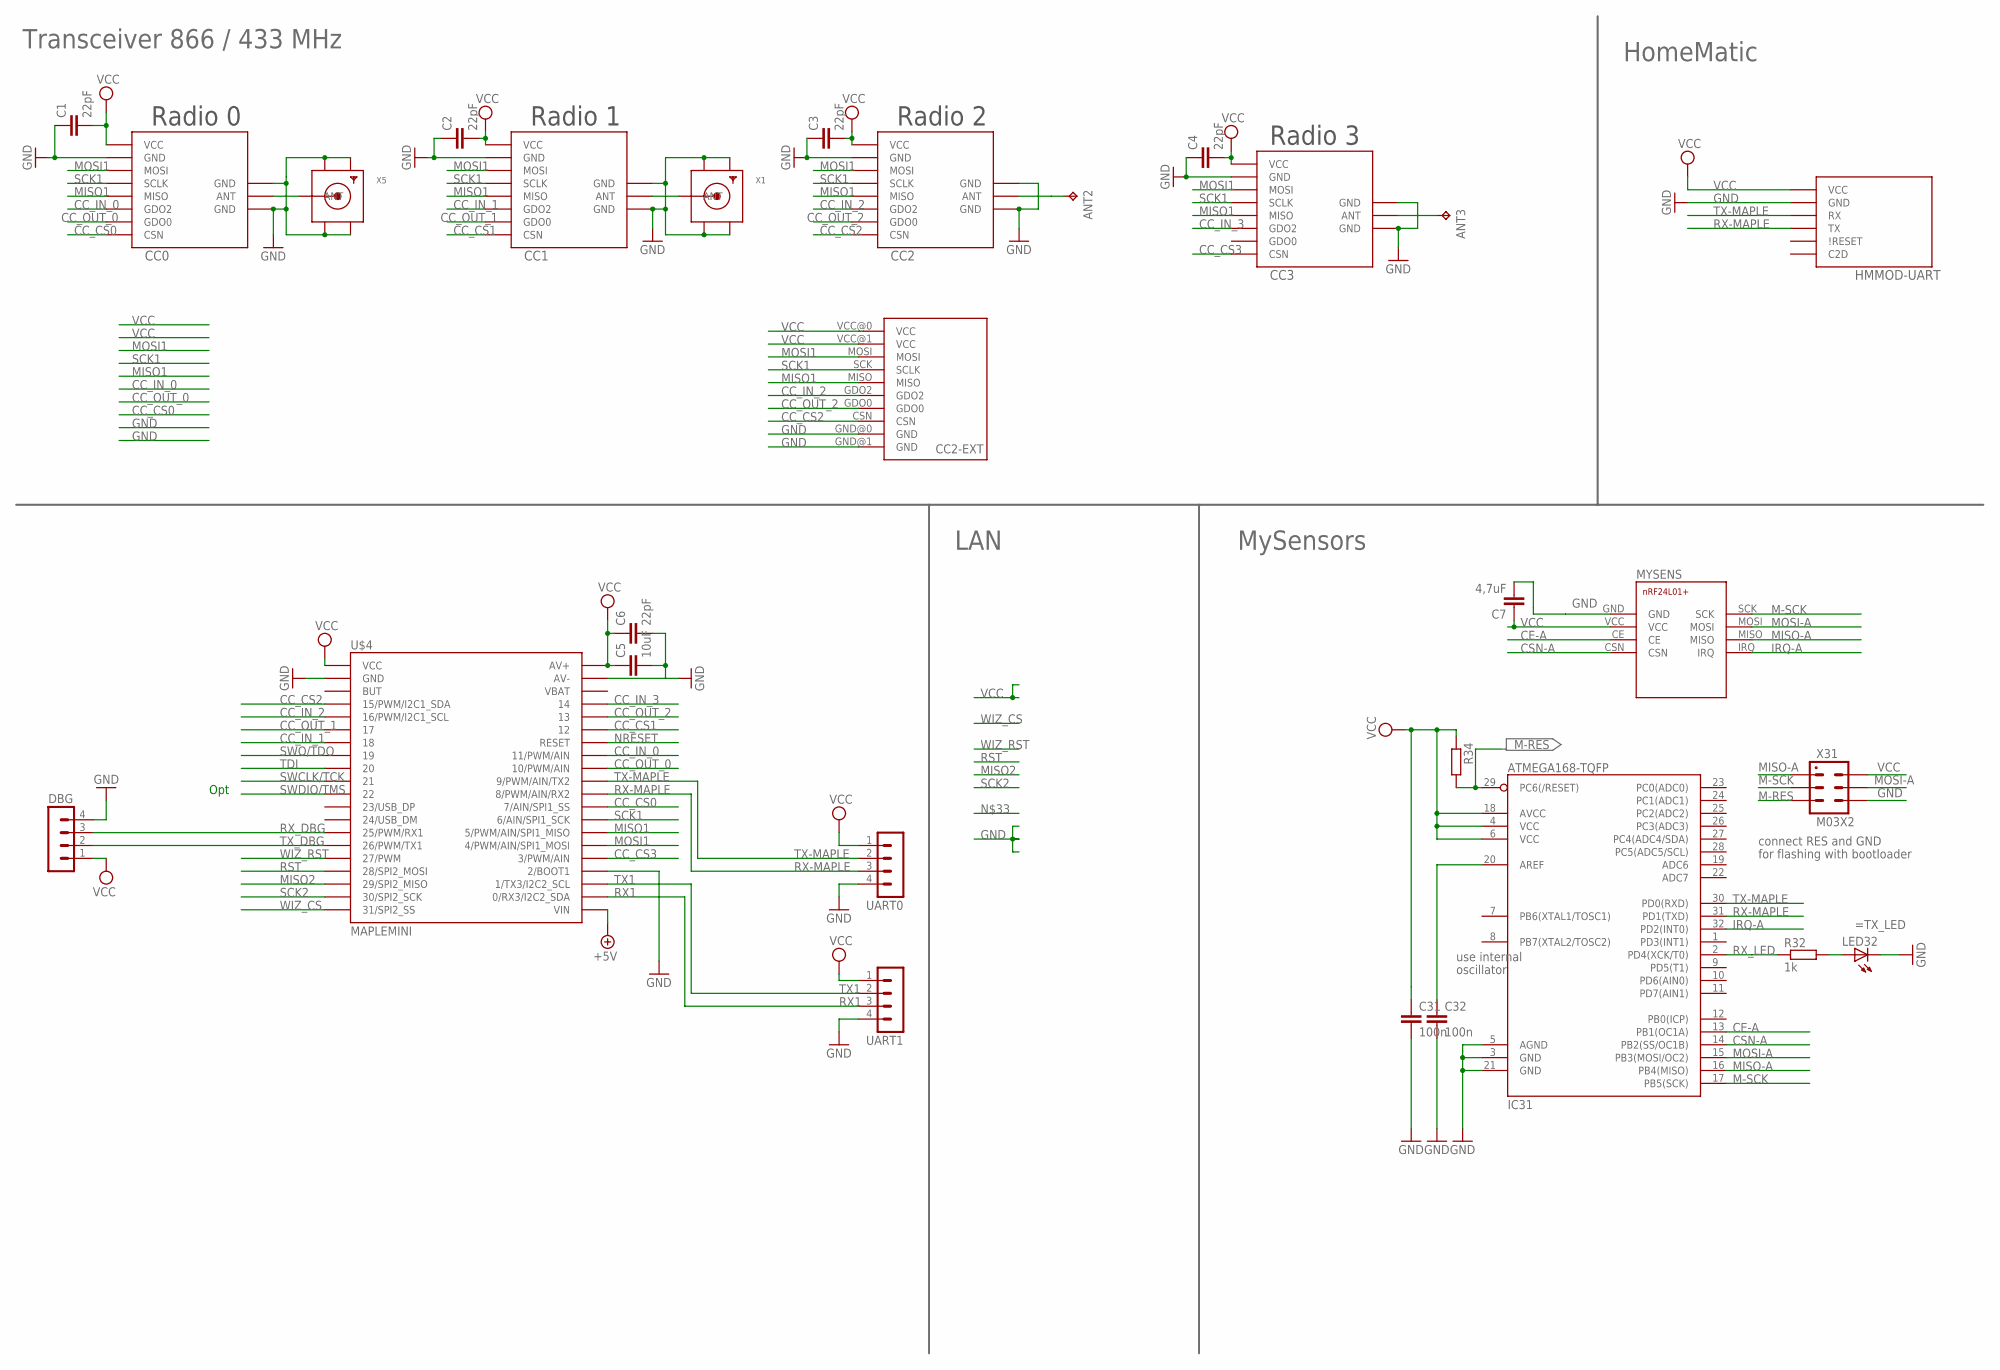
[picture p147: schematic mapleCUx_med_024.sch]

Parts:
ANT2, ANT3: TPPAD1-13; P1-13
C1, C2, C3, C4, C6: 22pF; C0805
C5: 10uF; C1210
C7: 4,7uF; C1210
C31, C32: 100n; C0805
CC0: CC1101; CC1101_MODULE1_SMD
CC1, CC2, CC3: CC1101_MODULE1SMD; CC1101_MODULE1_SMD
CC2-EXT: CC1101_MODULE3_DIL
DBG: MA04-1
HMMOD-UART: HM-MOD-UARTDIL; HM-MOD-UART-DIL
IC31: ATMEGA168-TQFP; TQFP32-08
LED32: LEDCHIPLED_0805; CHIPLED_0805
MYSENS: NRF24L01+SMD
R32: 1k; R0805
R34: R-EU_R0805; R0805
U$4: MAPLEMINI; 20-DIP
UART0, UART1: MA04-1
X1, X5: SMACONNECTOR_EDGE_UFL; SMA_EDGELAUNCH_UFL
X31: M03X2; 2X03-1.27MM_SMD

Connections:
+5V: U$4.21 (VIN)
CC_CS0: CC0.CSN, U$4.29 (7/AIN/SPI1_SS)
CC_CS1: CC1.CSN, U$4.35 (12)
CC_CS2: CC2.CSN, CC2-EXT.CSN, U$4.4 (15/PWM/I2C1_SDA)
CC_CS3: CC3.CSN, U$4.25 (3/PWM/AIN)
CC_IN_0: CC0.GDO2, U$4.33 (11/PWM/AIN)
CC_IN_1: CC1.GDO2, U$4.7 (18)
CC_IN_2: CC2.GDO2, CC2-EXT.GDO2, U$4.5 (16/PWM/I2C1_SCL)
CC_IN_3: CC3.GDO2, U$4.37 (14)
CC_OUT_0: CC0.GDO0, U$4.32 (10/PWM/AIN)
CC_OUT_1: CC1.GDO0, U$4.6 (17)
CC_OUT_2: CC2.GDO0, CC2-EXT.GDO0, U$4.36 (13)
CE-A: IC31.13 (PB1(OC1A)), MYSENS.CE
CSN-A: IC31.14 (PB2(SS/OC1B)), MYSENS.CSN
GND: C1.1, C2.1, C3.1, C4.1, C5.2, C6.2, C7.2, C31.2, C32.2, CC0.GND@0 (GND), CC0.GND@1 (GND), CC0.GND@2 (GND), CC1.GND@0 (GND), CC1.GND@1 (GND), CC1.GND@2 (GND), CC2.GND@0 (GND), CC2.GND@1 (GND), CC2.GND@2 (GND), CC2-EXT.GND@0 (GND), CC2-EXT.GND@1 (GND), CC3.GND@0 (GND), CC3.GND@1 (GND), CC3.GND@2 (GND), DBG.4, HMMOD-UART.2 (GND), IC31.3 (GND), IC31.5 (AGND), IC31.21 (GND), LED32.C, MYSENS.GND, U$4.2 (GND), U$4.24 (2/BOOT1), U$4.39 (AV-), UART0.4, UART1.4, X1.GND@1 (GND1), X1.GND@2 (GND2), X1.GND@3 (GND3), X1.GND@4 (GND4), X5.GND@1 (GND1), X5.GND@2 (GND2), X5.GND@3 (GND3), X5.GND@4 (GND4), X31.P$6 (6)
IRQ-A: IC31.32 (PD2(INT0)), MYSENS.IRQ
M-RES: IC31.29 (PC6(/RESET)), R34.2, X31.P$5 (5)
M-SCK: IC31.17 (PB5(SCK)), MYSENS.SCK, X31.P$3 (3)
MISO1: CC0.MISO, CC1.MISO, CC2.MISO, CC2-EXT.MISO, CC3.MISO, U$4.27 (5/PWM/AIN/SPI1_MISO)
MISO2: U$4.18 (29/SPI2_MISO)
MISO-A: IC31.16 (PB4(MISO)), MYSENS.MISO, X31.P$1 (1)
MOSI1: CC0.MOSI, CC1.MOSI, CC2.MOSI, CC2-EXT.MOSI, CC3.MOSI, U$4.26 (4/PWM/AIN/SPI1_MOSI)
MOSI-A: IC31.15 (PB3(MOSI/OC2)), MYSENS.MOSI, X31.P$4 (4)
unnamed: CC1.ANT, X1.P (ANT)
unnamed: ANT3.TP, CC3.ANT
unnamed: ANT2.TP, CC2.ANT
unnamed: CC0.ANT, X5.P (ANT)
unnamed: LED32.A, R32.2
unnamed: C32.1, IC31.20 (AREF)
NRESET: U$4.34 (RESET)
RST: U$4.17 (28/SPI2_MOSI)
RX1: U$4.22 (0/RX3/I2C2_SDA), UART1.3
RX-MAPLE: HMMOD-UART.5 (TX), IC31.31 (PD1(TXD)), U$4.30 (8/PWM/AIN/RX2), UART0.3
RX_DBG: DBG.3, U$4.14 (25/PWM/RX1)
RX_LED: IC31.2 (PD4(XCK/T0)), R32.1
SCK1: CC0.SCLK, CC1.SCLK, CC2.SCLK, CC2-EXT.SCK (SCLK), CC3.SCLK, U$4.28 (6/AIN/SPI1_SCK)
SCK2: U$4.19 (30/SPI2_SCK)
SWCLK/TCK: U$4.10 (21)
SWDIO/TMS: U$4.11 (22)
SWO/TDO: U$4.8 (19)
TDI: U$4.9 (20)
TX1: U$4.23 (1/TX3/I2C2_SCL), UART1.2
TX-MAPLE: HMMOD-UART.6 (RX), IC31.30 (PD0(RXD)), U$4.31 (9/PWM/AIN/TX2), UART0.2
TX_DBG: DBG.2, U$4.15 (26/PWM/TX1)
VCC: C1.2, C2.2, C3.2, C4.2, C5.1, C6.1, C7.1, C31.1, CC0.VCC, CC1.VCC, CC2.VCC, CC2-EXT.VCC@0 (VCC), CC2-EXT.VCC@1 (VCC), CC3.VCC, DBG.1, HMMOD-UART.1 (VCC), IC31.4 (VCC), IC31.6 (VCC), IC31.18 (AVCC), MYSENS.VCC, R34.1, U$4.1 (VCC), U$4.40 (AV+), UART0.1, UART1.1, X31.P$2 (2)
WIZ_CS: U$4.20 (31/SPI2_SS)
WIZ_RST: U$4.16 (27/PWM)

Notes on the sheet:
Opt
use internal
oscillator
=TX_LED
connect RES and GND
for flashing with bootloader
Radio 1
Radio 0
Radio 2
Radio 3
Transceiver 866 / 433 MHz
LAN
HomeMatic
MySensors
