ranseyer/CUN-STM32/HW-MAPLE-Large/AddOns/1Wire-V01/Addon-mapleCUx_OneWire-RS485-007.sch

## EAGLE design HW-MAPLE-Large/AddOns/1Wire-V01/Addon-mapleCUx_OneWire-RS485-007.sch (2017-12-15)

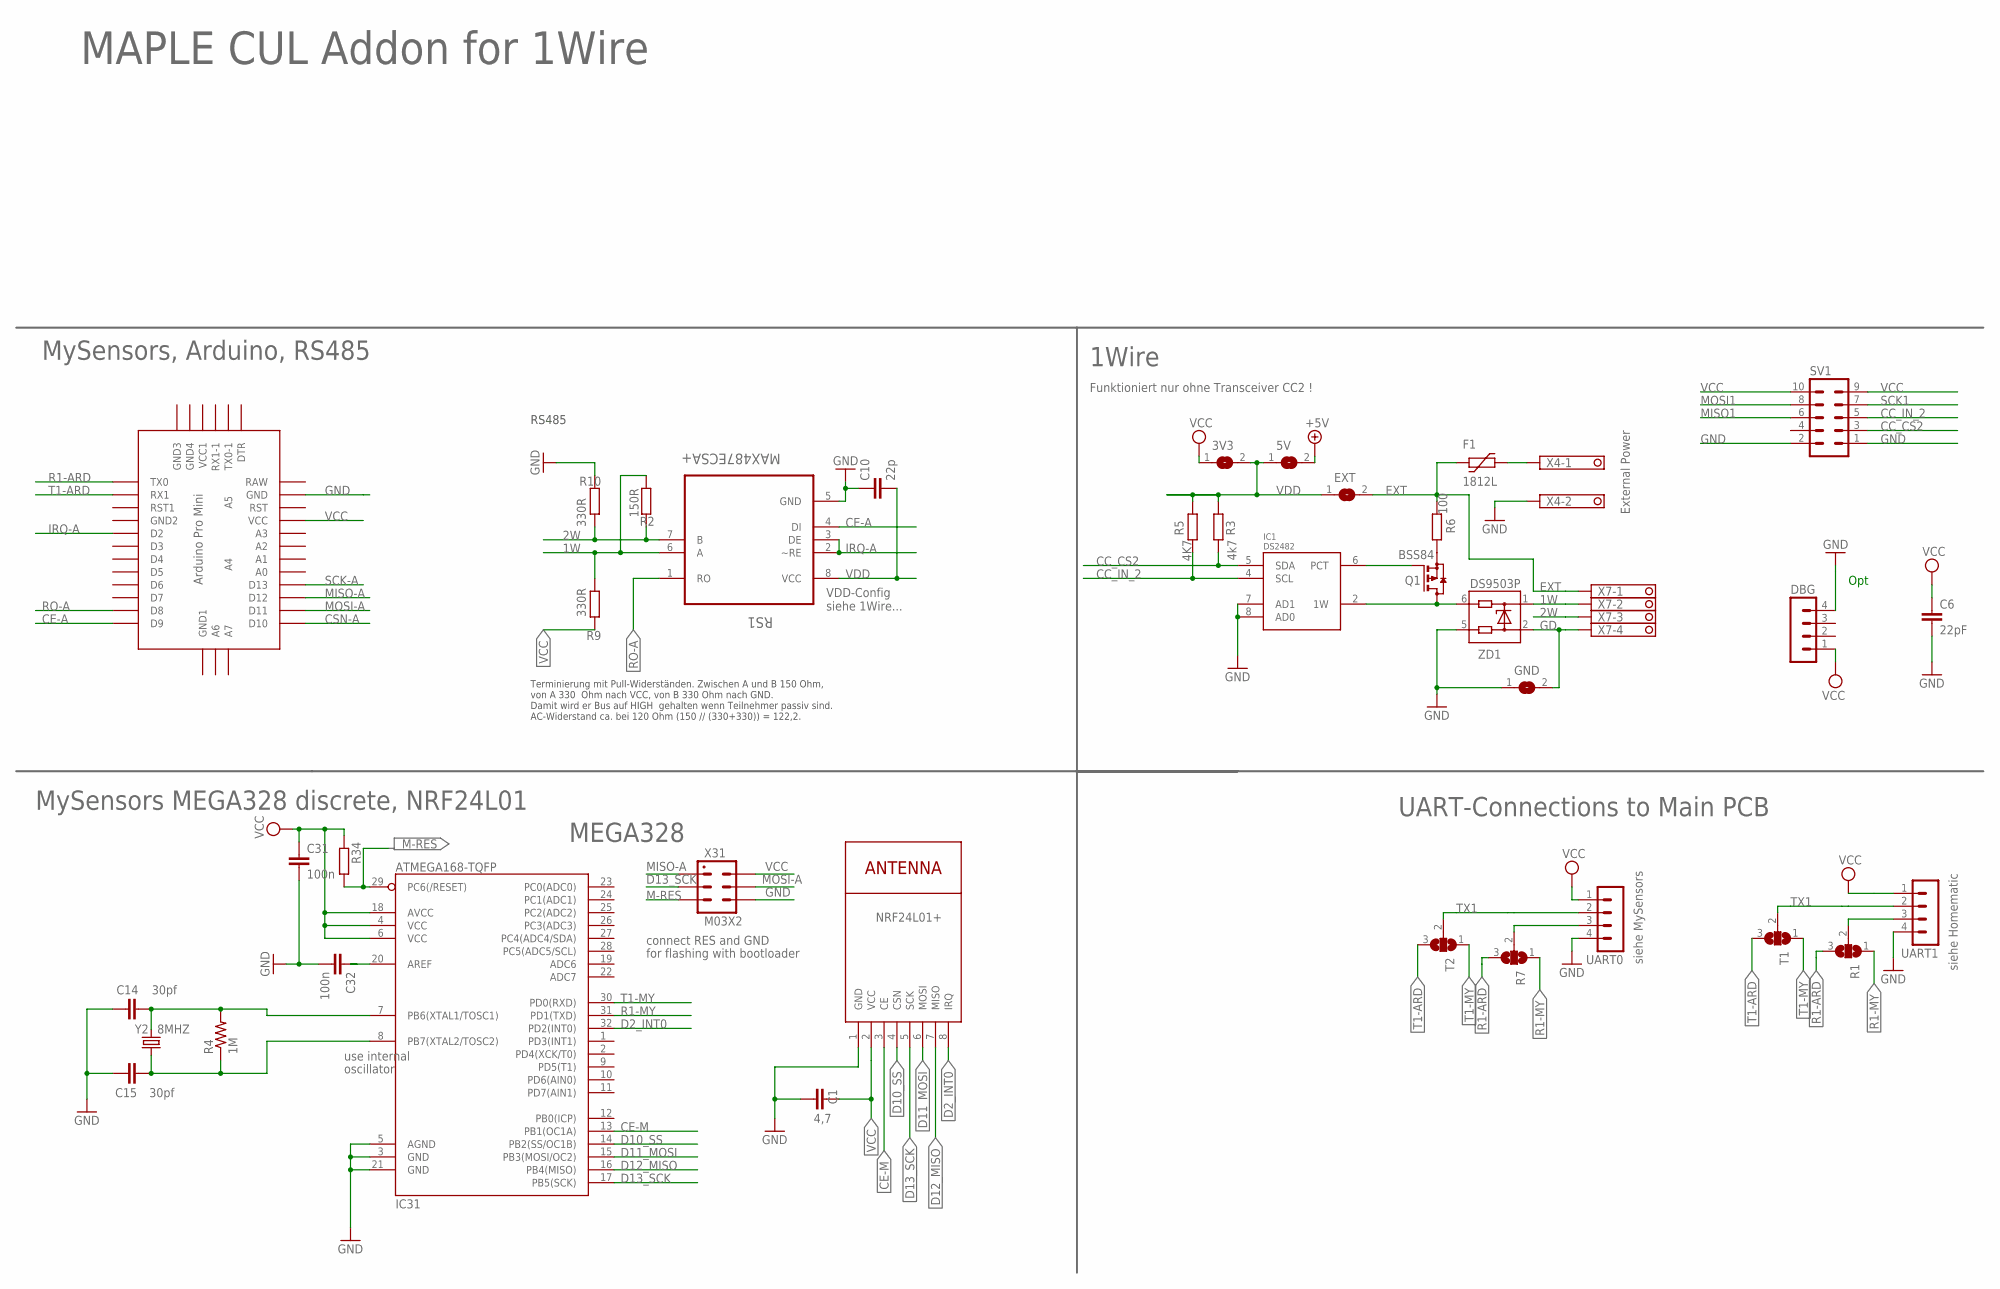
[picture p149: schematic Addon-mapleCUx_OneWire-RS485-007.sch]

Parts:
3V3, 5V: SJ
C1: 4,7; C1210
C6: 22pF; C0805
C10: 22p; C0805
C14, C15: 30pf; 0805
C31, C32: 100n; C0805
DBG: MA04-1
EXT: SJ
F1: 1812L
GND: SJ
IC1: DS2482; SO08
IC31: ATMEGA168-TQFP; TQFP32-08
NRF24L01+: NRF24L01+; WIRELESS-NRF24L01
Q1: BSS84; SOT23
R1, R7: SJ2W; SJ_2
R2: 150R; R0805
R3: 4k7; R0805
R4: 1M; 0805
R5: 4K7; R0805
R6: 100; R0805
R9, R10: 330R; R0805
R34: R-EU_R0805; R0805
RS1: MAX487ECSA+; SOIC127P600X175-8N
SV1: MA05-2
T1, T2: SJ2W; SJ_2
U$1: ABK-PRO-MINI
UART0, UART1: MA04-1
X4: 1751248
X7: 1751264
X31: M03X2; 2X03-1.27MM_SMD
Y2: 8MHZ; CRYSTAL-TXC-7A
ZD1: DS9503P; TSOC6

Connections:
1W: R2.1, R9.2, RS1.6 (A), X7.2, ZD1.1
2W: R2.2, R10.1, RS1.7 (B), X7.3
+5V: 5V.2
CC_CS2: IC1.5 (SDA), R3.2, SV1.3
CC_IN_2: IC1.4 (SCL), R5.2, SV1.5
CE-A: RS1.4 (DI), U$1.D9
CE-M: IC31.13 (PB1(OC1A)), NRF24L01+.3 (CE)
CSN-A: U$1.D10
D2_INT0: IC31.32 (PD2(INT0)), NRF24L01+.8 (IRQ)
D10_SS: IC31.14 (PB2(SS/OC1B)), NRF24L01+.4 (CSN)
D11_MOSI: IC31.15 (PB3(MOSI/OC2)), NRF24L01+.6 (MOSI)
D12_MISO: IC31.16 (PB4(MISO)), NRF24L01+.7 (MISO)
D13_SCK: IC31.17 (PB5(SCK)), NRF24L01+.5 (SCK), X31.P$3 (3)
EXT: EXT.2, F1.P$1 (1), R6.2, X7.1
GD: GND.2, X7.4, ZD1.2
GND: C1.1, C6.2, C10.1, C14.1, C15.1, C31.2, C32.2, DBG.4, GND.1, IC1.7 (AD1), IC1.8 (AD0), IC31.3 (GND), IC31.5 (AGND), IC31.21 (GND), NRF24L01+.1 (GND), R10.2, RS1.5 (GND), SV1.1, SV1.2, U$1.GND, UART0.4, UART1.4, X4.2, X31.P$6 (6), ZD1.5
IRQ-A: RS1.2 (~RE), RS1.3 (DE), U$1.D2
M-RES: IC31.29 (PC6(/RESET)), R34.2, X31.P$5 (5)
MISO1: SV1.6
MISO-A: U$1.D12, X31.P$1 (1)
MOSI1: SV1.8
MOSI-A: U$1.D11, X31.P$4 (4)
unnamed: C14.2, IC31.7 (PB6(XTAL1/TOSC1)), R4.2, Y2.P$2 (2)
unnamed: C32.1, IC31.20 (AREF)
unnamed: C15.2, IC31.8 (PB7(XTAL2/TOSC2)), R4.1, Y2.P$1 (1)
unnamed: F1.P$2 (2), X4.1
unnamed: IC1.6 (PCT), Q1.1 (G)
unnamed: IC1.2 (1W), Q1.3 (D), ZD1.6
unnamed: Q1.2 (S), R6.1
R1-ARD: R1.3, R7.3, U$1.TX0
R1-MY: IC31.31 (PD1(TXD)), R1.1, R7.1
RO-A: RS1.1 (RO), U$1.D8
RX1: R1.2, R7.2, UART0.3, UART1.3
SCK1: SV1.7
SCK-A: U$1.D13
T1-ARD: T1.3, T2.3, U$1.RX1
T1-MY: IC31.30 (PD0(RXD)), T1.1, T2.1
TX1: T1.2, T2.2, UART0.2, UART1.2
VCC: 3V3.1, C1.2, C6.1, C31.1, DBG.1, IC31.4 (VCC), IC31.6 (VCC), IC31.18 (AVCC), R9.1, R34.1, SV1.9, SV1.10, U$1.VCC, UART0.1, UART1.1, X31.P$2 (2)
VDD: 3V3.2, 5V.1, C10.2, EXT.1, R3.1, R5.1, RS1.8 (VCC)

Notes on the sheet:
Opt
siehe Homematic
siehe MySensors
MySensors MEGA328 discrete, NRF24L01
MEGA328
use internal
oscillator
connect RES and GND
for flashing with bootloader
1Wire
External Power
Funktioniert nur ohne Transceiver CC2 !
MySensors, Arduino, RS485
RS485
VDD-Config siehe 1Wire...
Terminierung mit Pull-Widerständen. Zwischen A und B 150 Ohm, von A 330 Ohm nach VCC, von B 330 Ohm nach GND. Damit wird er Bus auf HIGH gehalten wenn Teilnehmer passiv sind. AC-Widerstand ca. bei 120 Ohm (150 // (330+330)) = 122,2.
UART-Connections to Main PCB
MAPLE CUL Addon for 1Wire
