ranseyer/CUN-STM32/HW-MAPLE-Large/AddOns/Addon-LAN-WLAN-without-MAPLE/Addon-LAN-WLAN-without-MAPLE-V01-001.sch

## EAGLE design HW-MAPLE-Large/AddOns/Addon-LAN-WLAN-without-MAPLE/Addon-LAN-WLAN-without-MAPLE-V01-001.sch (2019-02-17)

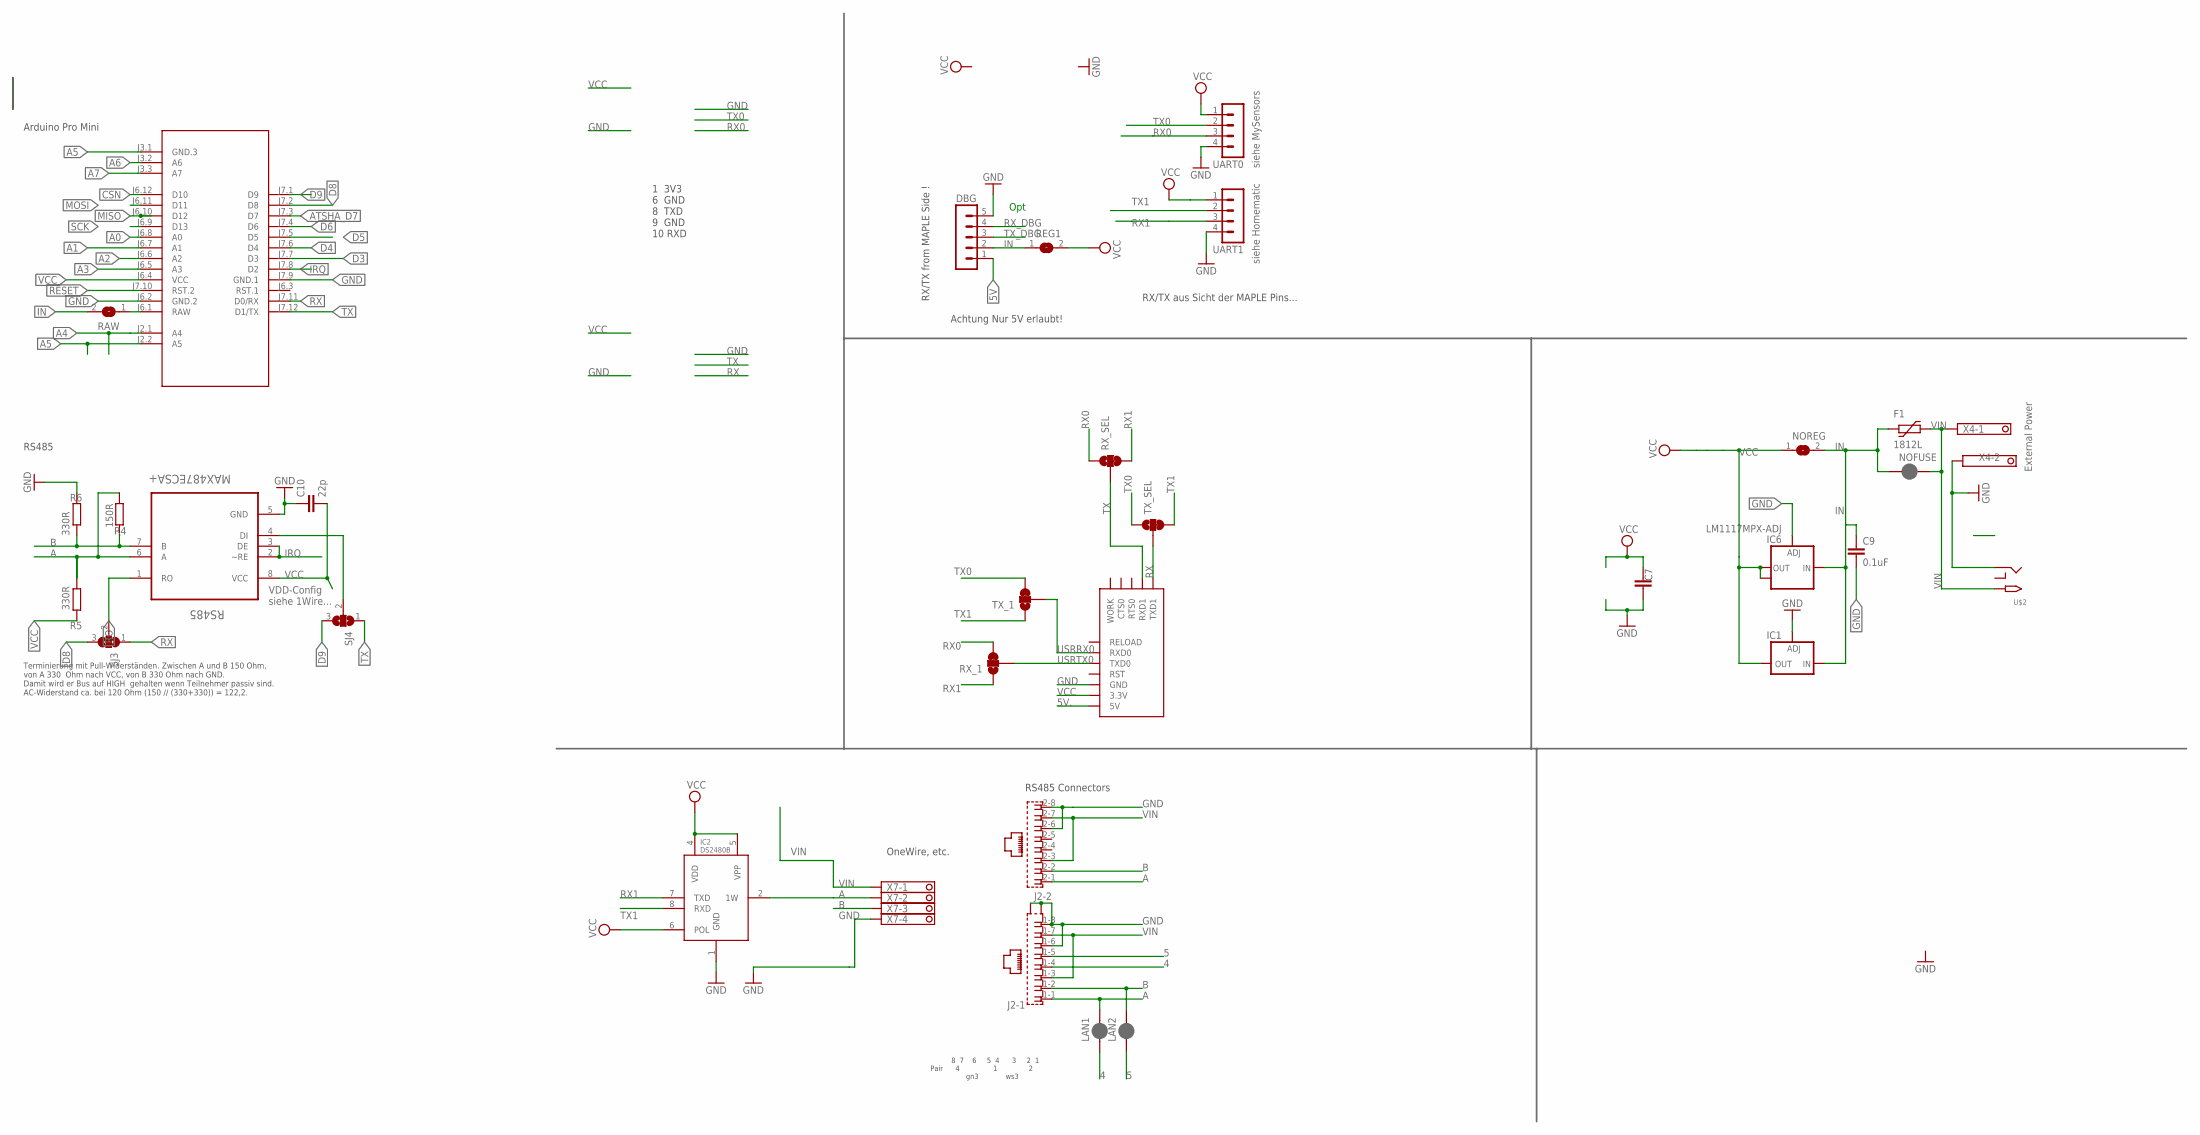
[picture p150: schematic Addon-LAN-WLAN-without-MAPLE-V01-001.sch]

Parts:
C7: C-EUC1812; C1812
C9: 0.1uF; C1206
C10: 22p; C0805
DBG: MA05-1
F1: 1812L
IC1: LD117ADT50TR; DPACK
IC2: DS2480B; SO08
IC6: LM1117MPX-ADJ; SOT223
J2: RJ45_2X_S
LAN1, LAN2: JUMPER-SMT_2_NC_PASTE_SILK; SMT-JUMPER_2_NC_PASTE_SILK
M1: ARDUINO-PRO-MINI-3.3V#NP; ARDUINO-PRO-MINI#NP
NOFUSE: JUMPER-SMT_2_NC_PASTE_NO-SILK; SMT-JUMPER_2_NC_PASTE_NO-SILK
NOREG: SJ
R4: 150R; R0805
R5, R6: 330R; R0805
RAW: SJ
REG1: SJ
RS485: MAX487ECSA+; SOIC127P600X175-8N
RX_1: JUMPER-SMT_3_1-NC_TRACE_SILK; SMT-JUMPER_3_1-NC_TRACE_SILK
RX_SEL: JUMPER-SMT_3_1-NC_TRACE_SILK; SMT-JUMPER_3_1-NC_TRACE_SILK
SJ3, SJ4: SJ2W; SJ_2
TX_1: JUMPER-SMT_3_1-NC_TRACE_SILK; SMT-JUMPER_3_1-NC_TRACE_SILK
TX_SEL: JUMPER-SMT_3_1-NC_TRACE_SILK; SMT-JUMPER_3_1-NC_TRACE_SILK
U$2: 2.1MMJACKTHM; PJ-102A
U$5: USR-TCP232-E2
UART0, UART1: MA04-1
X4: 1751248
X7: 1751264

Connections:
4: J2.1-4 (4), LAN1.1
5: J2.1-5 (5), LAN2.1
5V: DBG.1
5V.: U$5.5V
A: IC2.2 (1W), J2.1-1 (1), J2.2-1 (1), LAN1.2, R4.1, R5.2, RS485.6 (A), X7.2
A0: M1.J6.8 (A0)
A1: M1.J6.7 (A1)
A2: M1.J6.6 (A2)
A3: M1.J6.5 (A3)
A4: M1.J2.1 (A4)
A5: M1.J2.2 (A5), M1.J3.1 (GND.3)
A6: M1.J3.2 (A6)
A7: M1.J3.3 (A7)
ATSHA_D7: M1.J7.3 (D7)
B: J2.1-2 (2), J2.2-2 (2), LAN2.2, R4.2, R6.1, RS485.7 (B), X7.3
CSN: M1.J6.12 (D10)
D3: M1.J7.7 (D3)
D4: M1.J7.6 (D4)
D5: M1.J7.5 (D5)
D6: M1.J7.4 (D6)
D8: M1.J7.2 (D8), SJ3.3
D9: M1.J7.1 (D9), SJ4.3
DI1: RS485.4 (DI), SJ4.2
GND: C7.1, C9.2, C10.1, DBG.5, IC1.1 (ADJ), IC2.1 (GND), IC6.1 (ADJ), J2.1-6 (6), J2.1-8 (8), J2.2-6 (6), J2.2-8 (8), J2.G1 (S2), J2.G3 (S1), M1.J6.2 (GND.2), M1.J7.9 (GND.1), R6.2, RS485.5 (GND), U$2.RING, U$5.GND, UART0.4, UART1.4, X4.2, X7.4
IN: C9.1, DBG.2, F1.P$1 (1), IC1.3 (IN), IC6.3 (IN), NOFUSE.1, NOREG.2, RAW.2, REG1.1
IRQ: M1.J7.8 (D2), RS485.2 (~RE), RS485.3 (DE)
MISO: M1.J6.10 (D12)
MOSI: M1.J6.11 (D11)
RAW1: M1.J6.1 (RAW), RAW.1
RESET: M1.J7.10 (RST.2)
RO: RS485.1 (RO), SJ3.2
RX: M1.J7.11 (D0/RX), SJ3.1, TX_SEL.2, U$5.TXD1
RX0: RX_1.3, RX_SEL.1, UART0.3
RX1: IC2.7 (TXD), RX_1.1, RX_SEL.3, UART1.3
RX_DBG: DBG.4
SCK: M1.J6.9 (D13)
TX: M1.J7.12 (D1/TX), RX_SEL.2, SJ4.1, U$5.RXD1
TX0: TX_1.3, TX_SEL.1, UART0.2
TX1: IC2.8 (RXD), TX_1.1, TX_SEL.3, UART1.2
TX_DBG: DBG.3
USRRX0: TX_1.2, U$5.RXD0
USRTX0: RX_1.2, U$5.TXD0
VCC: C7.2, C10.2, IC1.4 (OUT), IC2.4 (VDD), IC2.5 (VPP), IC2.6 (POL), IC6.2 (OUT), IC6.TAB (OUT1), M1.J6.4 (VCC), NOREG.1, R5.1, REG1.2, RS485.8 (VCC), U$5.3.3V, UART0.1, UART1.1
VIN: F1.P$2 (2), J2.1-3 (3), J2.1-7 (7), J2.2-3 (3), J2.2-7 (7), NOFUSE.2, U$2.TIP, X4.1, X7.1

Notes on the sheet:
Opt
siehe Homematic
siehe MySensors
1 3V3 6 GND 8 TXD 9 GND 10 RXD
RX/TX from MAPLE Side !
External Power
RX/TX aus Sicht der MAPLE Pins...
Achtung Nur 5V erlaubt!
8 7 6 5 4 3 2 1 Pair 4 1 2 gn3 ws3
RS485 Connectors
OneWire, etc.
Arduino Pro Mini
RS485
VDD-Config siehe 1Wire...
Terminierung mit Pull-Widerständen. Zwischen A und B 150 Ohm, von A 330 Ohm nach VCC, von B 330 Ohm nach GND. Damit wird er Bus auf HIGH gehalten wenn Teilnehmer passiv sind. AC-Widerstand ca. bei 120 Ohm (150 // (330+330)) = 122,2.
