ranseyer/CUN-STM32/HW-MAPLE-Large/AddOns/RFM69-usw-V11/Addon-mapleCUx_HM-RFM69-RFM95-V12-001.sch

## EAGLE design HW-MAPLE-Large/AddOns/RFM69-usw-V11/Addon-mapleCUx_HM-RFM69-RFM95-V12-001.sch (2018-08-07)

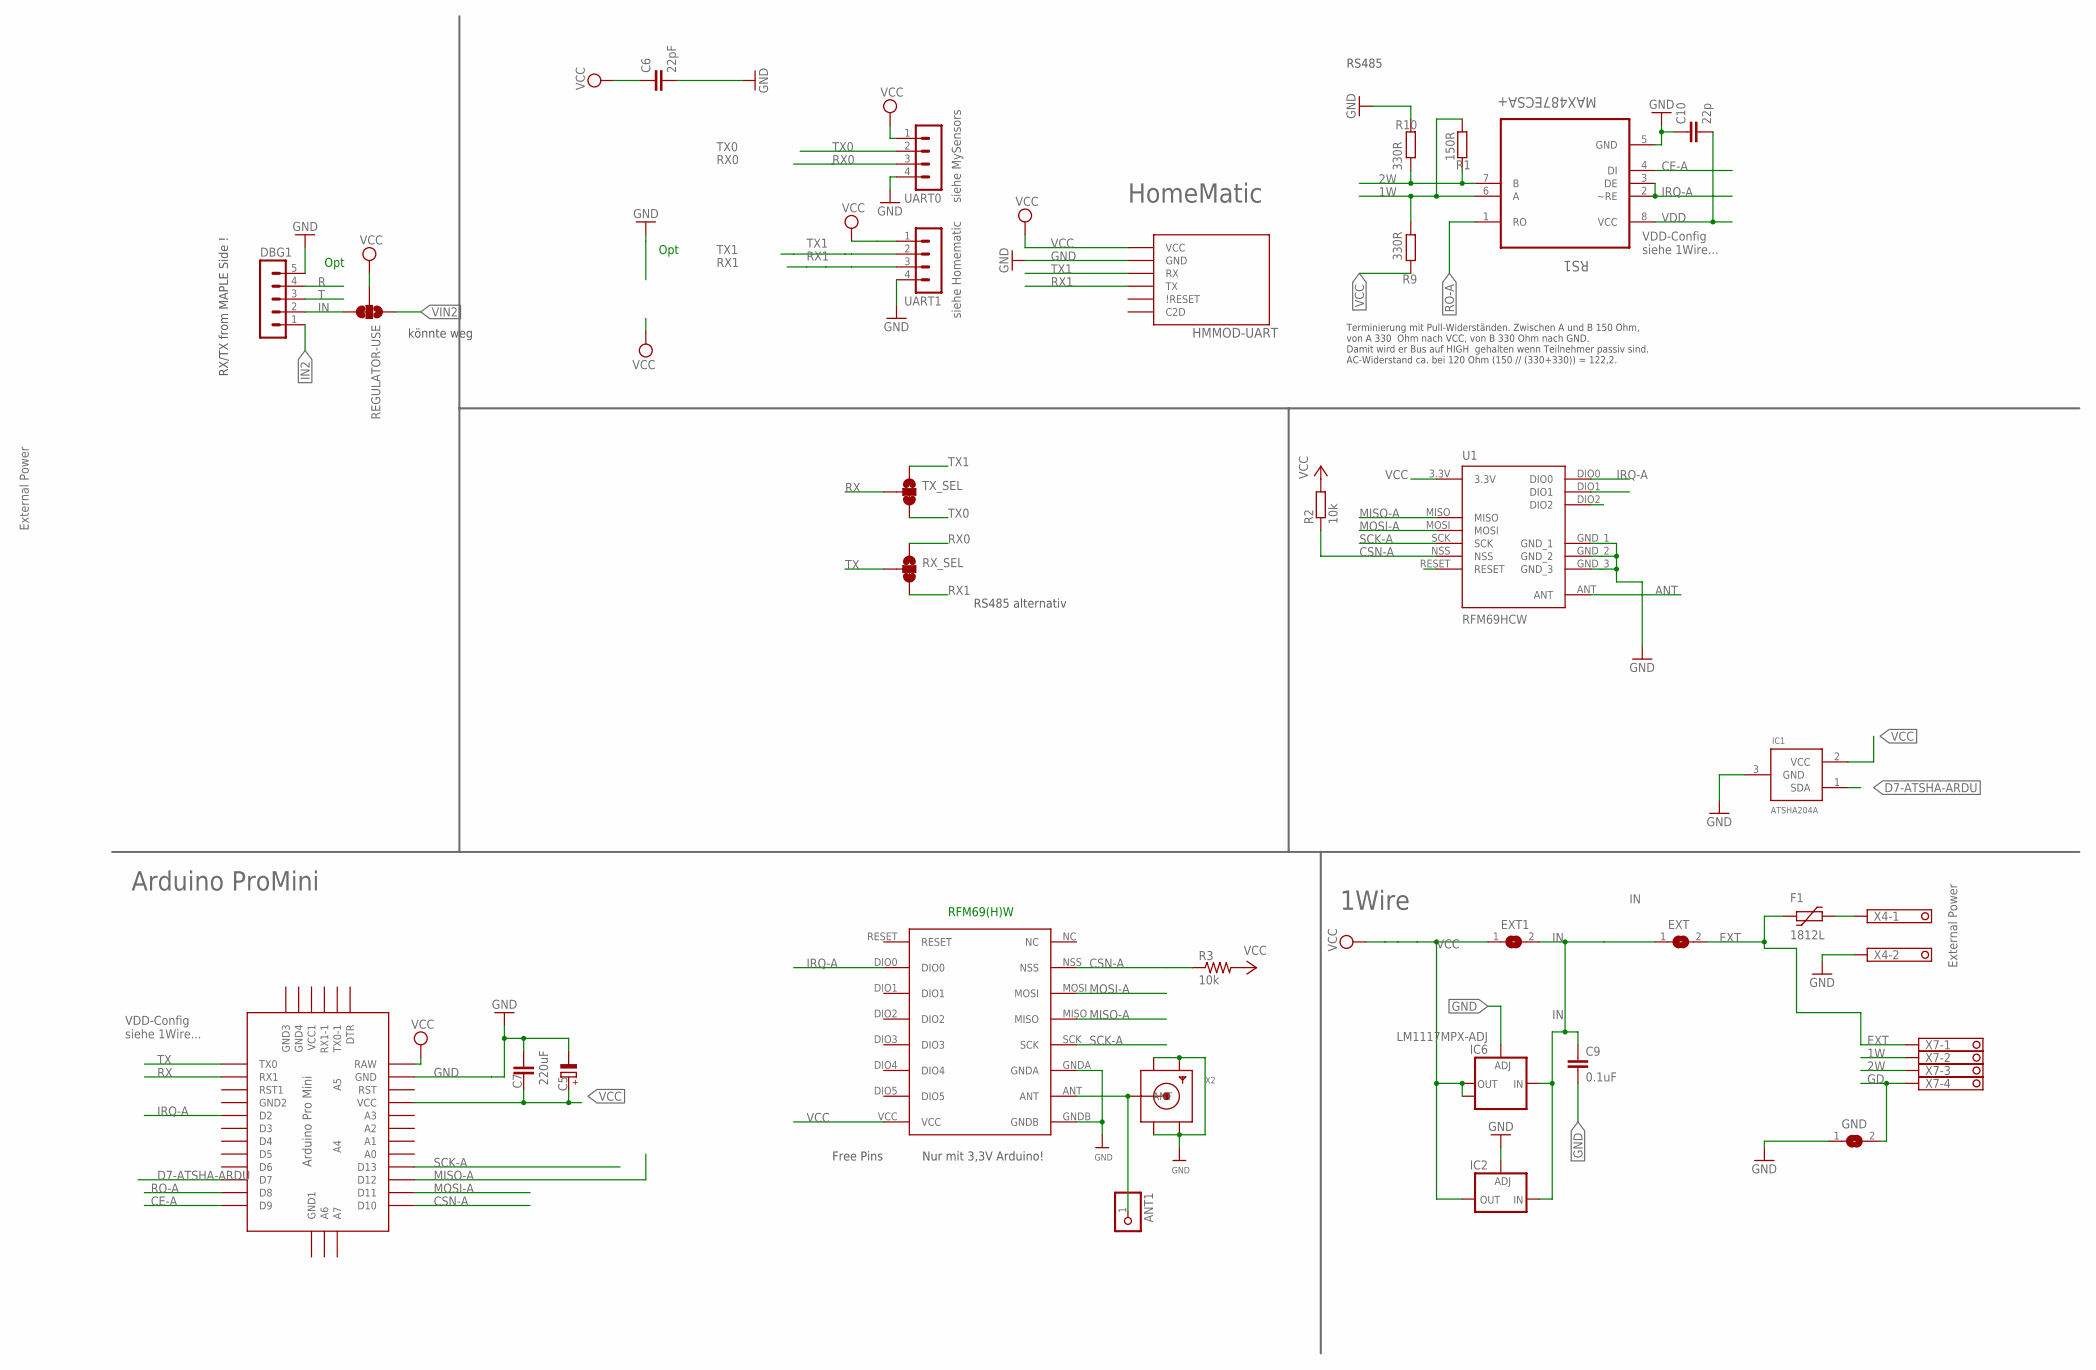
[picture p152: schematic Addon-mapleCUx_HM-RFM69-RFM95-V12-001.sch]

Parts:
ANT1: PINHD-1X1; 1X01
C5: 220uF; E5-8,5
C6: 22pF; C0805
C7: C-EUC1812; C1812
C9: 0.1uF; C1206
C10: 22p; C0805
DBG1: MA05-1
EXT, EXT1: SJ
F1: 1812L
GND: SJ
HMMOD-UART: HM-MOD-UARTDIL; HM-MOD-UART-DIL
IC1: ATSHA204A; SOT23
IC2: LD117ADT50TR; DPACK
IC6: LM1117MPX-ADJ; SOT223
R1: 150R; R0805
R2: 10k; M0805
R3: 10k; 0805
R9, R10: 330R; R0805
REGULATOR-USE: JUMPER-SMT_3_1-NC_TRACE_SILK; SMT-JUMPER_3_1-NC_TRACE_SILK
RFM69W: RFM69HW; RFM
RS1: MAX487ECSA+; SOIC127P600X175-8N
RX_SEL: JUMPER-SMT_3_1-NC_TRACE_SILK; SMT-JUMPER_3_1-NC_TRACE_SILK
TX_SEL: JUMPER-SMT_3_1-NC_TRACE_SILK; SMT-JUMPER_3_1-NC_TRACE_SILK
U1: RFM69HCW; RFM69HCW-XXXS2
U$2: ABK-PRO-MINI
UART0, UART1: MA04-1
X2: SMACONNECTOR_EDGE; SMA_EDGELAUNCH
X4: 1751248
X7: 1751264

Connections:
1W: R1.1, R9.2, RS1.6 (A), X7.2
2W: R1.2, R10.1, RS1.7 (B), X7.3
ANT: ANT1.1, RFM69W.ANT, U1.ANT, X2.P (ANT)
CE-A: RS1.4 (DI), U$2.D9
CSN-A: R2.1, R3.1, RFM69W.NSS, U1.NSS, U$2.D10
D7-ATSHA-ARDU: IC1.1 (SDA), U$2.D7
EXT: EXT.2, F1.P$1 (1), X7.1
GD: GND.2, X7.4
GND: C5.-, C6.2, C7.1, C9.2, C10.1, DBG1.5, GND.1, HMMOD-UART.2 (GND), IC1.3 (GND), IC2.1 (ADJ), IC6.1 (ADJ), R10.2, RFM69W.GNDA, RFM69W.GNDB, RS1.5 (GND), U1.GND_1, U1.GND_2, U1.GND_3, U$2.GND, UART0.4, UART1.4, X2.GND@1 (GND4), X2.GND@2 (GND3), X2.GND@3 (GND2), X2.GND@4 (GND1), X4.2
IN: C9.1, DBG1.2, EXT.1, EXT1.2, IC2.3 (IN), IC6.3 (IN), REGULATOR-USE.3
IN2: DBG1.1
IRQ-A: RFM69W.DIO0, RS1.2 (~RE), RS1.3 (DE), U1.DIO0, U$2.D2
MISO-A: RFM69W.MISO, U1.MISO, U$2.D12
MOSI-A: RFM69W.MOSI, U1.MOSI, U$2.D11
unnamed: F1.P$2 (2), X4.1
R: DBG1.4
RO-A: RS1.1 (RO), U$2.D8
RX: TX_SEL.2, U$2.RX1
RX0: RX_SEL.1, UART0.3
RX1: HMMOD-UART.5 (TX), RX_SEL.3, UART1.3
SCK-A: RFM69W.SCK, U1.SCK, U$2.D13
T: DBG1.3
TX: RX_SEL.2, U$2.TX0
TX0: TX_SEL.3, UART0.2
TX1: HMMOD-UART.6 (RX), TX_SEL.1, UART1.2
VCC: C5.+, C6.1, C7.2, EXT1.1, HMMOD-UART.1 (VCC), IC1.2 (VCC), IC2.4 (OUT), IC6.2 (OUT), IC6.TAB (OUT1), R2.2, R3.2, R9.1, REGULATOR-USE.2, RFM69W.VCC, U1.3.3V, U$2.RAW, U$2.VCC, UART0.1, UART1.1
VDD: C10.2, RS1.8 (VCC)
VIN2: REGULATOR-USE.1

Notes on the sheet:
Opt
siehe Homematic
siehe MySensors
HomeMatic
Arduino ProMini
VDD-Config siehe 1Wire...
RS485
Terminierung mit Pull-Widerständen. Zwischen A und B 150 Ohm, von A 330 Ohm nach VCC, von B 330 Ohm nach GND. Damit wird er Bus auf HIGH gehalten wenn Teilnehmer passiv sind. AC-Widerstand ca. bei 120 Ohm (150 // (330+330)) = 122,2.
1Wire
External Power
Free Pins
RFM69(H)W
Nur mit 3,3V Arduino!
RS485 alternativ
RX/TX from MAPLE Side !
könnte weg
