ranseyer/CUN-STM32/HW-MAPLE-Large/AddOns/RasPi-UART-V01/Addon-mapleCUx_Raspi-3V3-UART-Adapter-008-ohne GNDFlaeche.sch

## EAGLE design HW-MAPLE-Large/AddOns/RasPi-UART-V01/Addon-mapleCUx_Raspi-3V3-UART-Adapter-008-ohne GNDFlaeche.sch (2018-06-11)

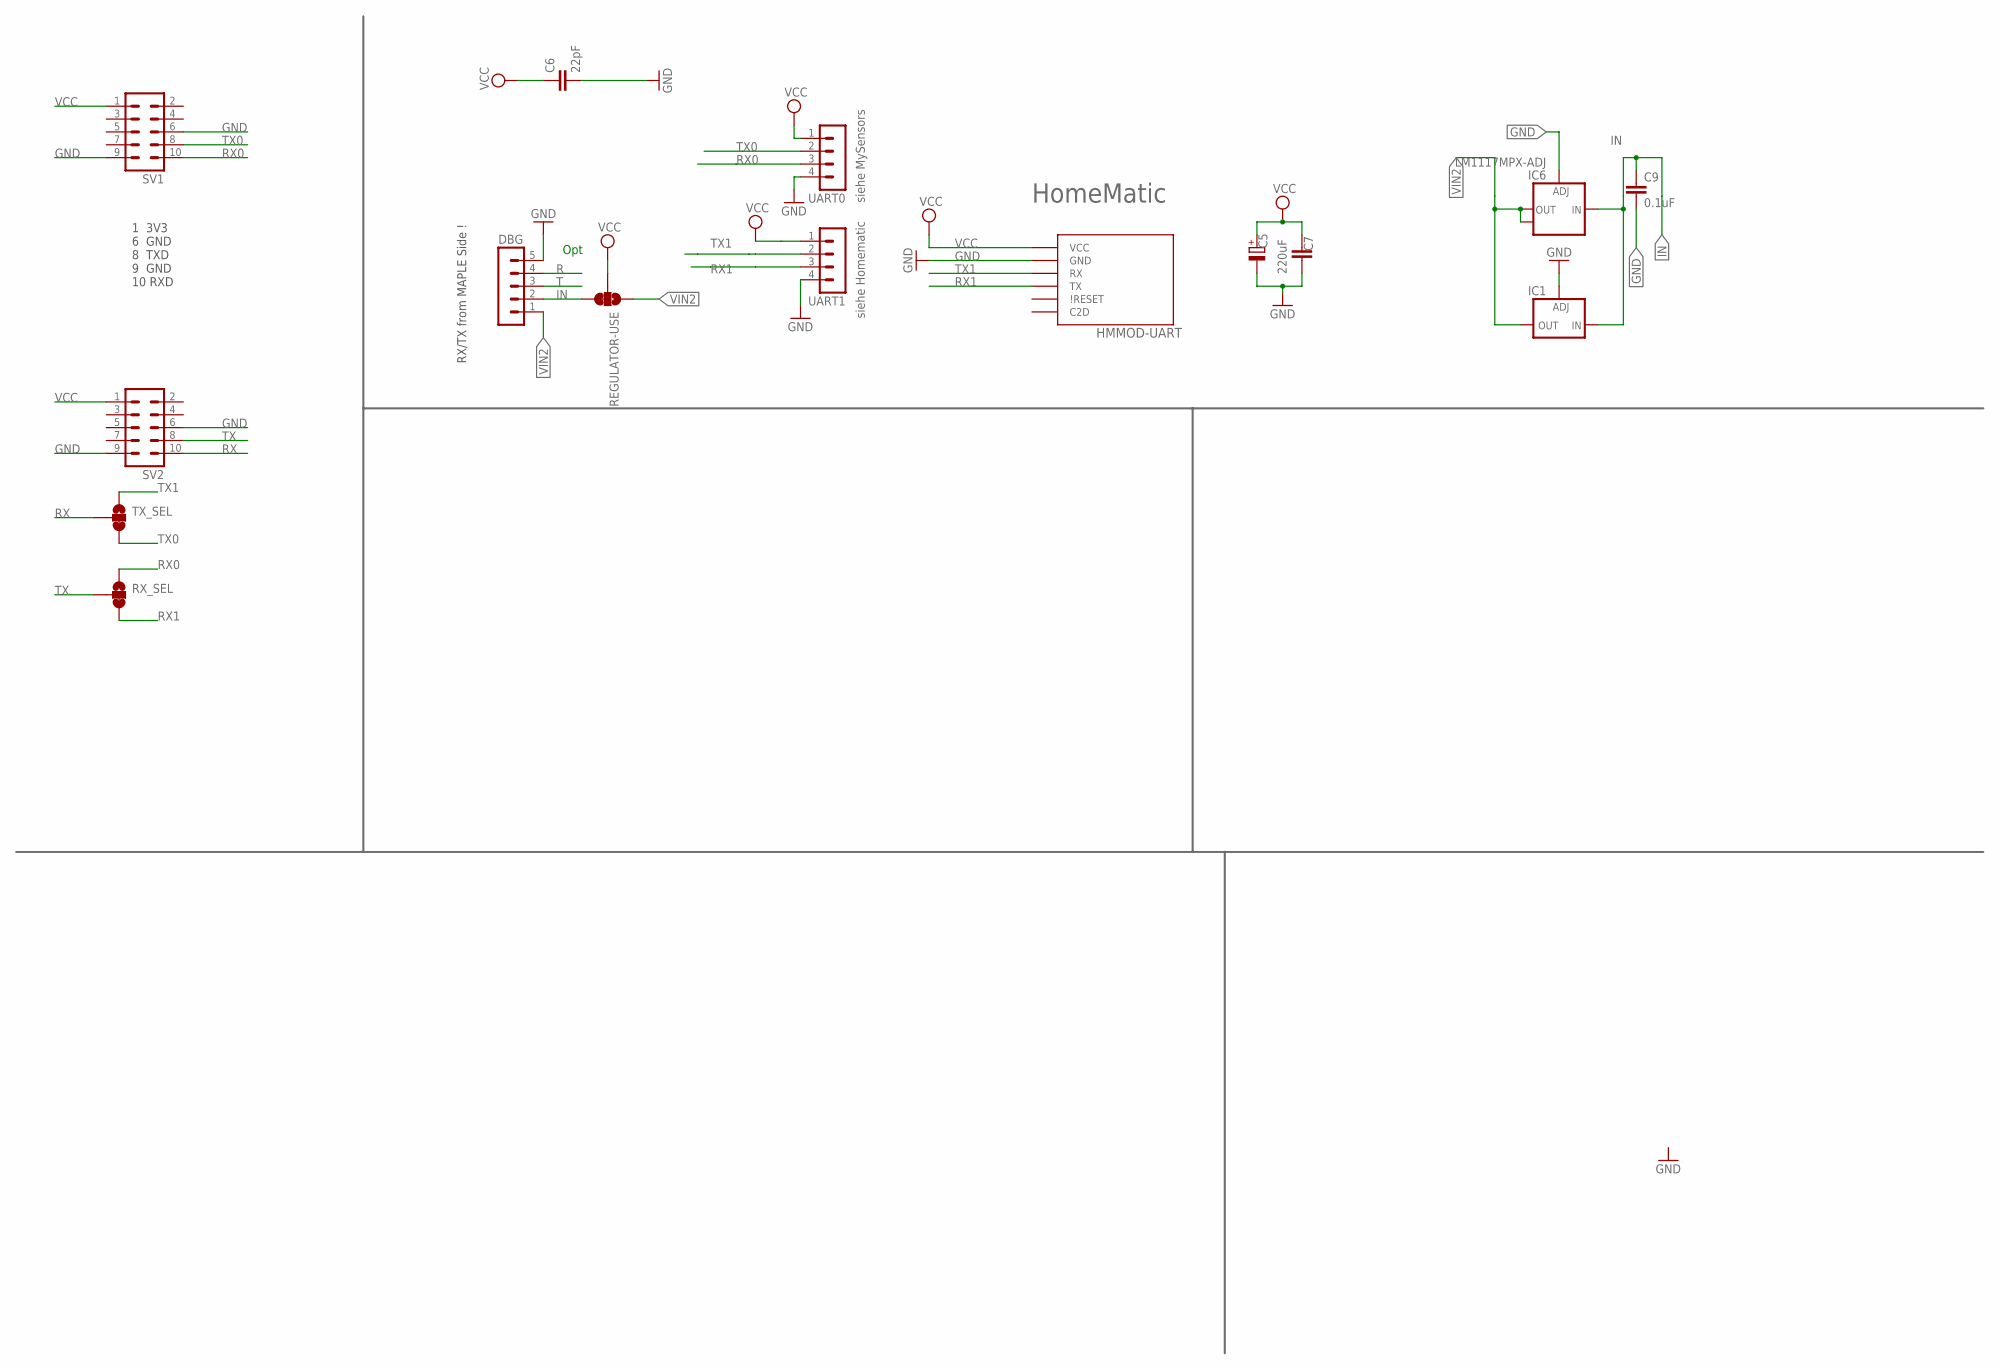
[picture p153: schematic Addon-mapleCUx_Raspi-3V3-UART-Adapter-008-ohne GNDFlaeche.sch]

Parts:
C5: 220uF; E5-8,5
C6: 22pF; C0805
C7: C-EUC1812; C1812
C9: 0.1uF; C1206
DBG: MA05-1
HMMOD-UART: HM-MOD-UARTDIL; HM-MOD-UART-DIL
IC1: LD117ADT50TR; DPACK
IC6: LM1117MPX-ADJ; SOT223
REGULATOR-USE: JUMPER-SMT_3_1-NC_TRACE_SILK; SMT-JUMPER_3_1-NC_TRACE_SILK
RX_SEL: JUMPER-SMT_3_1-NC_TRACE_SILK; SMT-JUMPER_3_1-NC_TRACE_SILK
SV1, SV2: MA05-2
TX_SEL: JUMPER-SMT_3_1-NC_TRACE_SILK; SMT-JUMPER_3_1-NC_TRACE_SILK
UART0, UART1: MA04-1

Connections:
GND: C5.-, C6.2, C7.1, C9.2, DBG.5, HMMOD-UART.2 (GND), IC1.1 (ADJ), IC6.1 (ADJ), SV1.6, SV1.9, SV2.6, SV2.9, UART0.4, UART1.4
IN: C9.1, DBG.2, IC1.3 (IN), IC6.3 (IN), REGULATOR-USE.3
R: DBG.4
RX: SV2.10, TX_SEL.2
RX0: RX_SEL.1, SV1.10, UART0.3
RX1: HMMOD-UART.5 (TX), RX_SEL.3, UART1.3
T: DBG.3
TX: RX_SEL.2, SV2.8
TX0: SV1.8, TX_SEL.3, UART0.2
TX1: HMMOD-UART.6 (RX), TX_SEL.1, UART1.2
VCC: C5.+, C6.1, C7.2, HMMOD-UART.1 (VCC), REGULATOR-USE.2, SV1.1, SV2.1, UART0.1, UART1.1
VIN2: DBG.1, IC1.4 (OUT), IC6.2 (OUT), IC6.TAB (OUT1), REGULATOR-USE.1

Notes on the sheet:
Opt
siehe Homematic
siehe MySensors
HomeMatic
1 3V3 6 GND 8 TXD 9 GND 10 RXD
RX/TX from MAPLE Side !
