ranseyer/CUN-STM32/HW-MAPLE-Large/AddOns/RasPi-UART__Zigbee-CC2530/Addon-mapleCUx_Raspi-3V3-UART-CC2530-V04-006.sch

## EAGLE design HW-MAPLE-Large/AddOns/RasPi-UART__Zigbee-CC2530/Addon-mapleCUx_Raspi-3V3-UART-CC2530-V04-006.sch (2019-03-26)

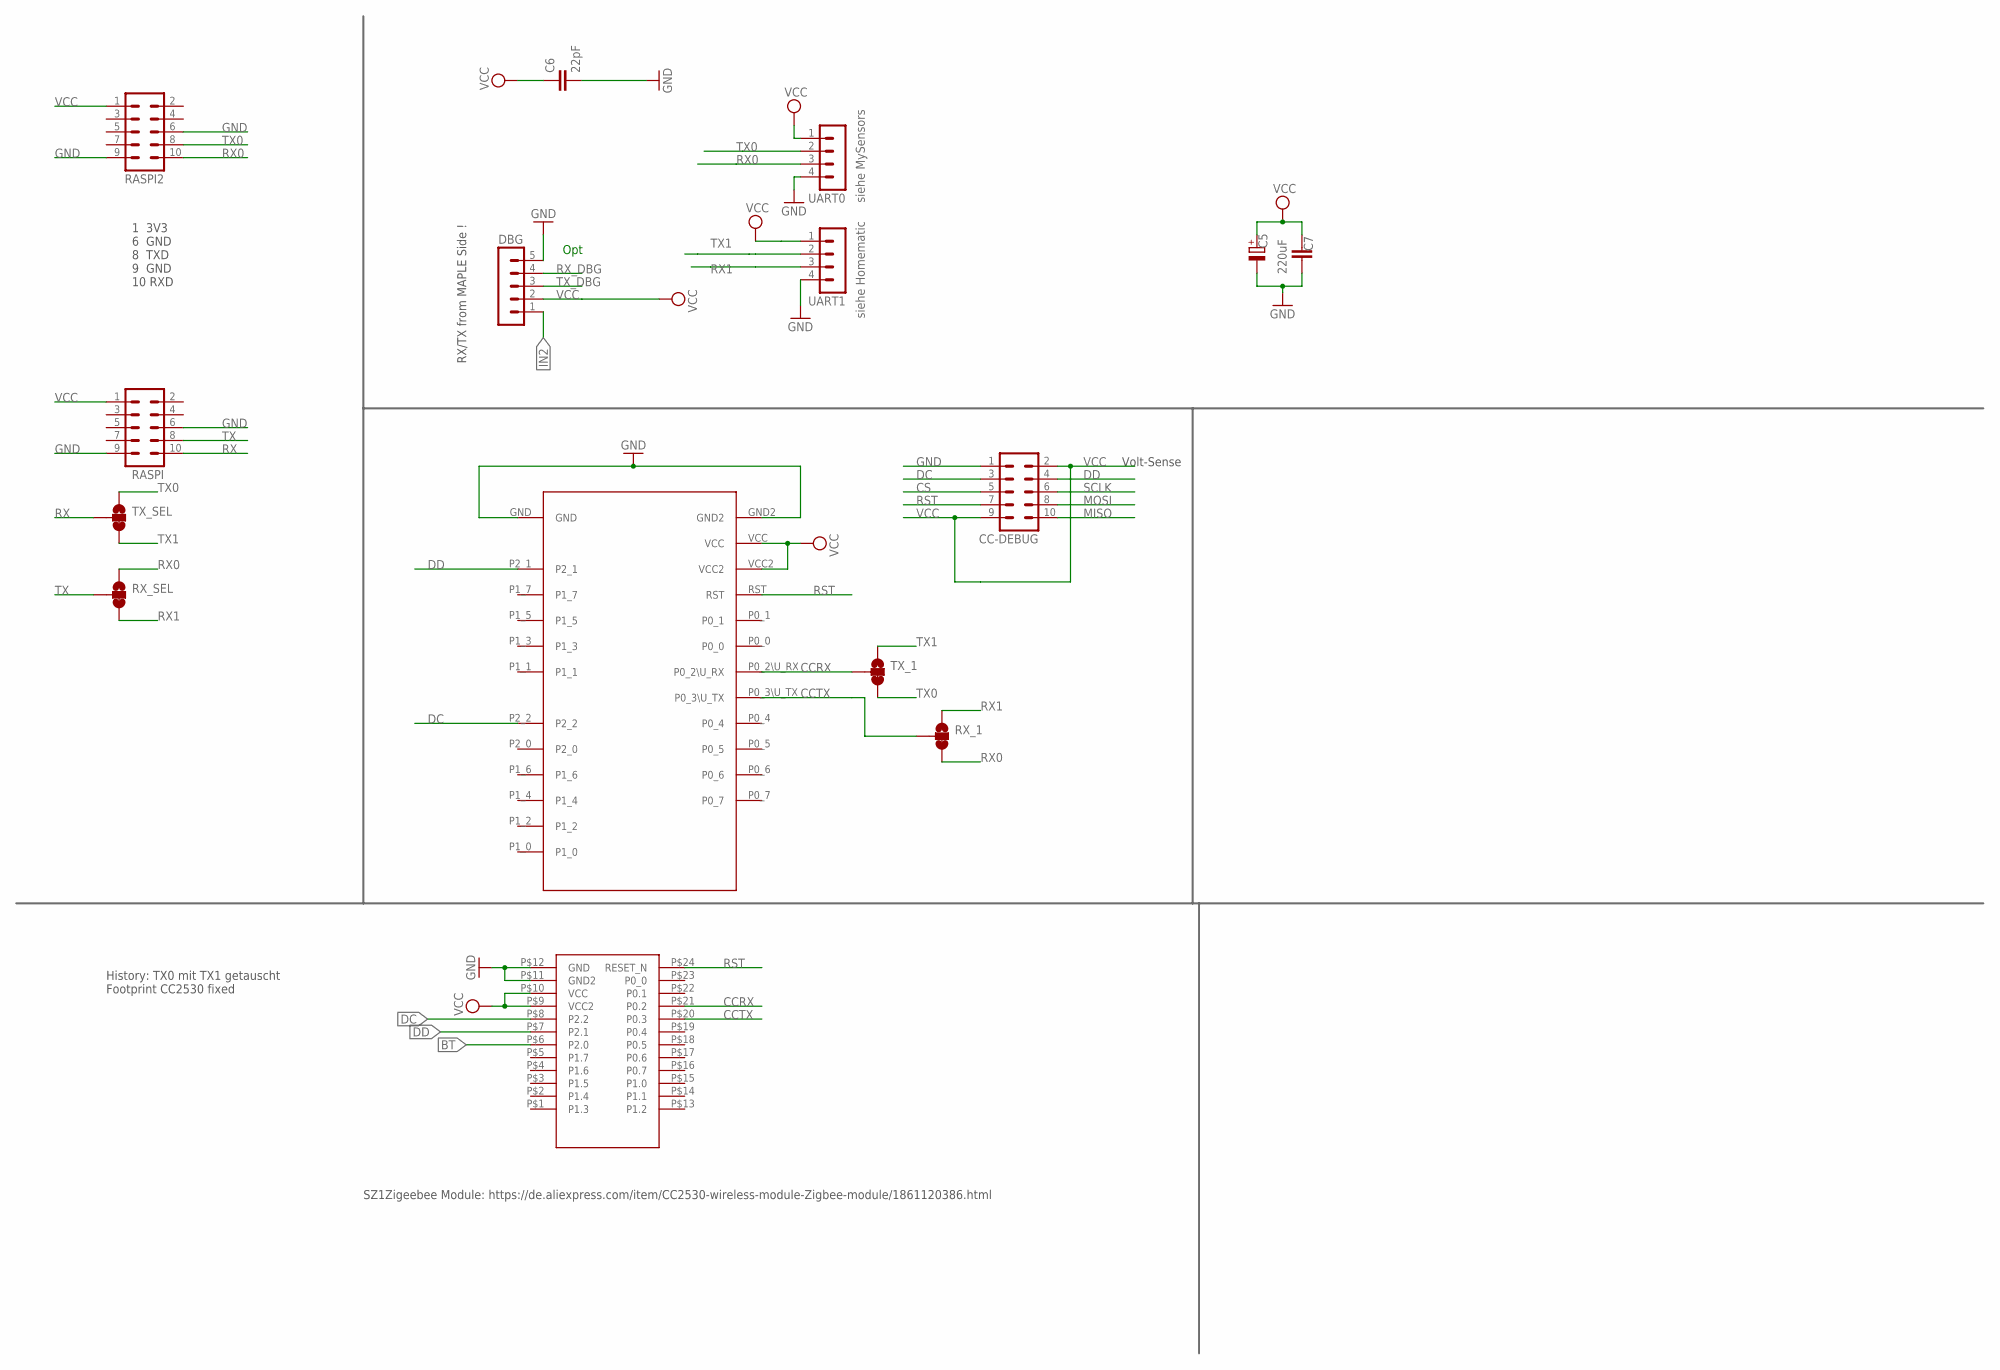
[picture p155: schematic Addon-mapleCUx_Raspi-3V3-UART-CC2530-V04-006.sch]

Parts:
C5: 220uF; E5-8,5
C6: 22pF; C0805
C7: C-EUC1812; C1812
CC-DEBUG: MA05-2
DBG: MA05-1
RASPI, RASPI2: MA05-2
RX_1: JUMPER-SMT_3_1-NC_TRACE_SILK; SMT-JUMPER_3_1-NC_TRACE_SILK
RX_SEL: JUMPER-SMT_3_1-NC_TRACE_SILK; SMT-JUMPER_3_1-NC_TRACE_SILK
TX_1: JUMPER-SMT_3_1-NC_TRACE_SILK; SMT-JUMPER_3_1-NC_TRACE_SILK
TX_SEL: JUMPER-SMT_3_1-NC_TRACE_SILK; SMT-JUMPER_3_1-NC_TRACE_SILK
U$1: CC2530CC2530PA; CC2530PA
U$3: CC2530_MODULE; CC2530_DIL
UART0, UART1: MA04-1

Connections:
BT: U$1.P$6 (P2.0)
CCRX: TX_1.2, U$1.P$21 (P0.2), U$3.P0_2\U_RX
CCTX: RX_1.2, U$1.P$20 (P0.3), U$3.P0_3\U_TX
CS: CC-DEBUG.5
DC: CC-DEBUG.3, U$1.P$8 (P2.2), U$3.P2_2
DD: CC-DEBUG.4, U$1.P$7 (P2.1), U$3.P2_1
GND: C5.-, C6.2, C7.1, CC-DEBUG.1, DBG.5, RASPI.6, RASPI.9, RASPI2.6, RASPI2.9, U$1.P$11 (GND2), U$1.P$12 (GND), U$3.GND, U$3.GND2, UART0.4, UART1.4
IN2: DBG.1
MISO: CC-DEBUG.10
MOSI: CC-DEBUG.8
RST: CC-DEBUG.7, U$1.P$24 (RESET_N), U$3.RST
RX: RASPI.10, TX_SEL.2
RX0: RASPI2.10, RX_1.3, RX_SEL.1, UART0.3
RX1: RX_1.1, RX_SEL.3, UART1.3
RX_DBG: DBG.4
SCLK: CC-DEBUG.6
TX: RASPI.8, RX_SEL.2
TX0: RASPI2.8, TX_1.3, TX_SEL.1, UART0.2
TX1: TX_1.1, TX_SEL.3, UART1.2
TX_DBG: DBG.3
VCC: C5.+, C6.1, C7.2, CC-DEBUG.2, CC-DEBUG.9, DBG.2, RASPI.1, RASPI2.1, U$1.P$9 (VCC2), U$1.P$10 (VCC), U$3.VCC, U$3.VCC2, UART0.1, UART1.1

Notes on the sheet:
Opt
siehe Homematic
siehe MySensors
1 3V3 6 GND 8 TXD 9 GND 10 RXD
RX/TX from MAPLE Side !
History: TX0 mit TX1 getauscht Footprint CC2530 fixed
Volt-Sense
SZ1Zigeebee Module: https://de.aliexpress.com/item/CC2530-wireless-module-Zigbee-module/1861120386.html
